DvidMakesThings/HW_PDNode-600-Pro/src/HardwareDesign/1.0.0/PDNode-600_Pro_Baseboard_100/jlcpcb/Documentation/_TopCover.pdf

# Baseboard Schematic Documentation

# Top Preview

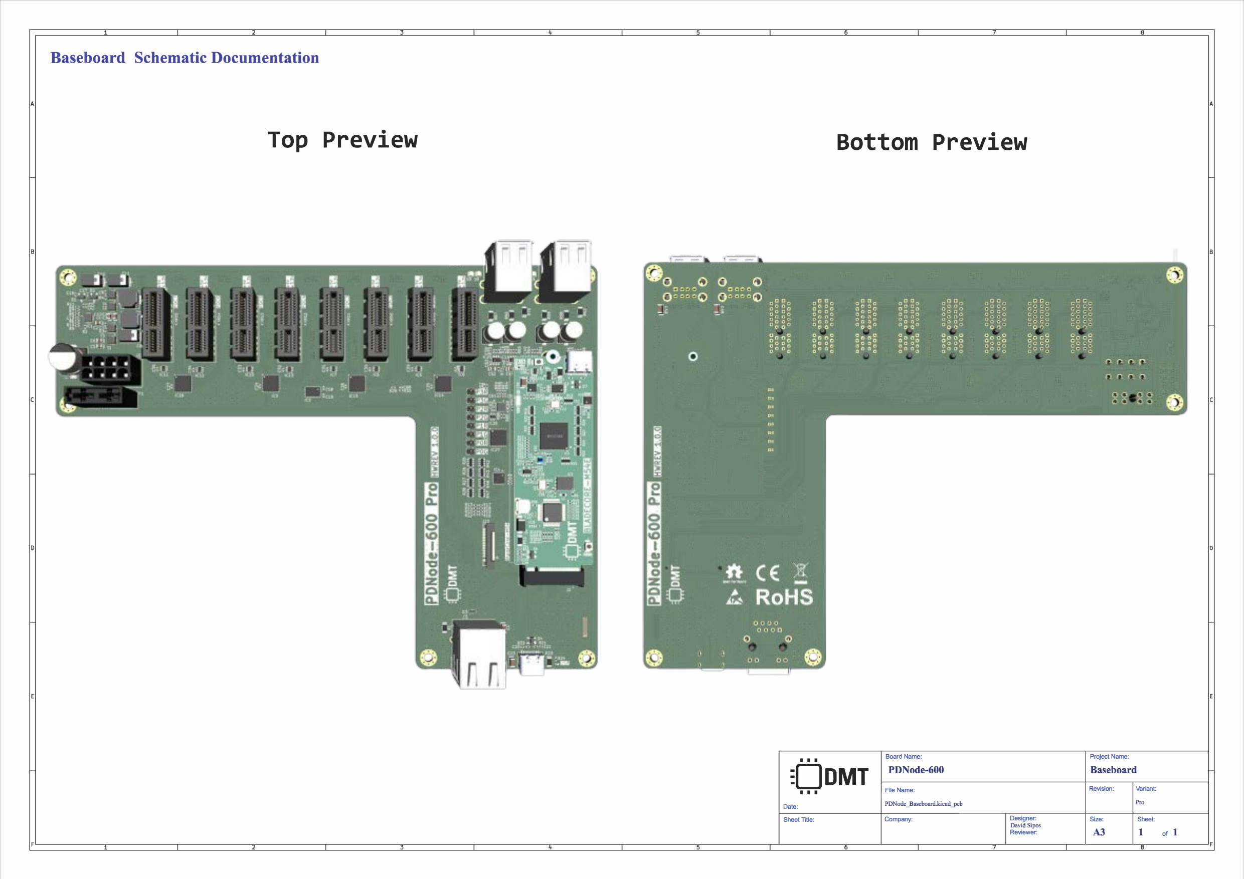
[picture p11: page 1]

2 | 3

A

C

2 | 3
6 | 7

# Bottom Preview

I I I

# :ODMT

I I I

Date:

Sheet Title:

6

Board Name:
PDNode-600

File Name:

PD Node_ Baseboard.kicad _pcb

Company:

7

Designer:
David Sipos
Reviewer:

A

B

D

Project Name:
Baseboard
Revision: | Variant:
| Pro
Size: | Sheet:
A3 | 1 | of 1

8
