DvidMakesThings/HW_PDNode-600-Pro/images/0.1.0/3D/PDNode-600 Pro-2.png

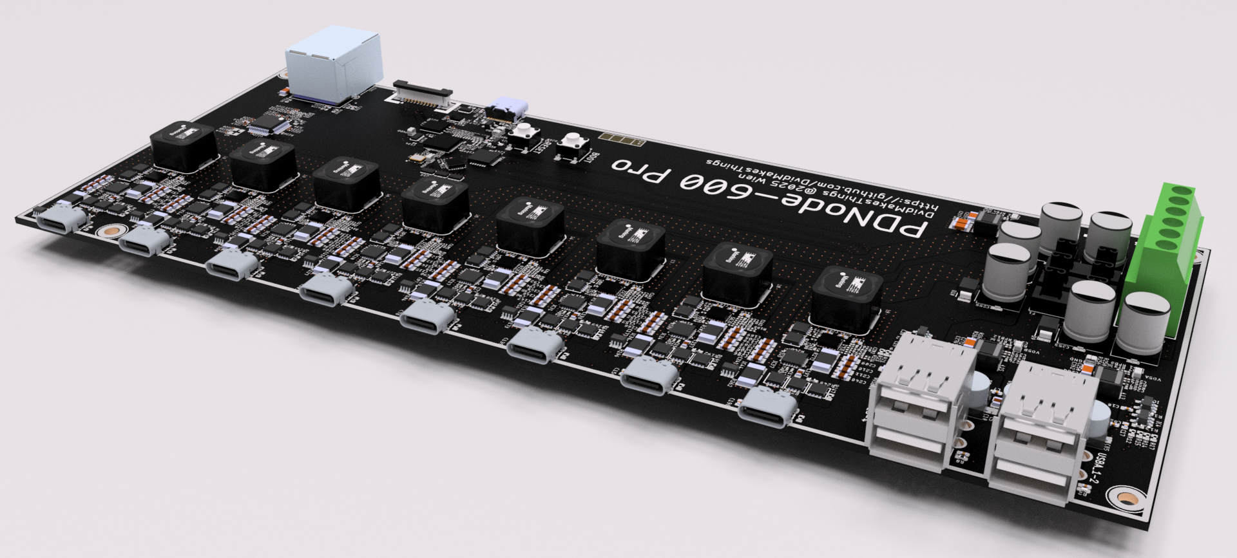
images/0.1.0/3D/PDNode-600 Pro-2.png
