DvidMakesThings/HW_PDNode-600-Pro/images/0.1.0/PDNode-600 Pro-Btm.png

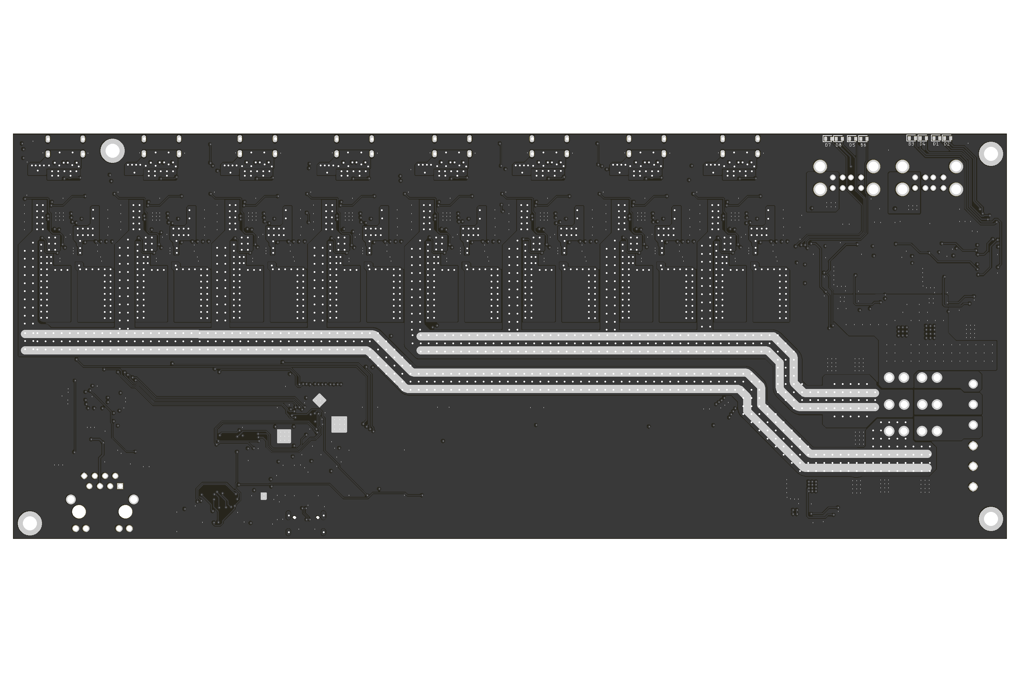
images/0.1.0/PDNode-600 Pro-Btm.png
