DvidMakesThings/HW_PDNode-600-Pro/images/1.0.0/BladeCore-M54E_Top.png

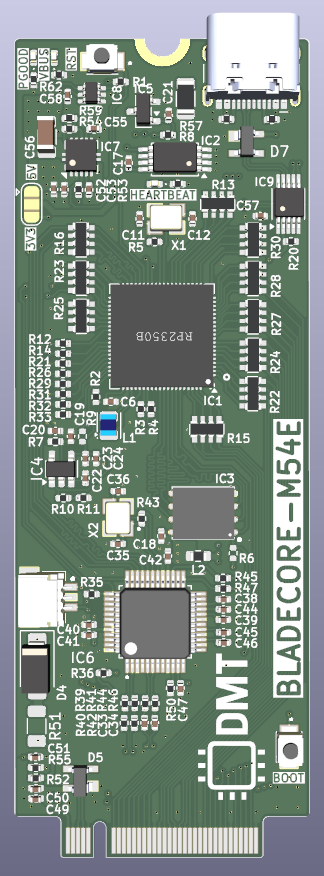
images/1.0.0/BladeCore-M54E_Top.png
