DvidMakesThings/HW_PDNode-600-Pro/images/PDNode-600 Pro Enclosure v19.png

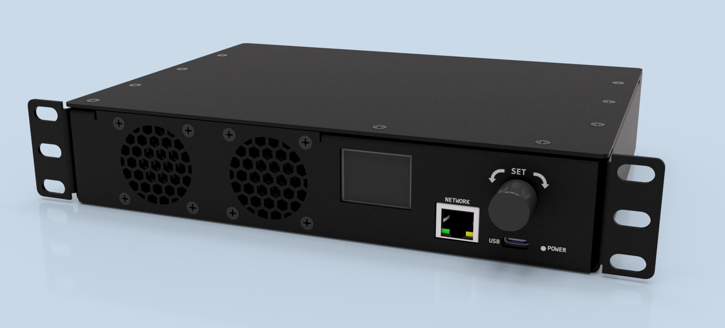
images/PDNode-600 Pro Enclosure v19.png
