DvidMakesThings/HW_PDNode-600-Pro/images/PDNode-600 Pro Enclosure v162.png

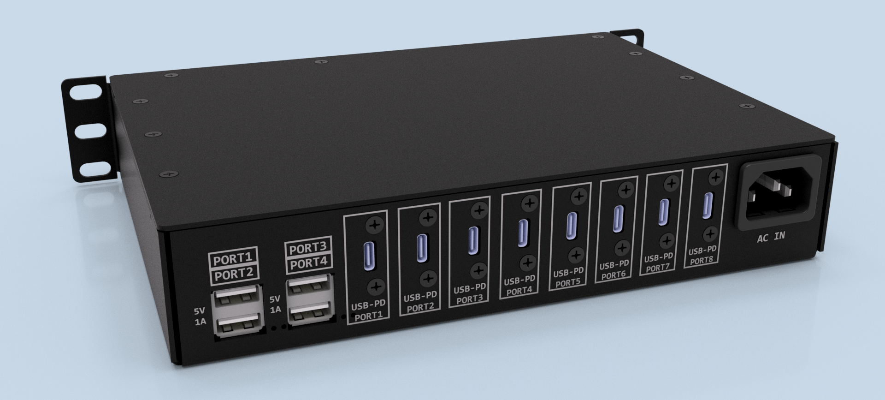
images/PDNode-600 Pro Enclosure v162.png
