DvidMakesThings/HW_PDNode-600-Pro/src/HardwareDesign/1.0.0/BladeCore-M54_100/Images/BladeCore-M54E_Top-removebg.png

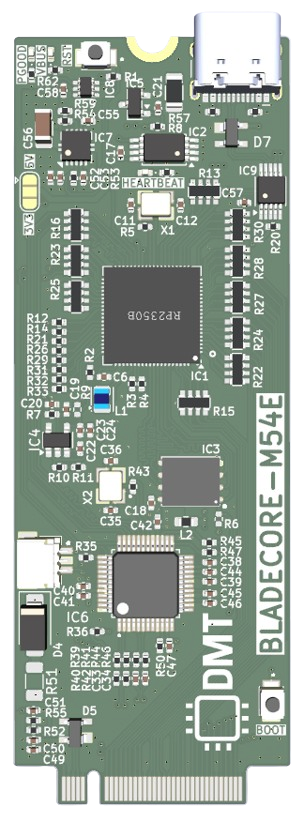
src/HardwareDesign/1.0.0/BladeCore-M54_100/Images/BladeCore-M54E_Top-removebg.png
