DvidMakesThings/HW_PDNode-600-Pro/src/HardwareDesign/1.0.0/PDCard-4242_100/Images/PDNode-PDCard-4242_TOP-removebg-preview.png

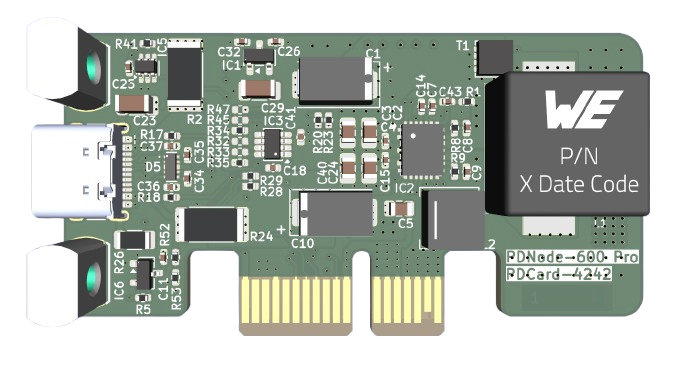
src/HardwareDesign/1.0.0/PDCard-4242_100/Images/PDNode-PDCard-4242_TOP-removebg-preview.png
