DvidMakesThings/HW_PDNode-600-Pro/src/HardwareDesign/1.0.0/PDNode-600_Pro_Baseboard_100/Images/PDNode_Baseboard-Bottom.png

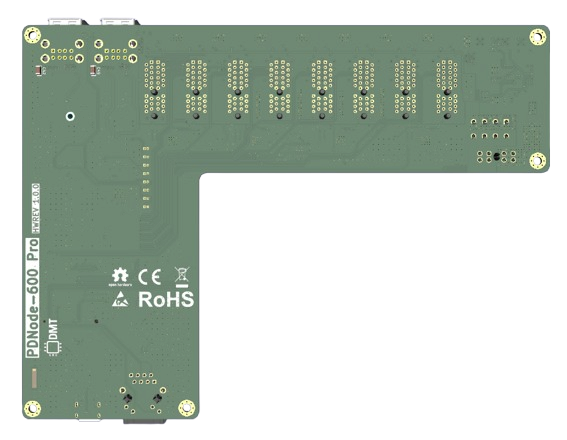
src/HardwareDesign/1.0.0/PDNode-600_Pro_Baseboard_100/Images/PDNode_Baseboard-Bottom.png
