DvidMakesThings/HW_PDNode-600-Pro/src/PDF/SCH_PDCard-4242_100.pdf

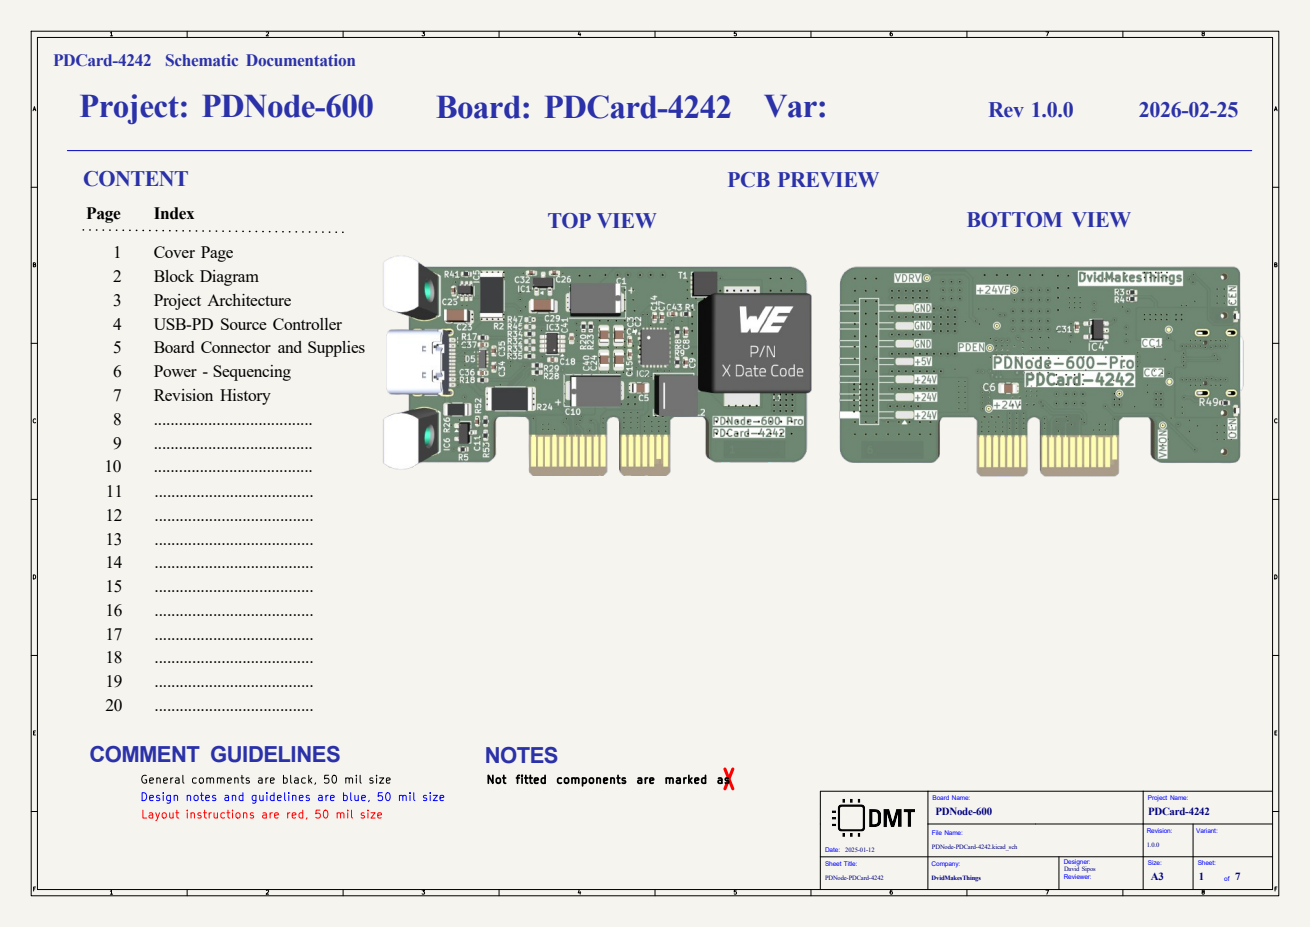
[picture p39: page 1]

...................................... Design notes and guidelines are blue, 50 mil size

General comments are black, 50 mil size

Layout instructions are red, 50 mil size

File Name: Sheet Title: PDNode-PDCard-4242

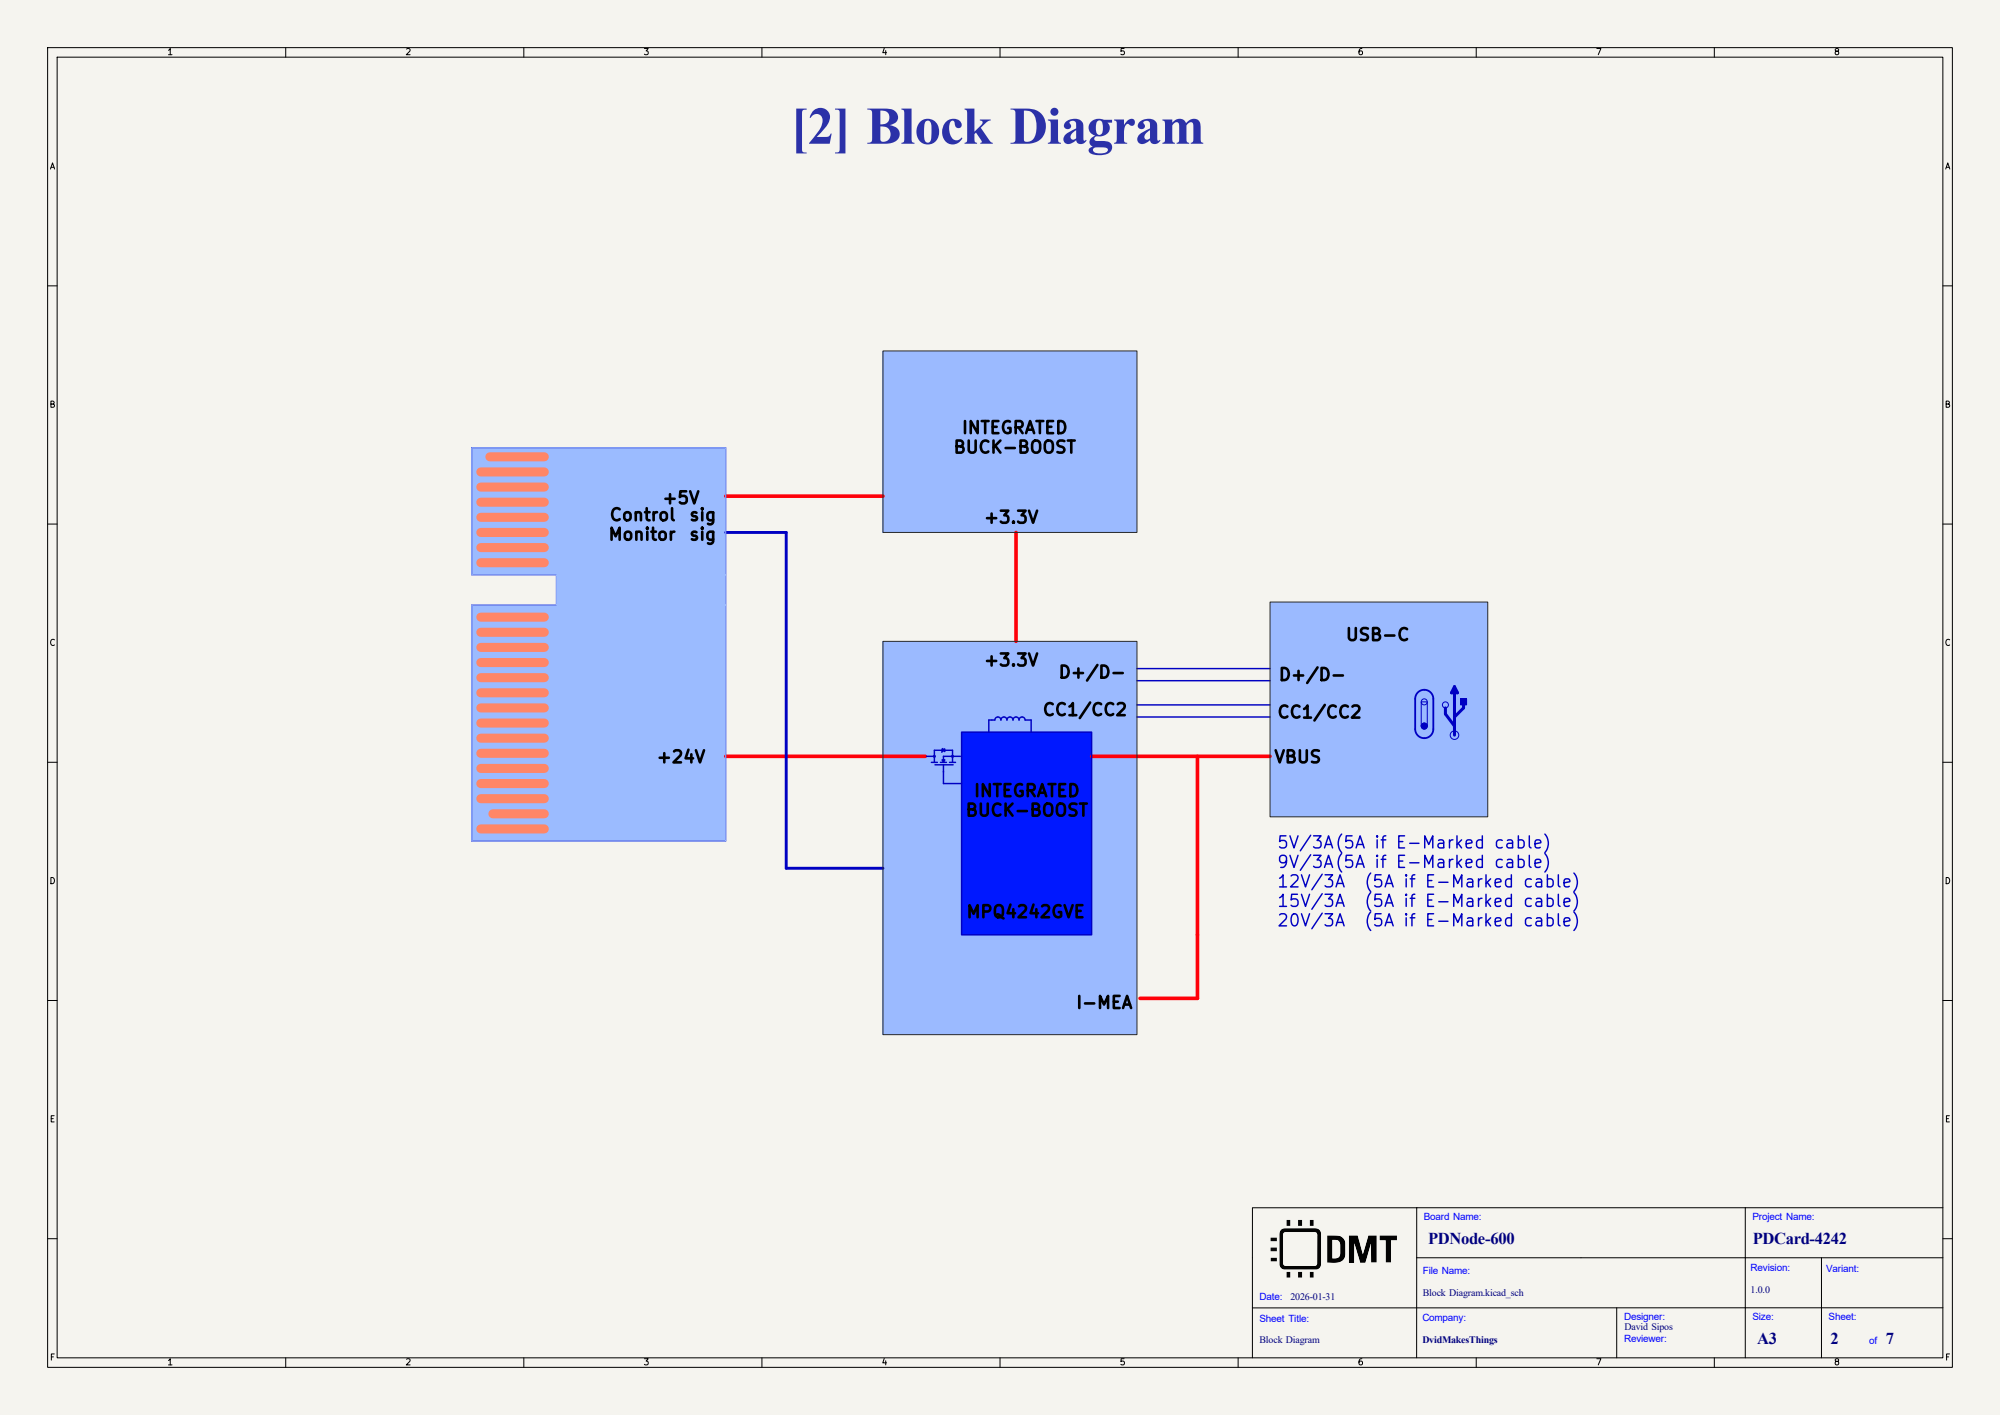
[picture p40: page 2]

File Name: Sheet Title: Block Diagram

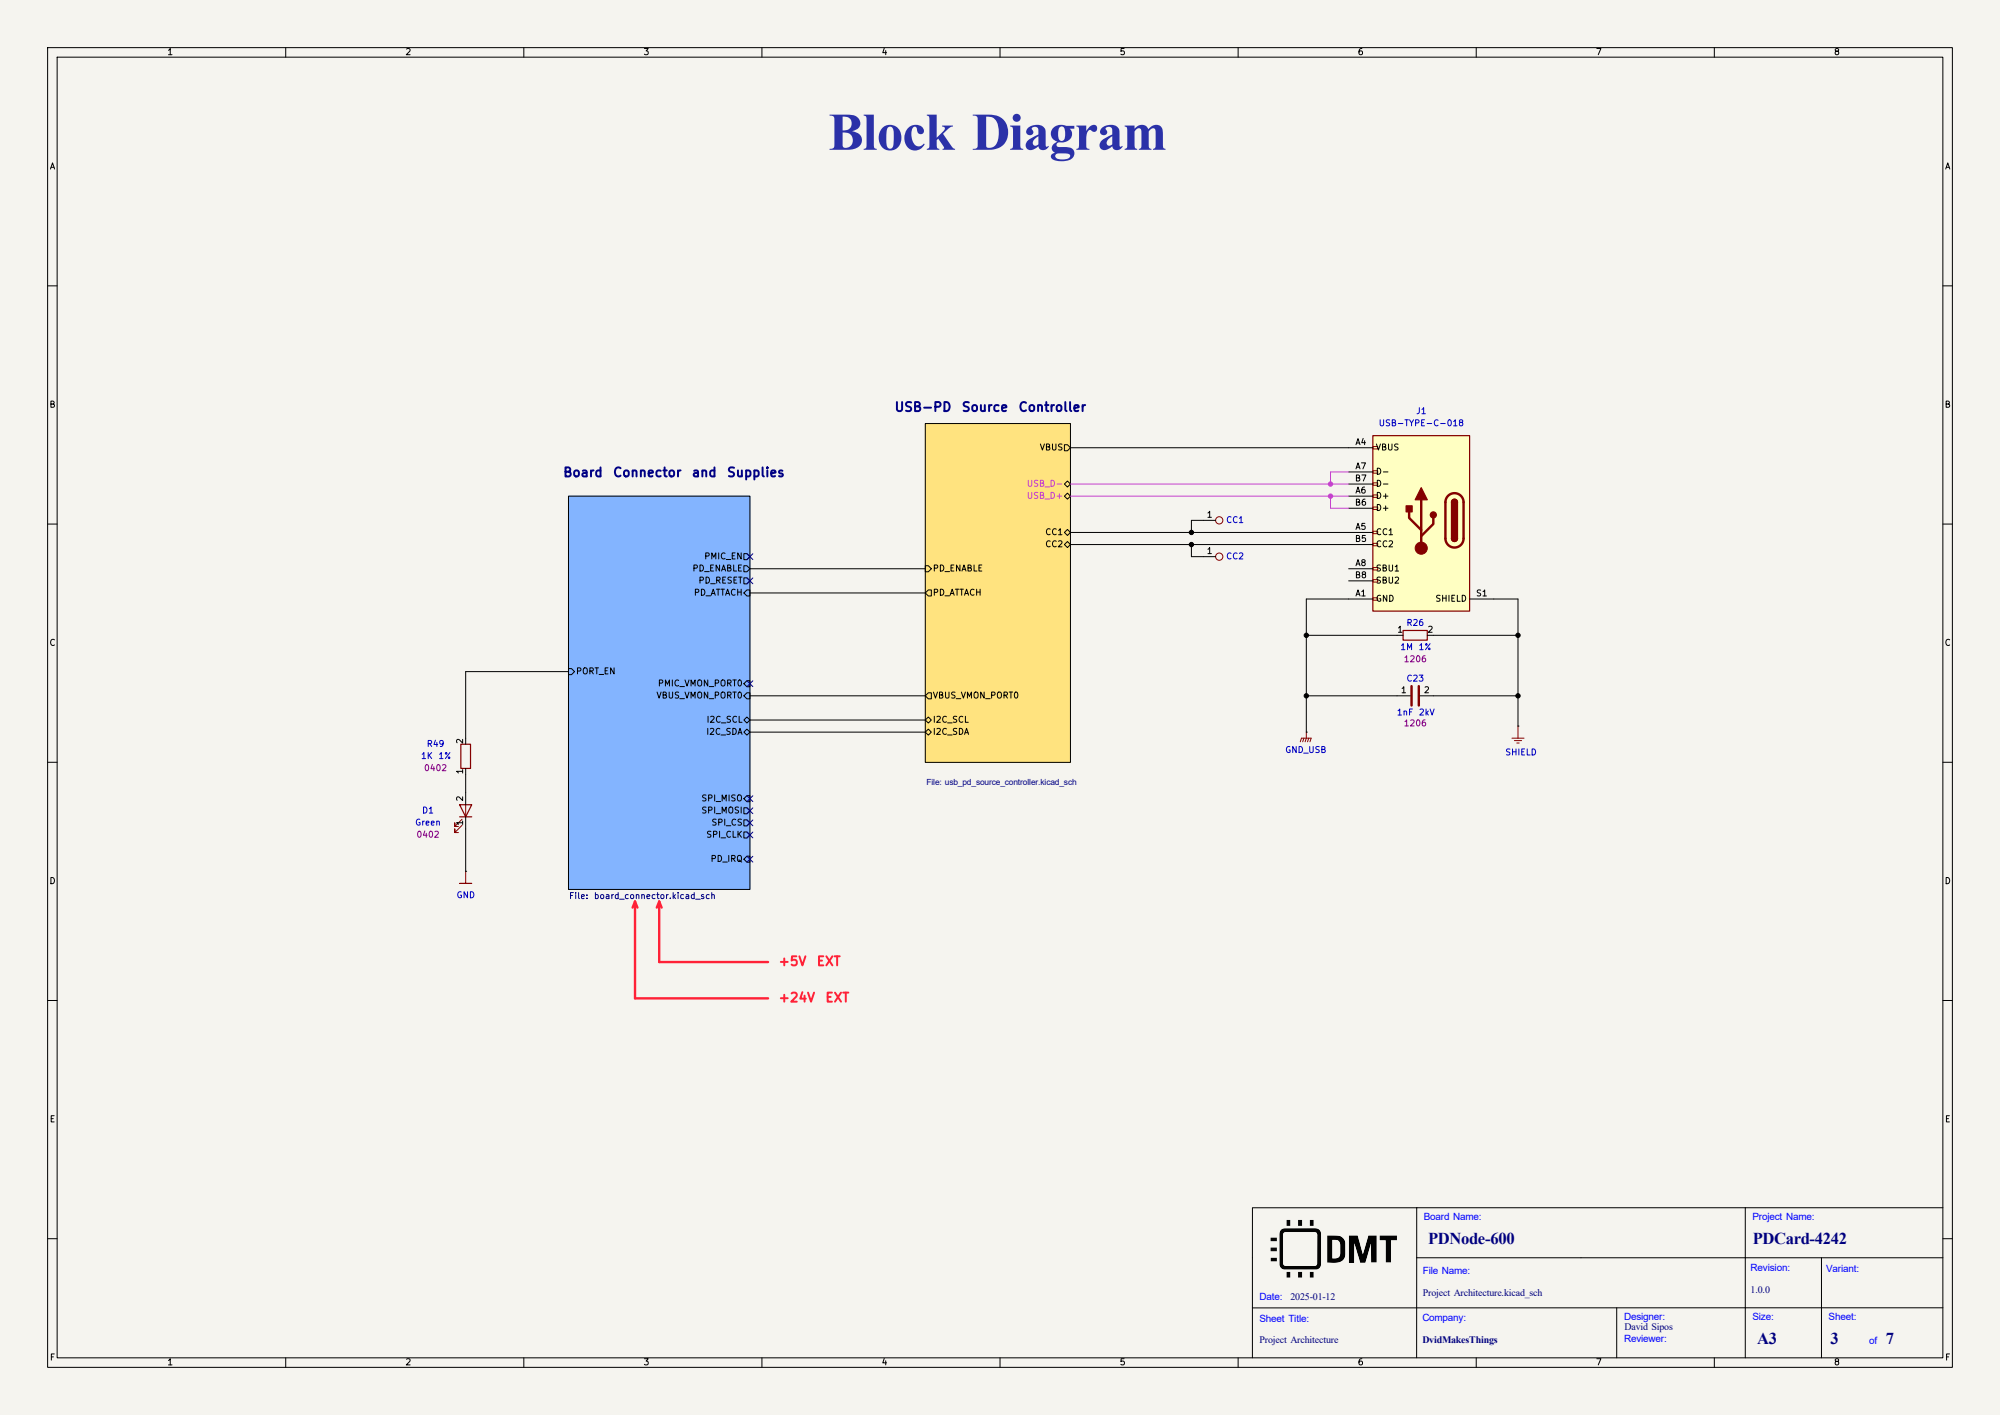
[picture p41: page 3]

VBUS_VMON_PORT0 USB-PD Source Controller

PD_ENABLE Board Connector and Supplies

File Name: Sheet Title: Project Architecture

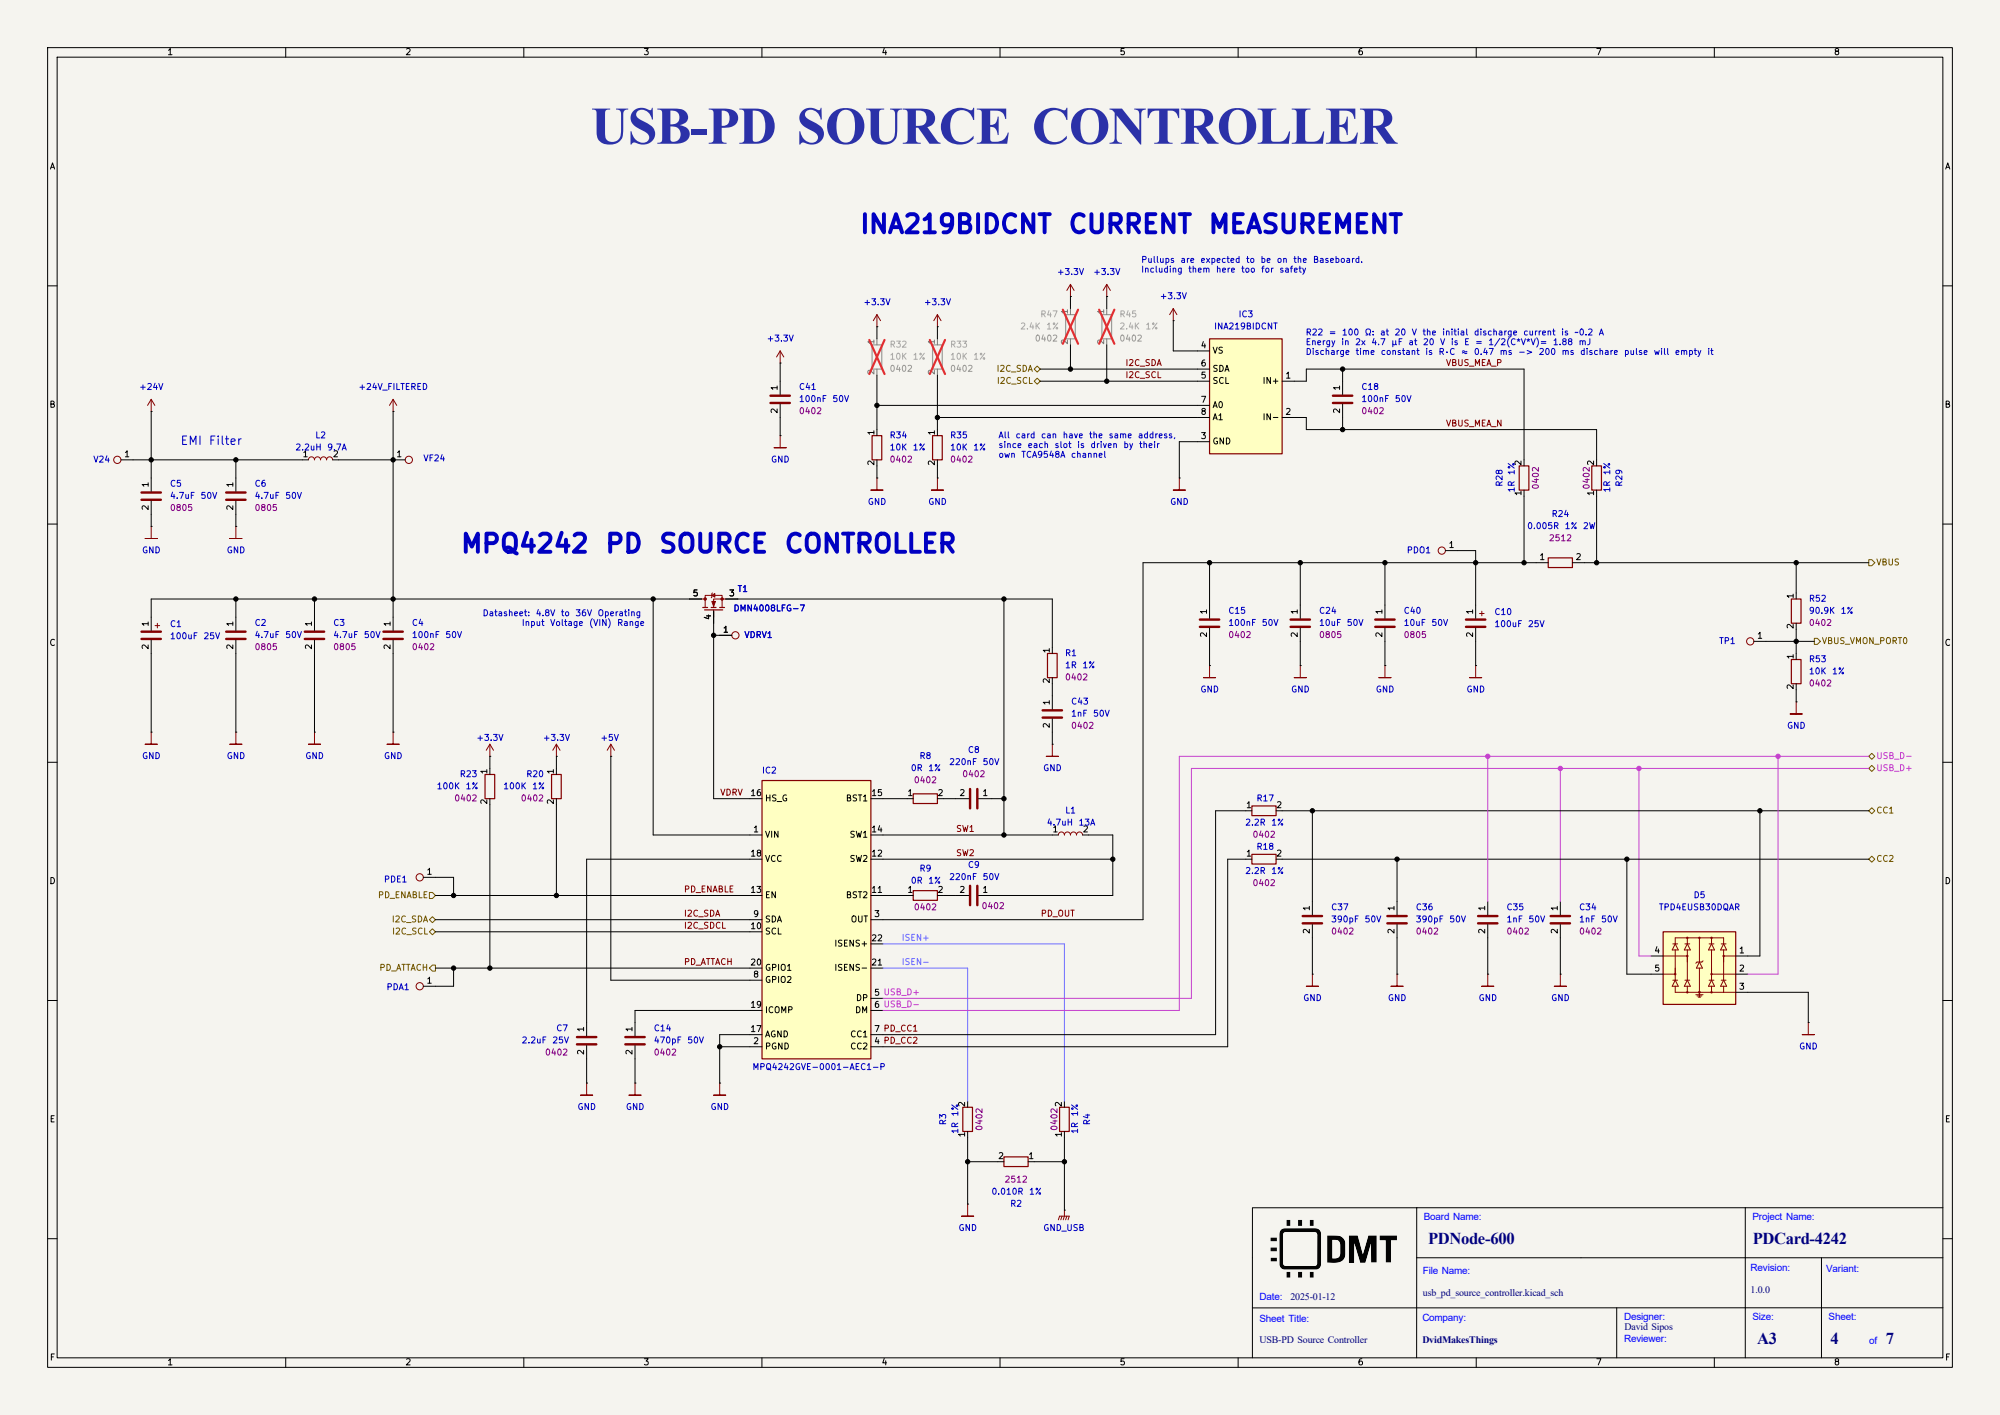
[picture p42: page 4]

R22 = 100 Ω: at 20 V the initial discharge current is ~0.2 A Energy in 2x 4.7 µF at 20 V is E = 1/2(C*V*V)= 1.88 mJ Discharge time constant is R·C ≈ 0.47 ms -> 200 ms dischare pulse will empty it INA219BIDCNT CURRENT MEASUREMENT

Pullups are expected to be on the Baseboard.
Including them here too for safety

All card can have the same address, since each slot is driven by their own TCA9548A channel EMI Filter

Input Voltage (VIN) Range
IC2 MPQ4242GVE-0001-AEC1-P

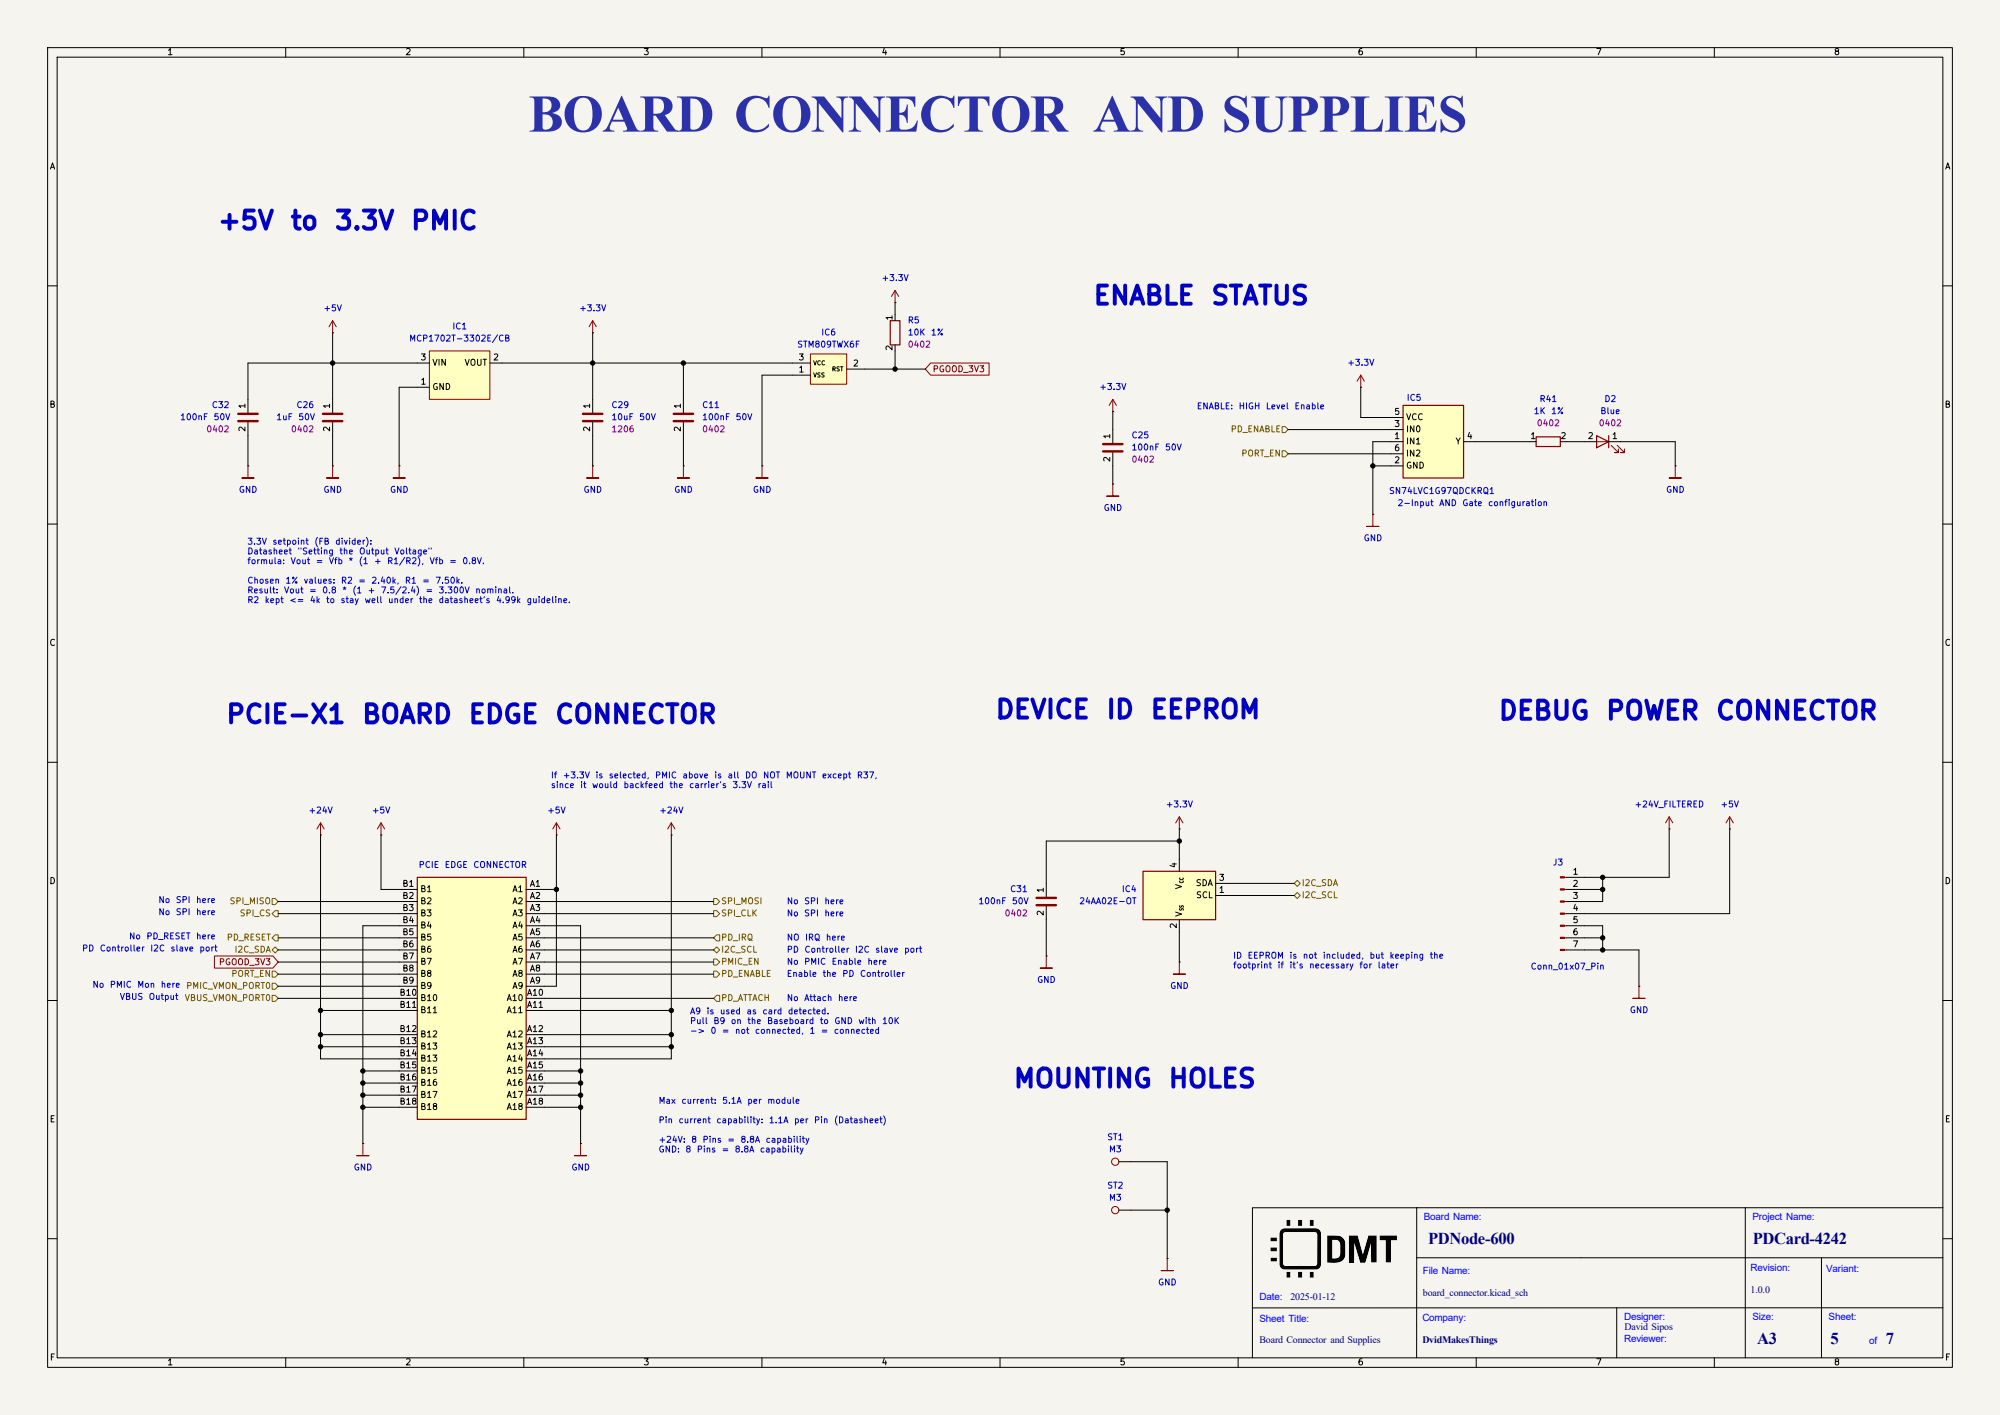
[picture p43: page 5]

ENABLE: HIGH Level Enable PD Controller I2C slave port

2-Input AND Gate configuration

NO IRQ here 3.3V setpoint (FB divider):
Datasheet "Setting the Output Voltage"
formula: Vout = Vfb * (1 + R1/R2), Vfb = 0.8V.

Chosen 1% values: R2 = 2.40k, R1 = 7.50k.
Result: Vout = 0.8 * (1 + 7.5/2.4) = 3.300V nominal.
R2 kept <= 4k to stay well under the datasheet's 4.99k guideline.

footprint if it's necessary for later DEVICE ID EEPROM

No SPI here No PD_RESET here PD Controller I2C slave port

No PMIC Mon here

A9 is used as card detected. Pull B9 on the Baseboard to GND with 10K -> 0 = not connected, 1 = connected Max current: 5.1A per module Pin current capability: 1.1A per Pin (Datasheet)

File Name: Sheet Title: Board Connector and Supplies

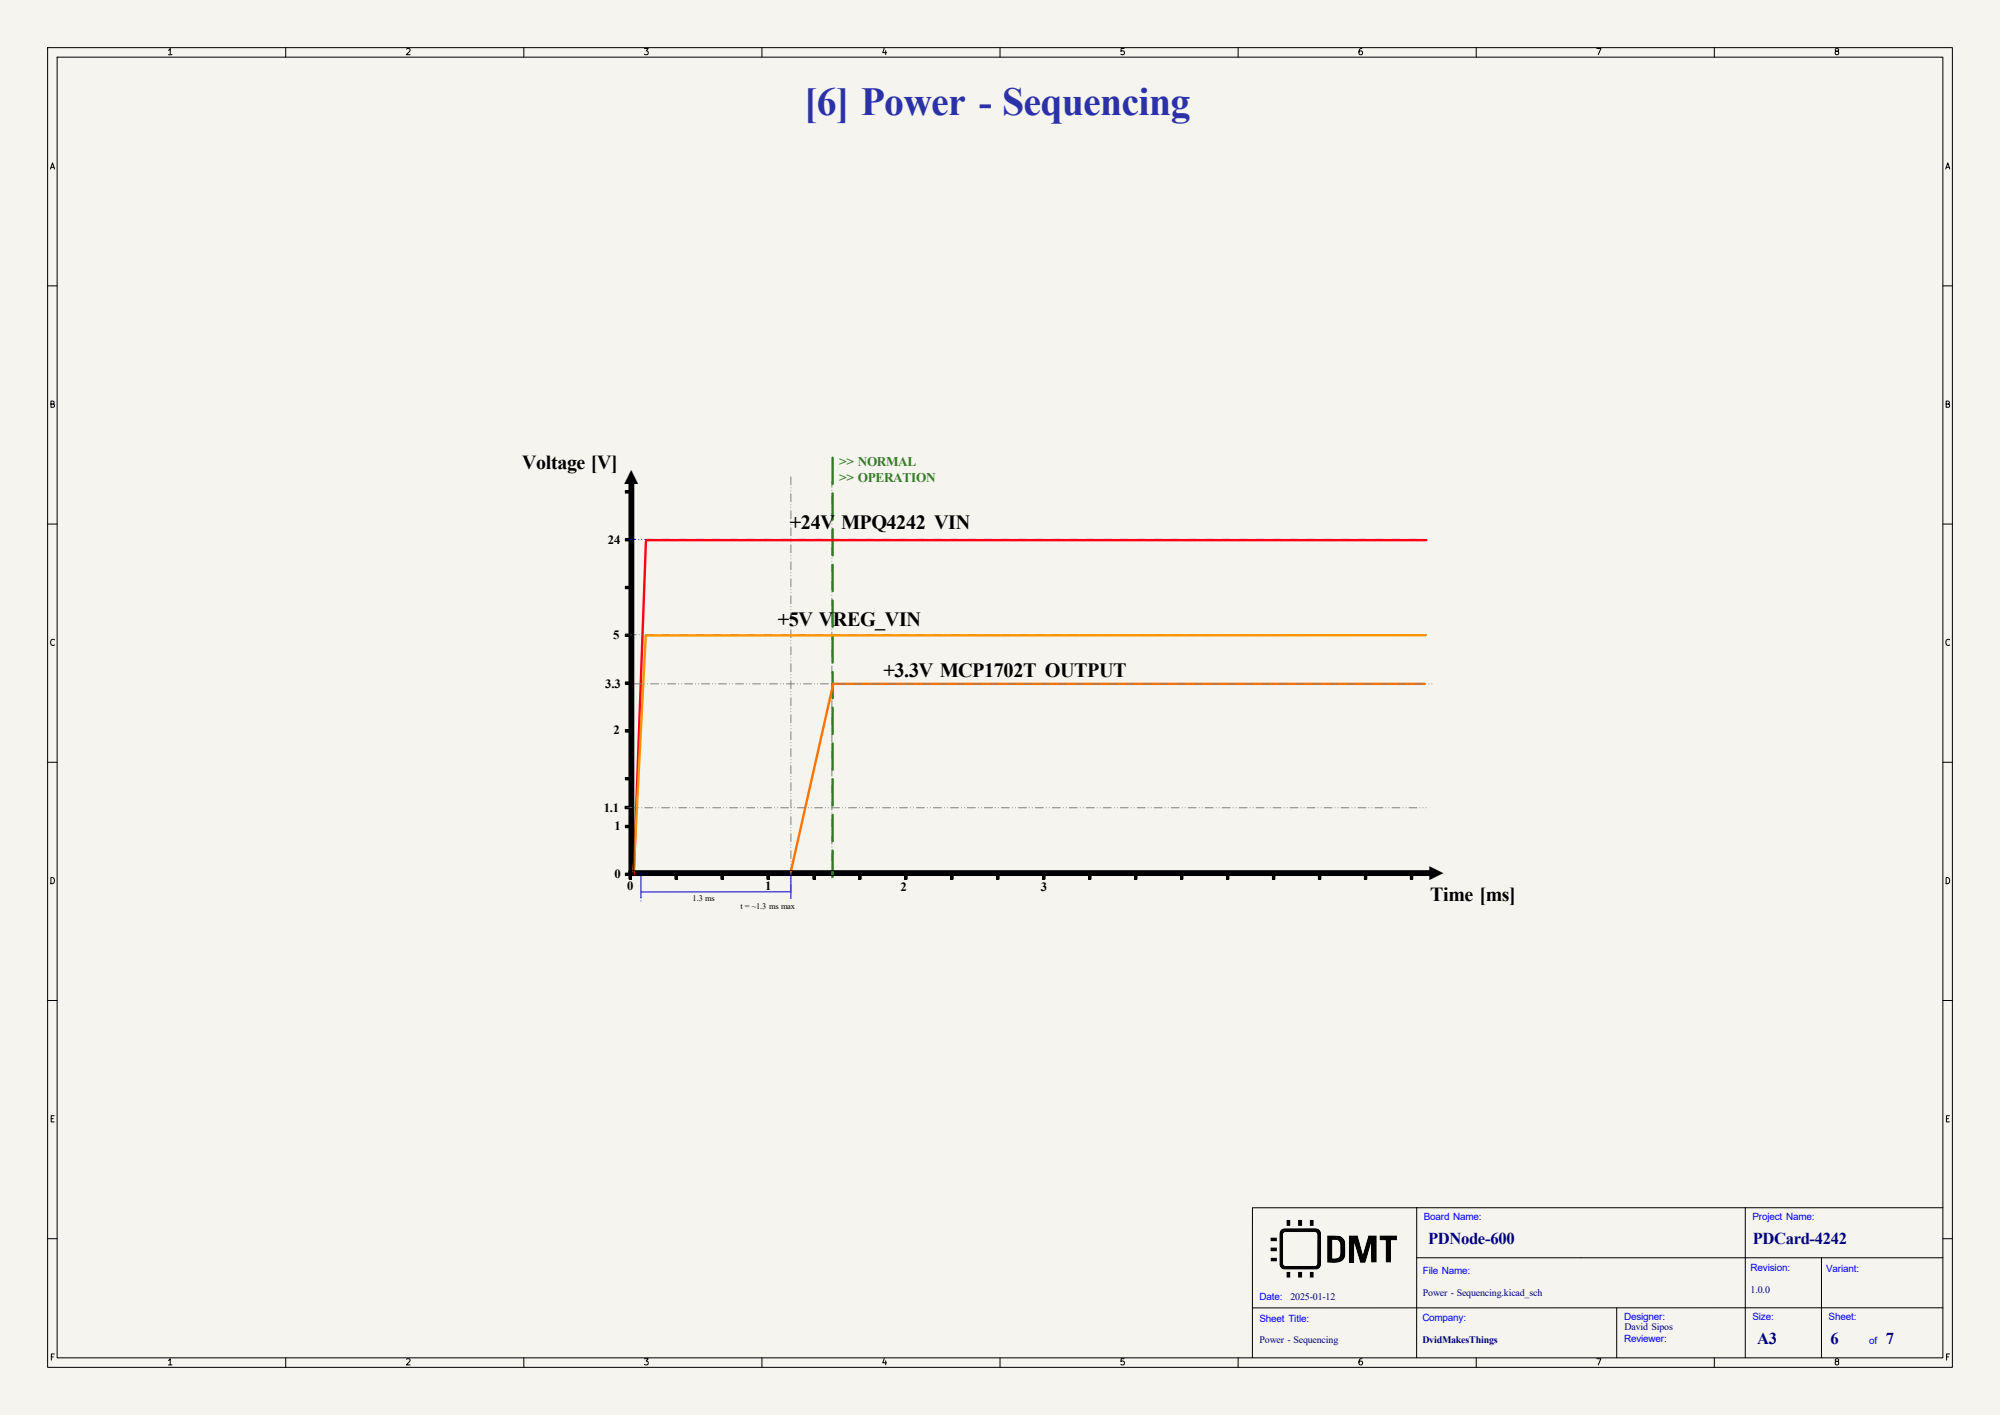
[picture p44: page 6]

File Name: Sheet Title: Power - Sequencing

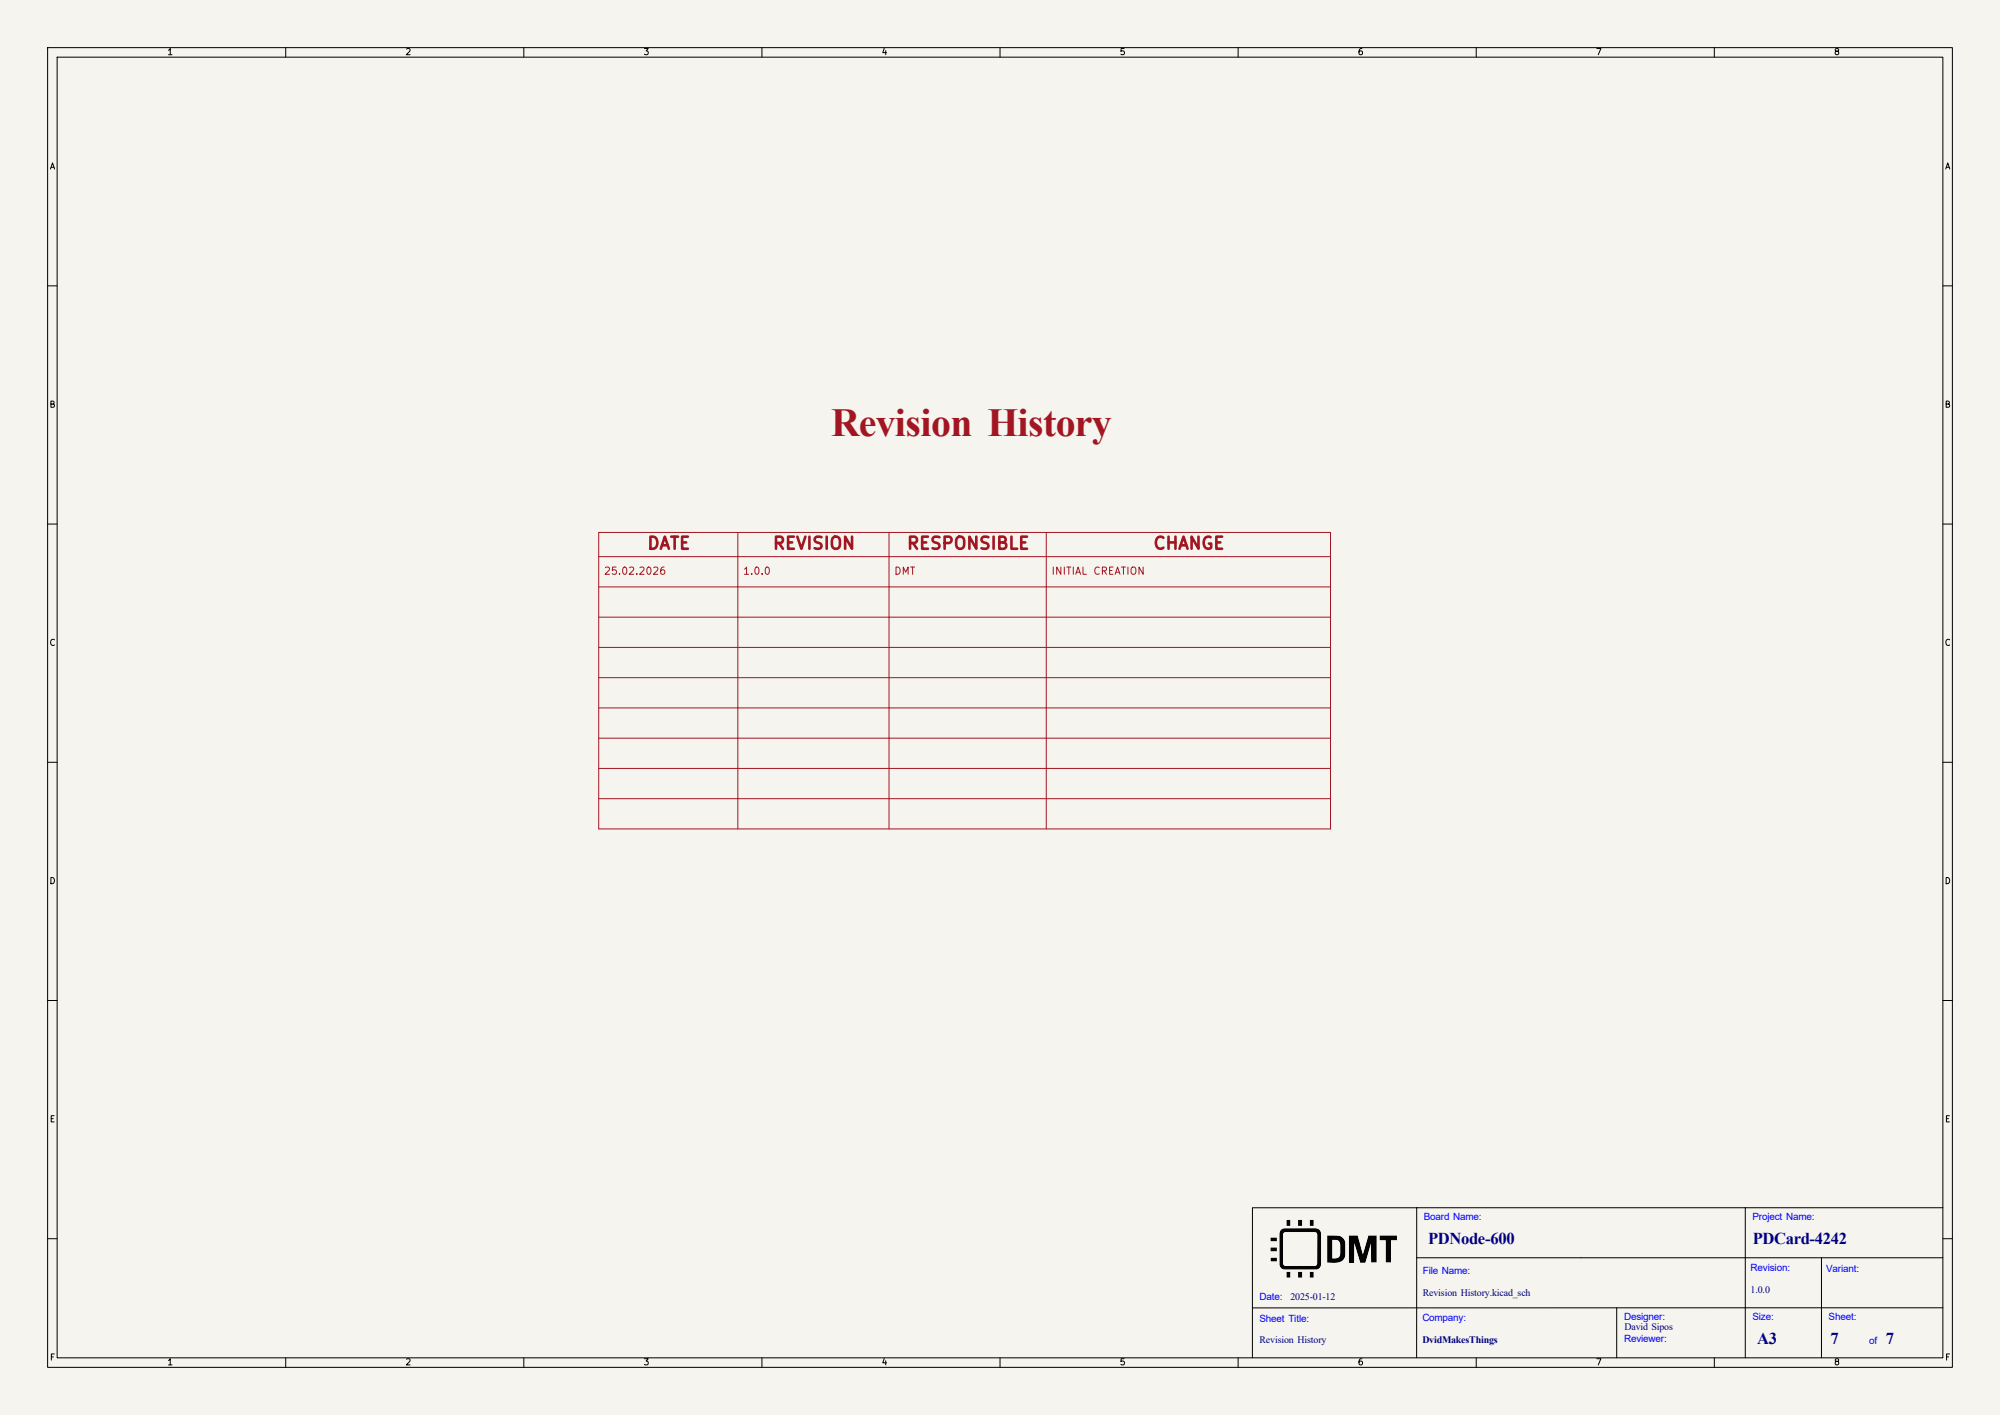
[picture p45: page 7]

File Name: Sheet Title: Revision History
