DvidMakesThings/HW_PDNode-600-Pro/src/PDF/SCH_PDNode_Baseboard_100.pdf

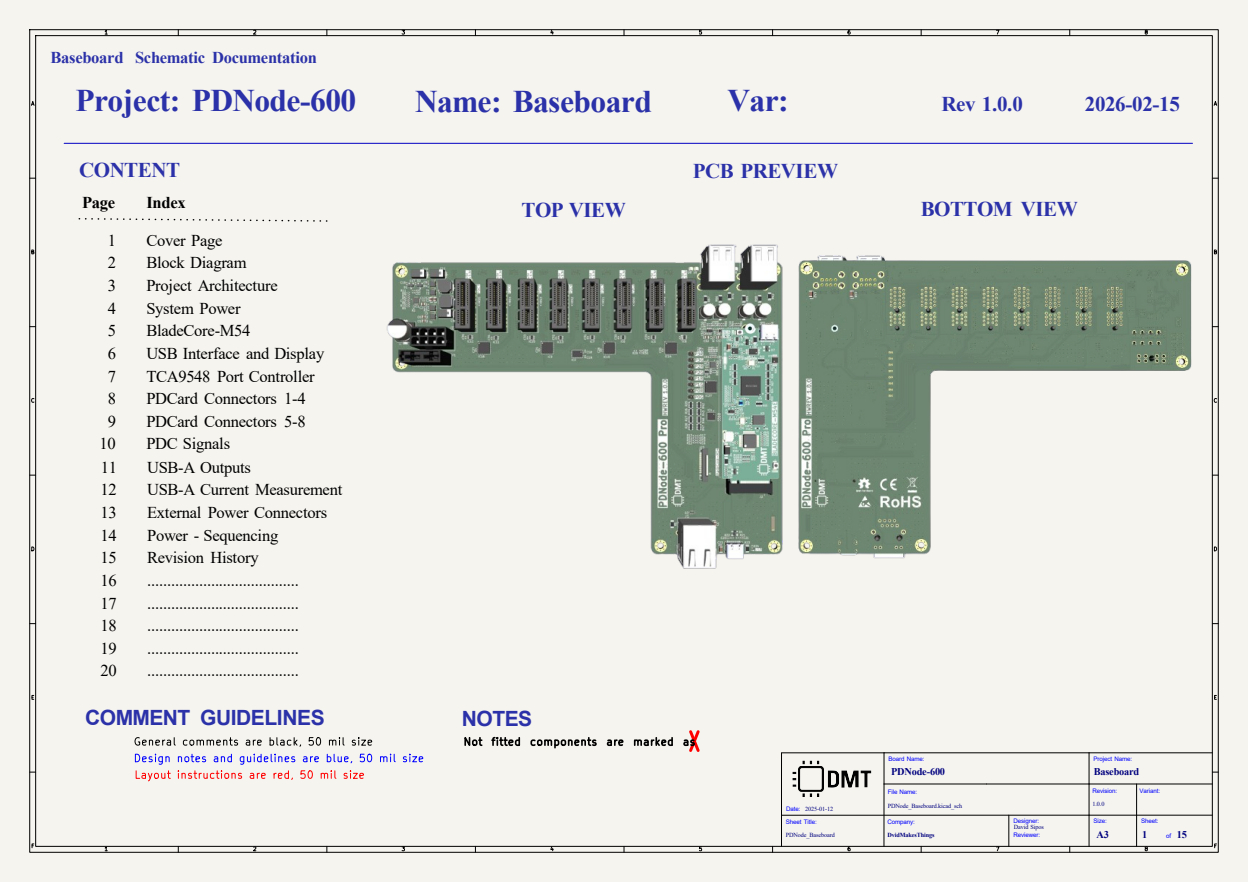
[picture p46: page 1]

General comments are black, 50 mil size
Design notes and guidelines are blue, 50 mil size
Layout instructions are red, 50 mil size

Not fitted components are marked as

File Name: Sheet Title: PDNode_Baseboard

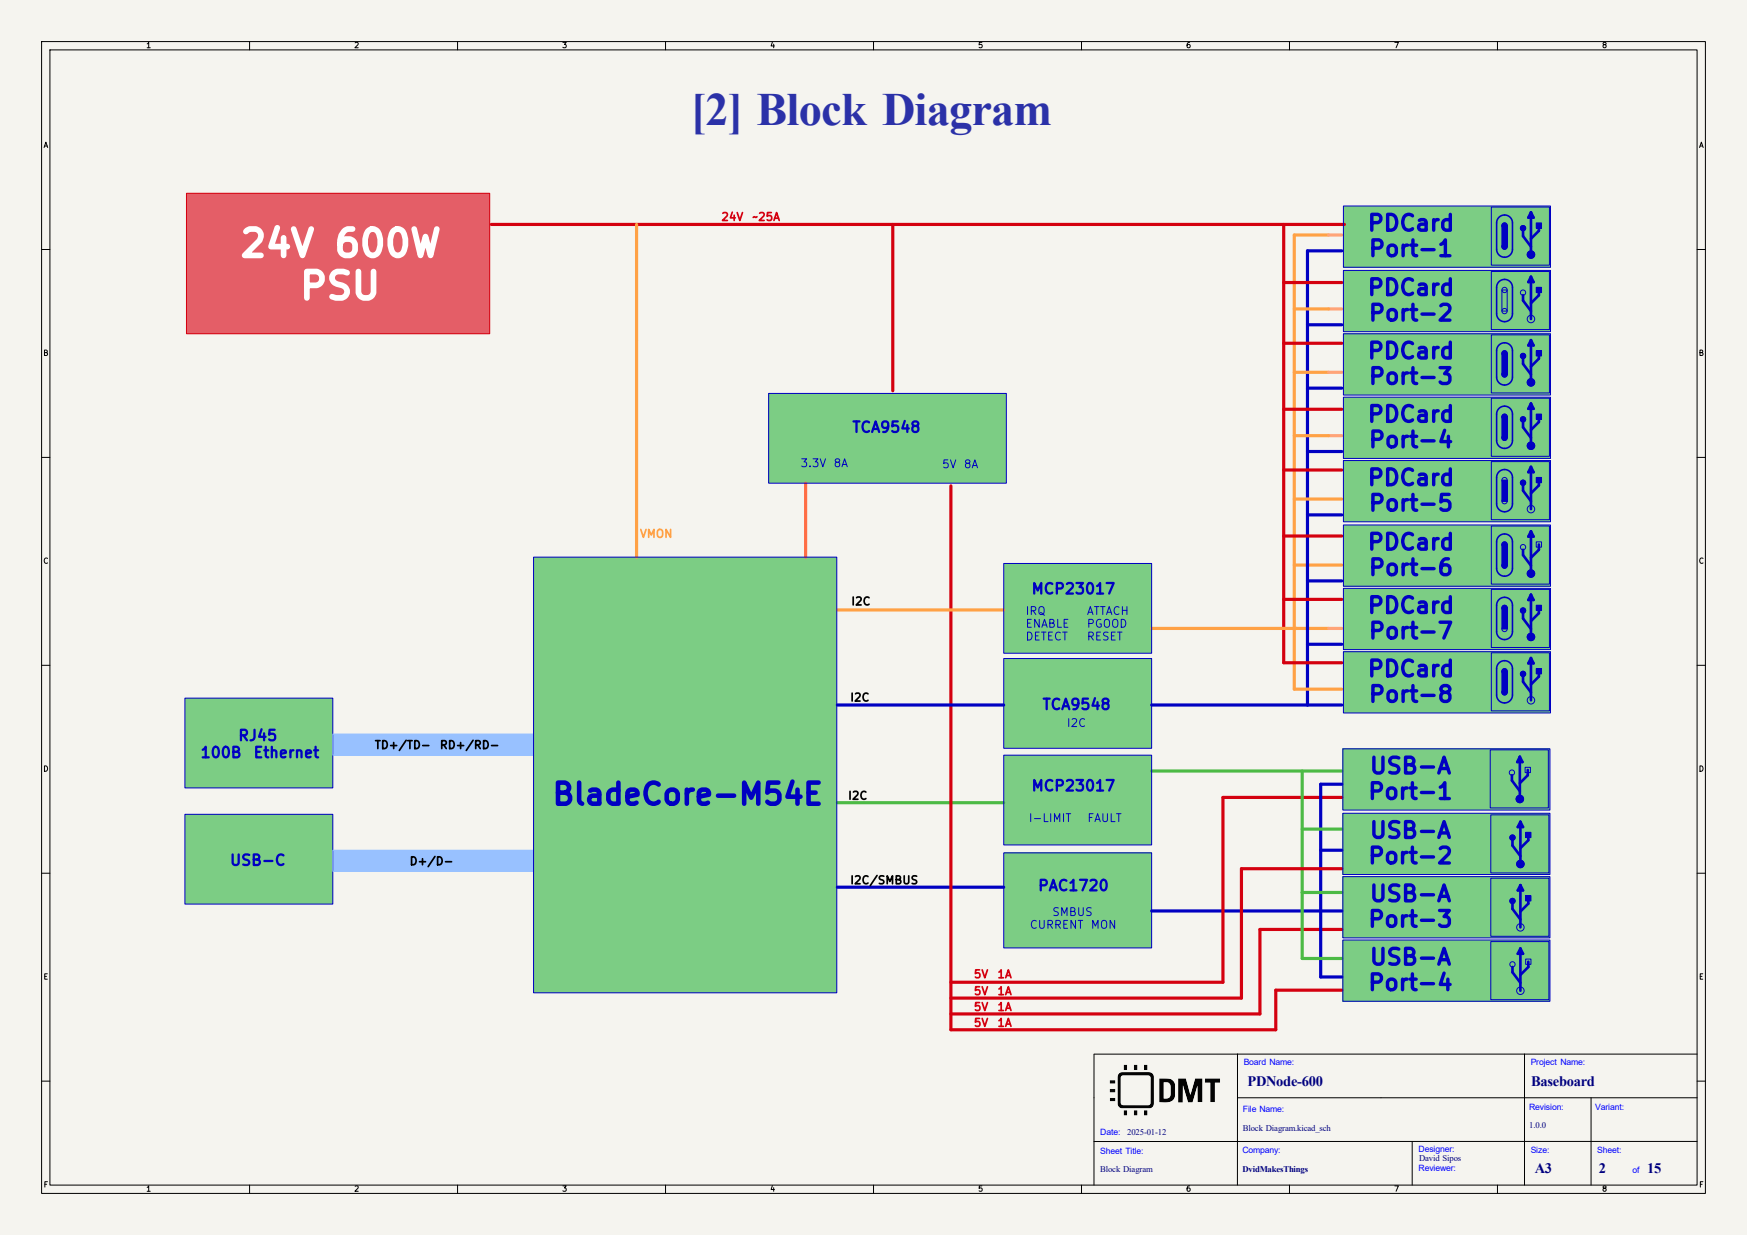
[picture p47: page 2]

PDCard Port-1

PDCard Port-2

PDCard Port-3

PDCard Port-4

PDCard Port-5

PDCard Port-6

PDCard Port-7

PDCard Port-8

I2C/SMBUS

USB-A Port-3

USB-A Port-4

File Name: Sheet Title: Block Diagram

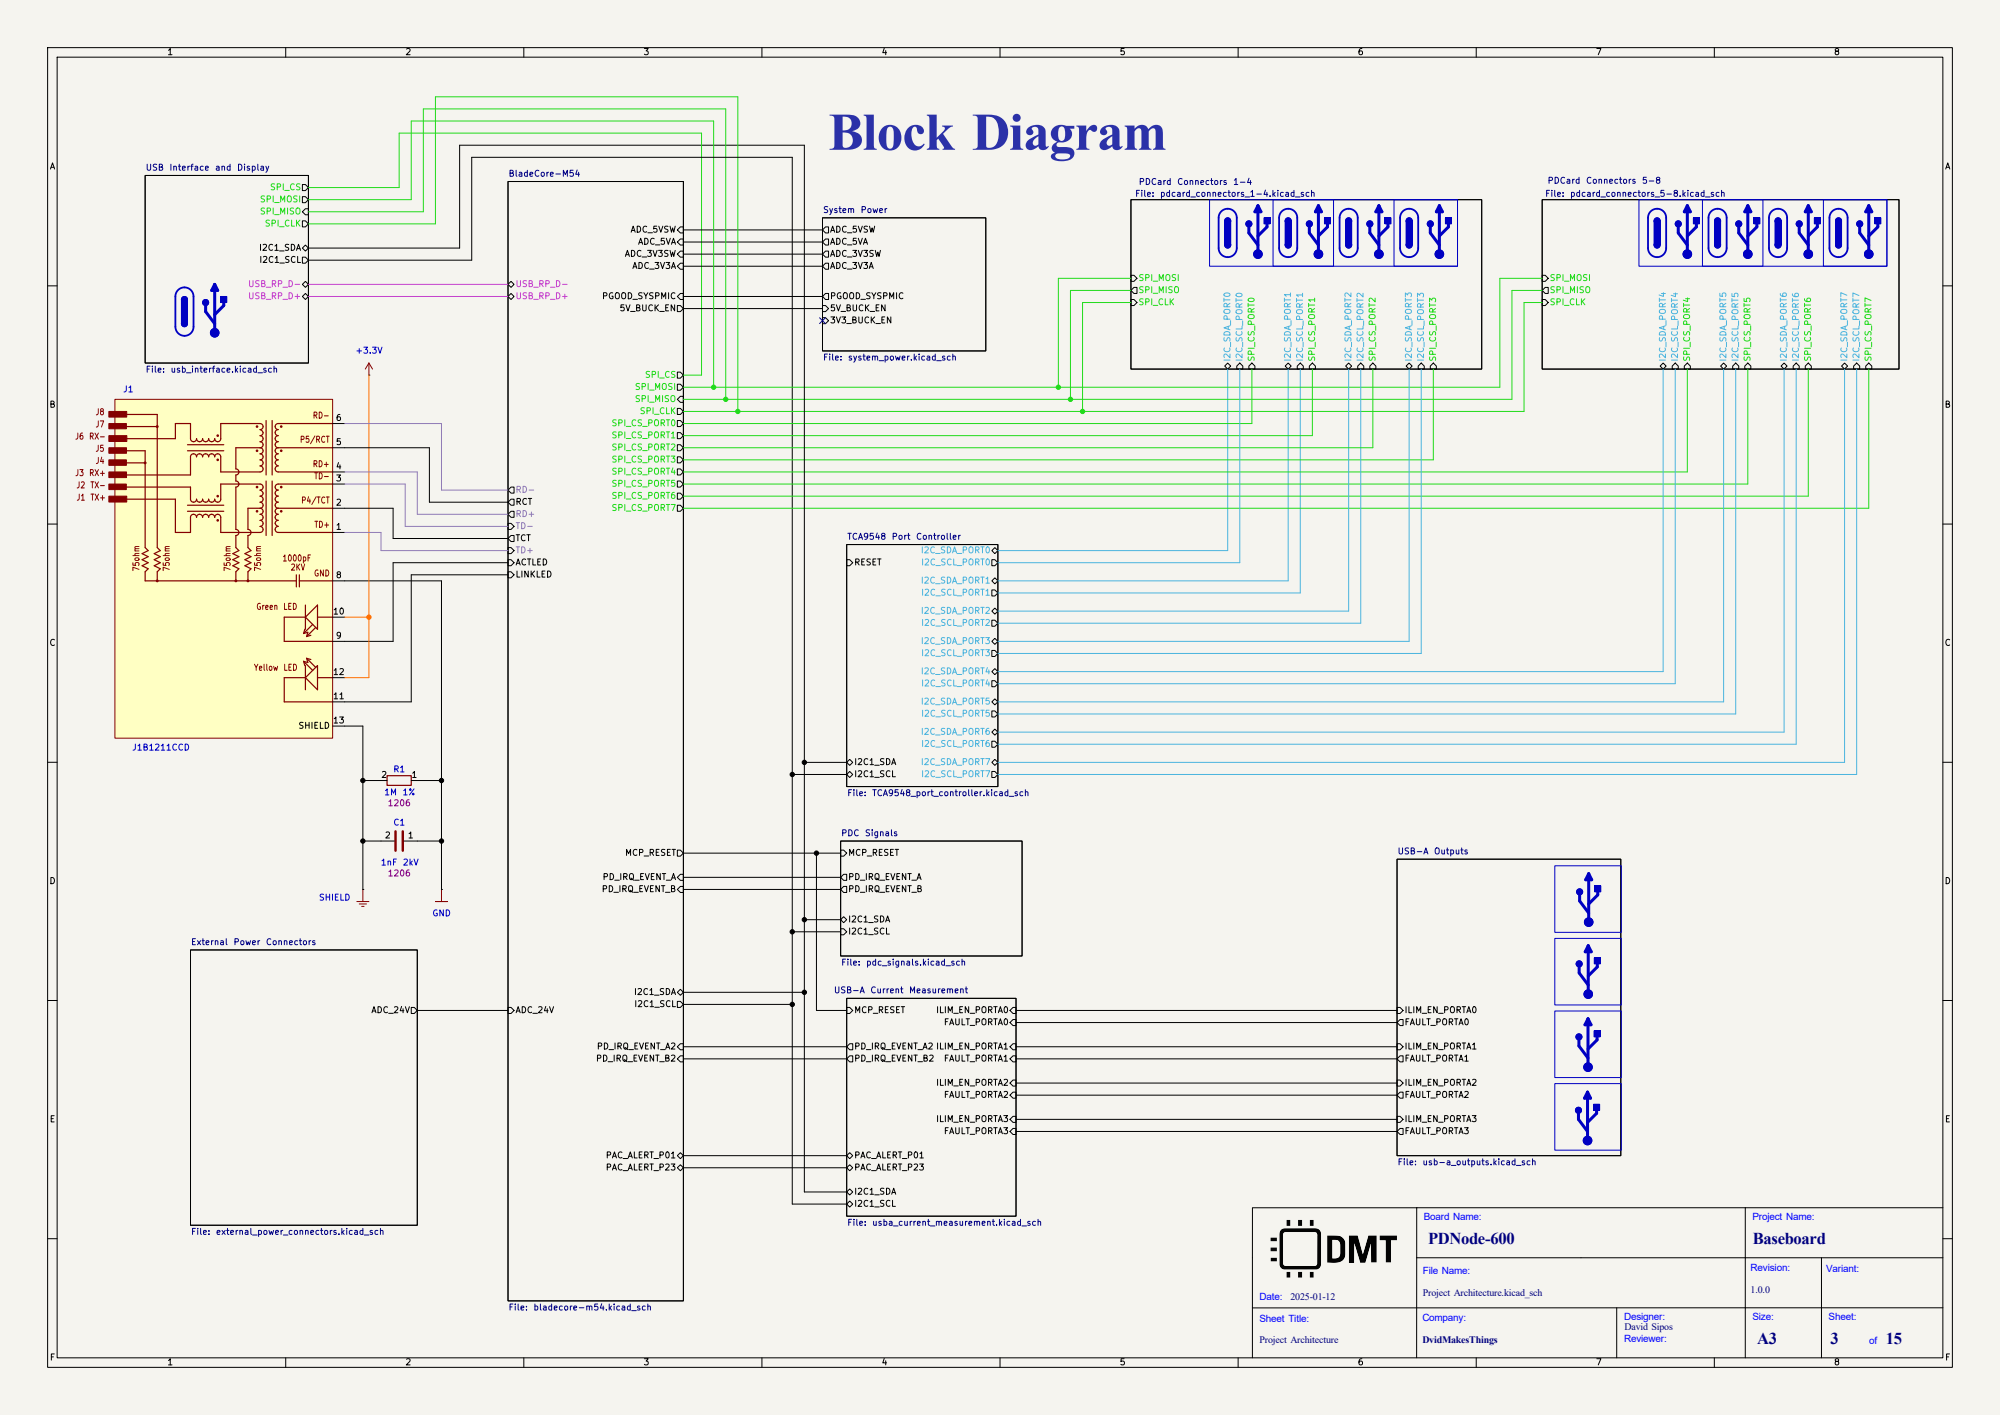
[picture p48: page 3]

SPI_MOSI USB Interface and Display

PD_IRQ_EVENT_A
I2C1_SDA MCP_RESET PD_IRQ_EVENT_A2 PD_IRQ_EVENT_B2 USB-A Current Measurement File: usba_current_measurement.kicad_sch PD_IRQ_EVENT_B

ADC_24V External Power Connectors File: external_power_connectors.kicad_sch

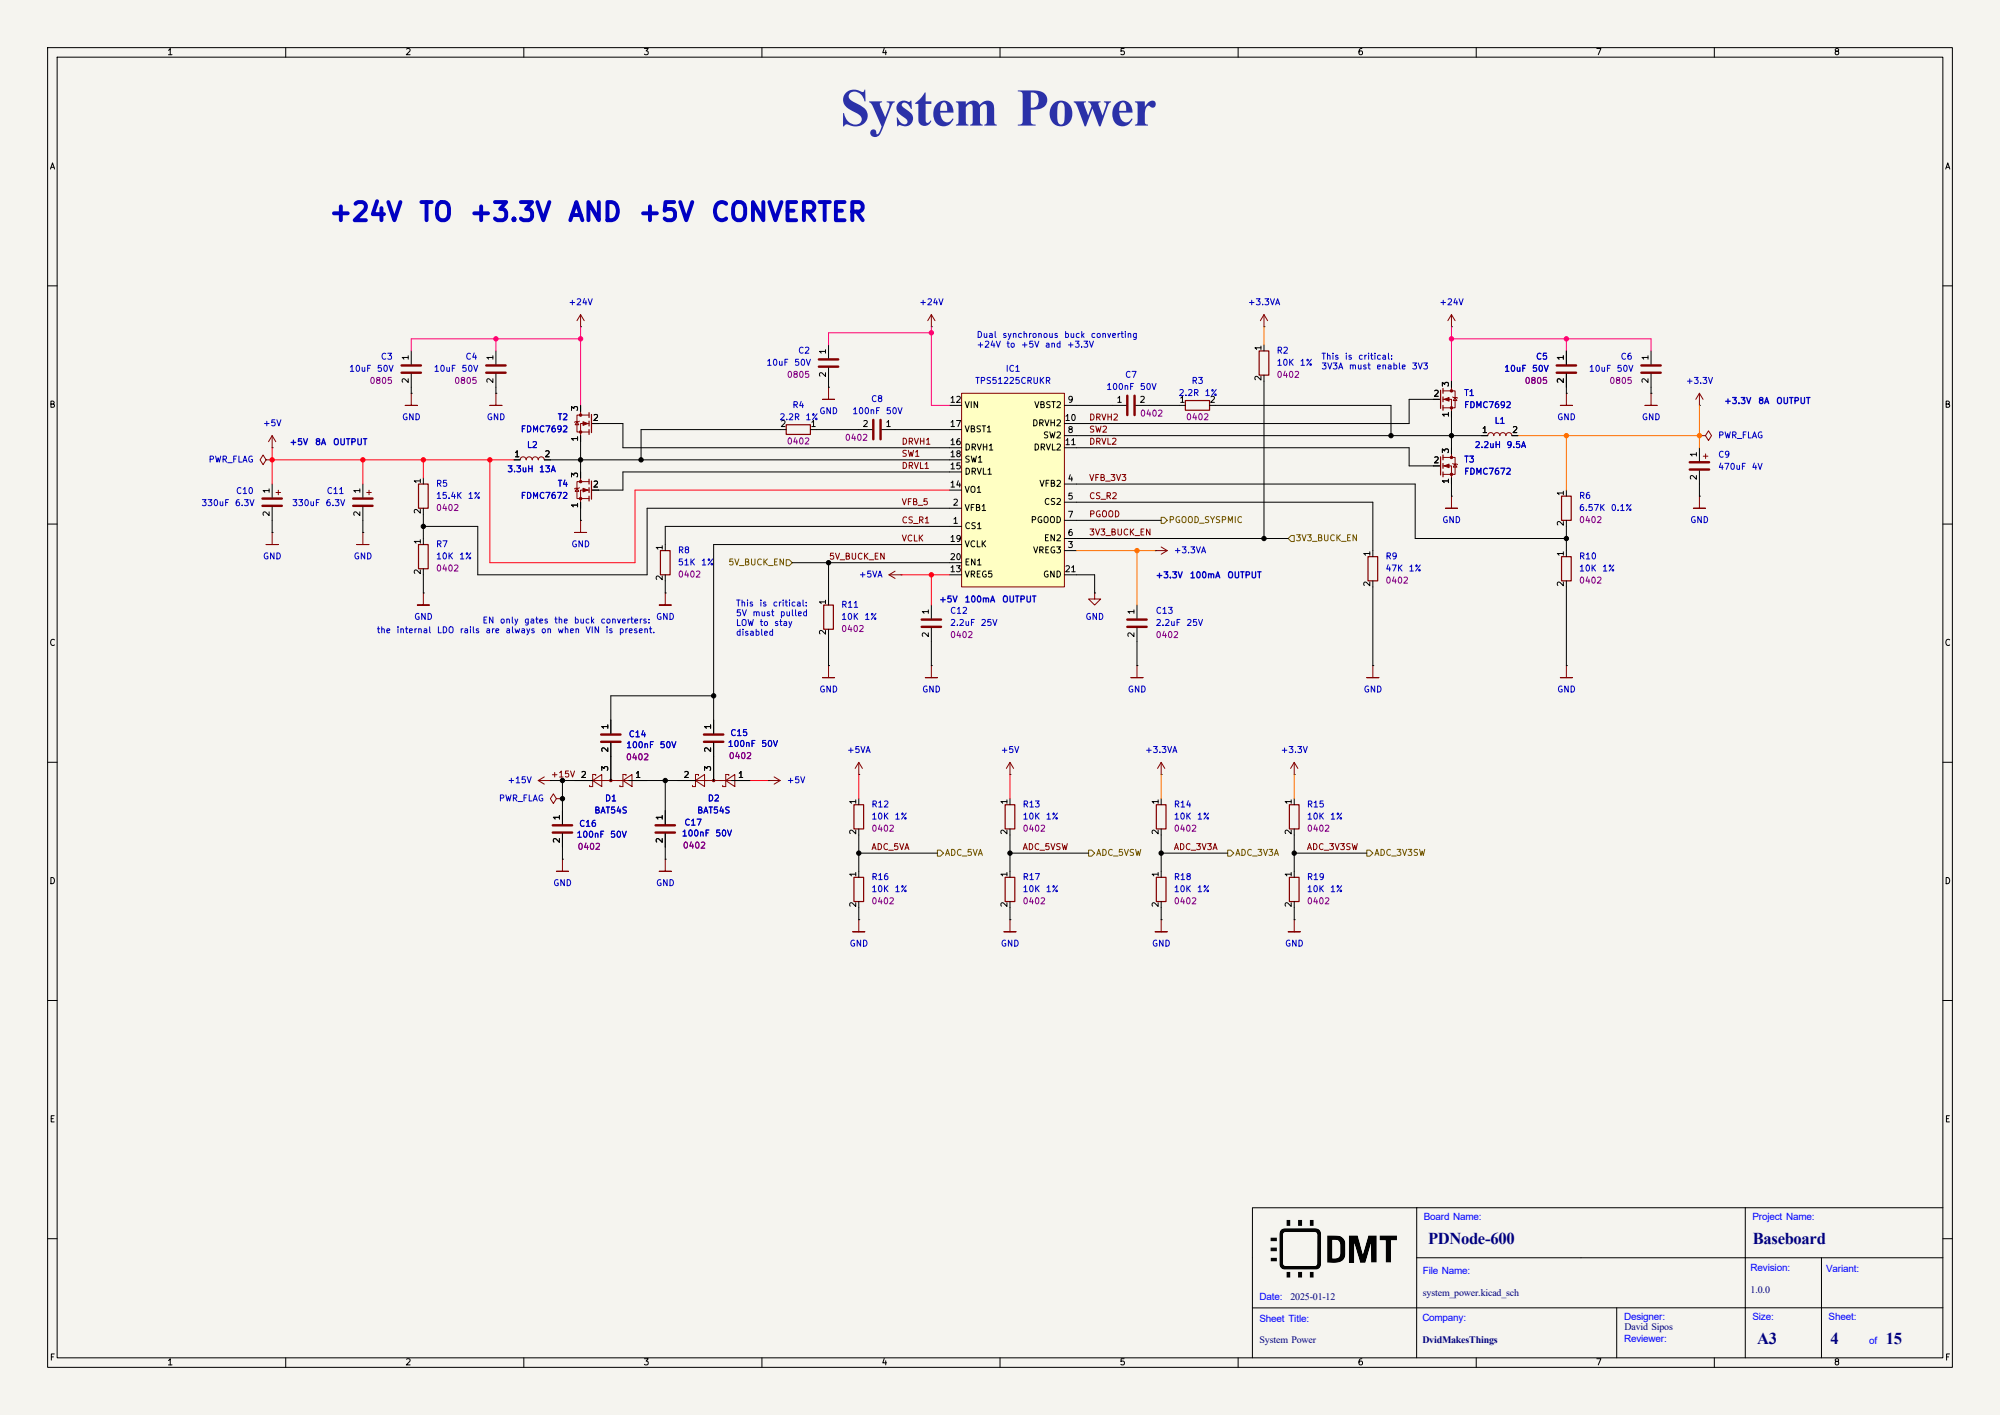
[picture p49: page 4]

3V3A must enable 3V3 +24V TO +3.3V AND +5V CONVERTER

Dual synchronous buck converting
+24V to +5V and +3.3V

VFB1 2

PGOOD PGOOD_SYSPMIC

EN only gates the buck converters: the internal LDO rails are always on when VIN is present.

File Name: Sheet Title: System Power GND

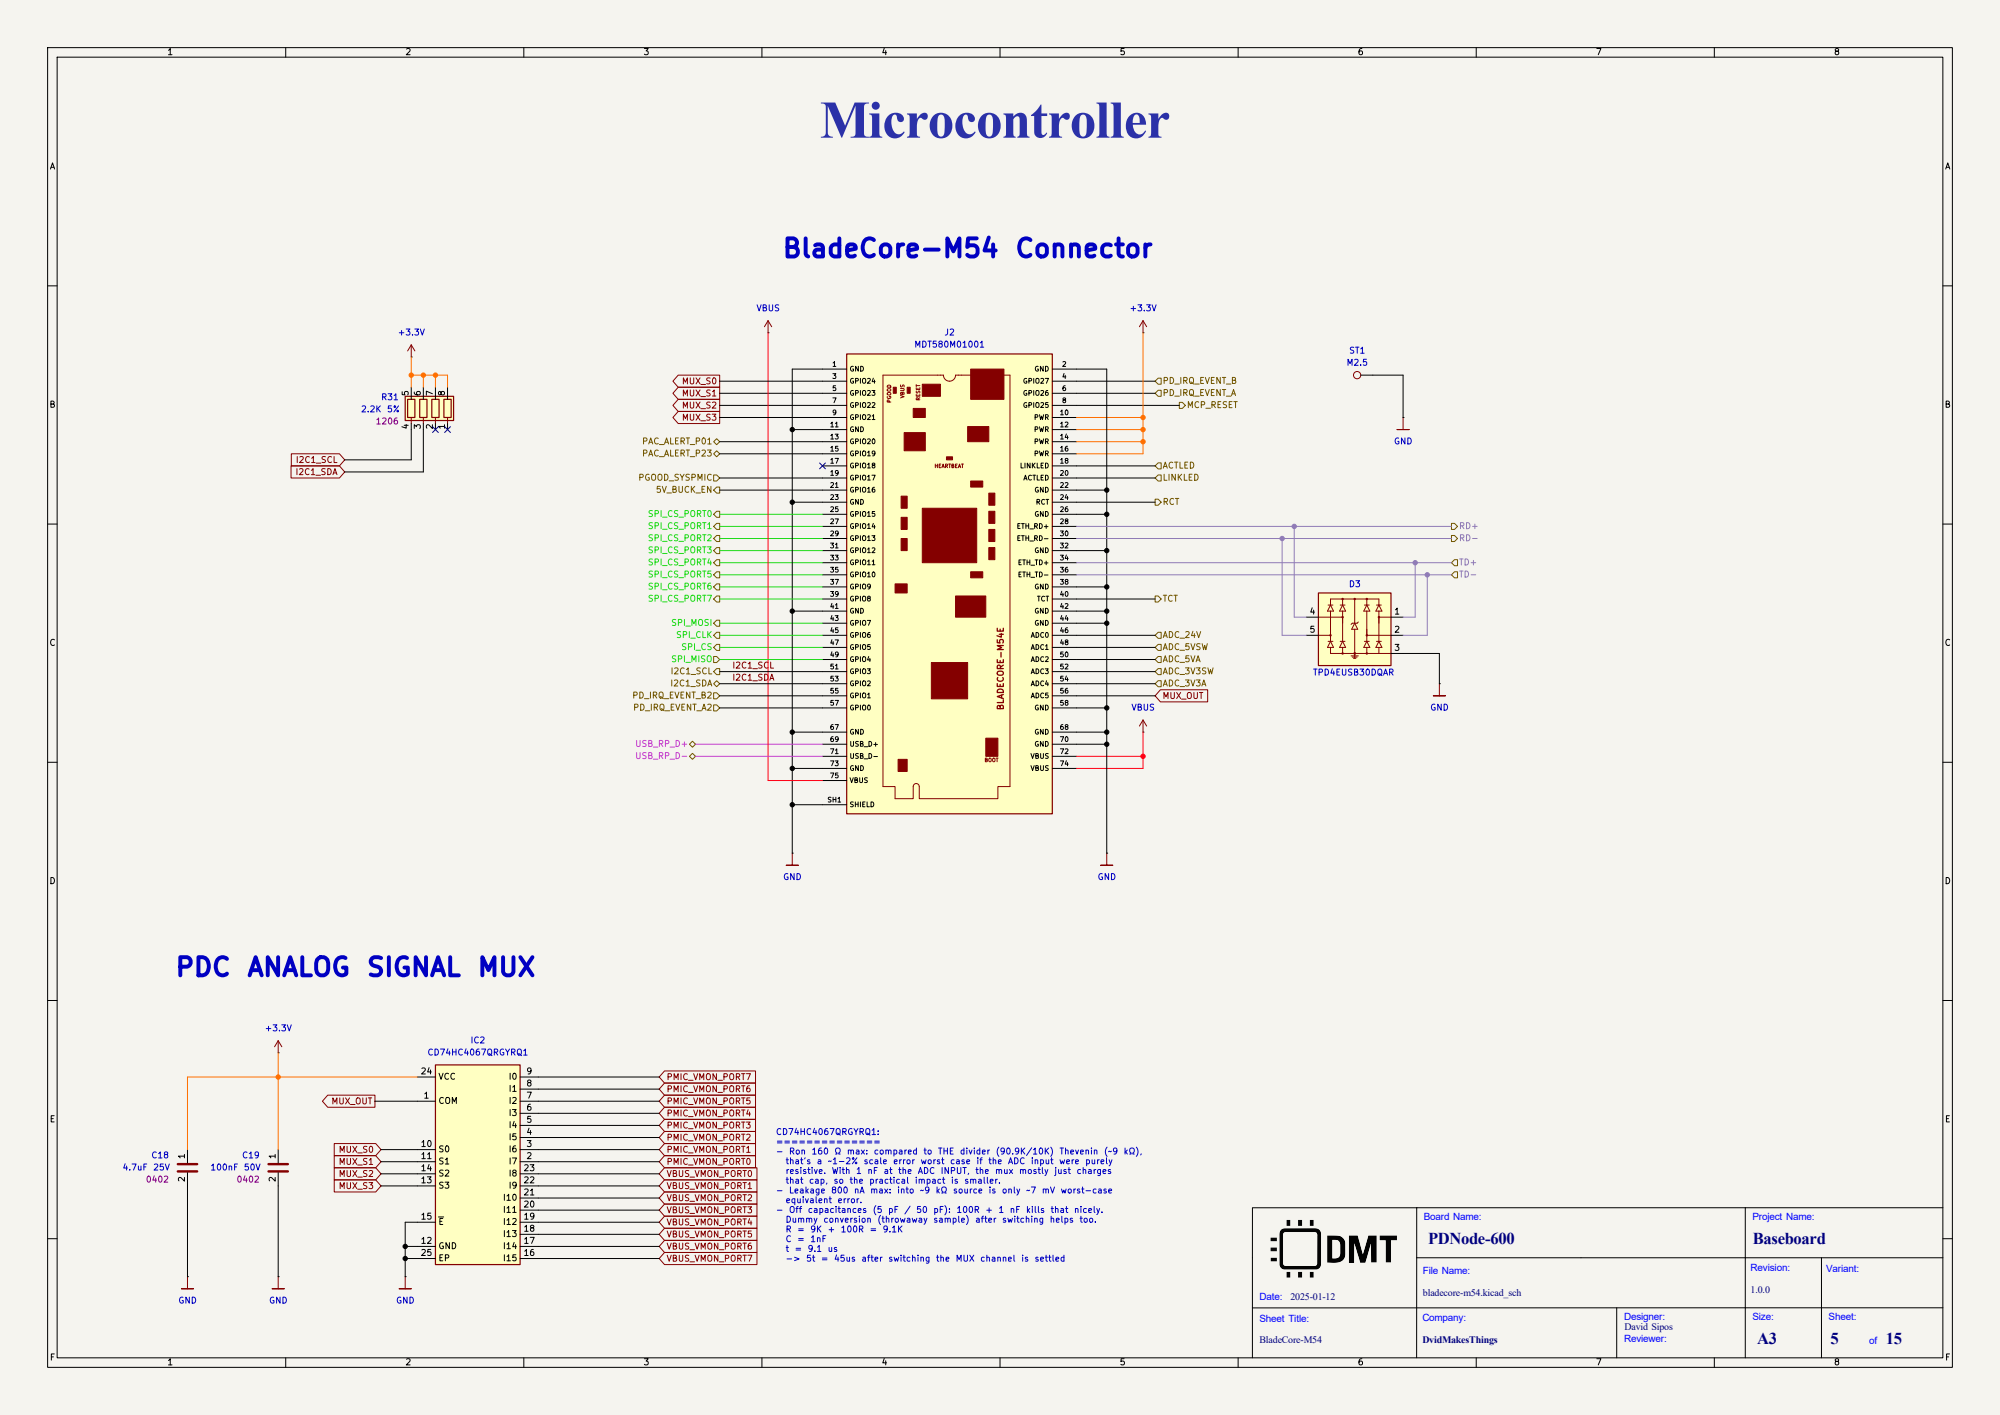
[picture p50: page 5]

t = 9.1 us -> 5t = 45us after switching the MUX channel is settled PDC ANALOG SIGNAL MUX

- Ron 160 Ω max: compared to THE divider (90.9K/10K) Thevenin (~9 kΩ),
that's a ~1-2% scale error worst case if the ADC input were purely
resistive. With 1 nF at the ADC INPUT, the mux mostly just charges
that cap, so the practical impact is smaller. - Leakage 800 nA max: into ~9 kΩ source is only ~7 mV worst-case

File Name: Sheet Title: BladeCore-M54 1 2 C18

equivalent error. - Off capacitances (5 pF / 50 pF): 100R + 1 nF kills that nicely.

Dummy conversion (throwaway sample) after switching helps too. R = 9K + 100R = 9.1K

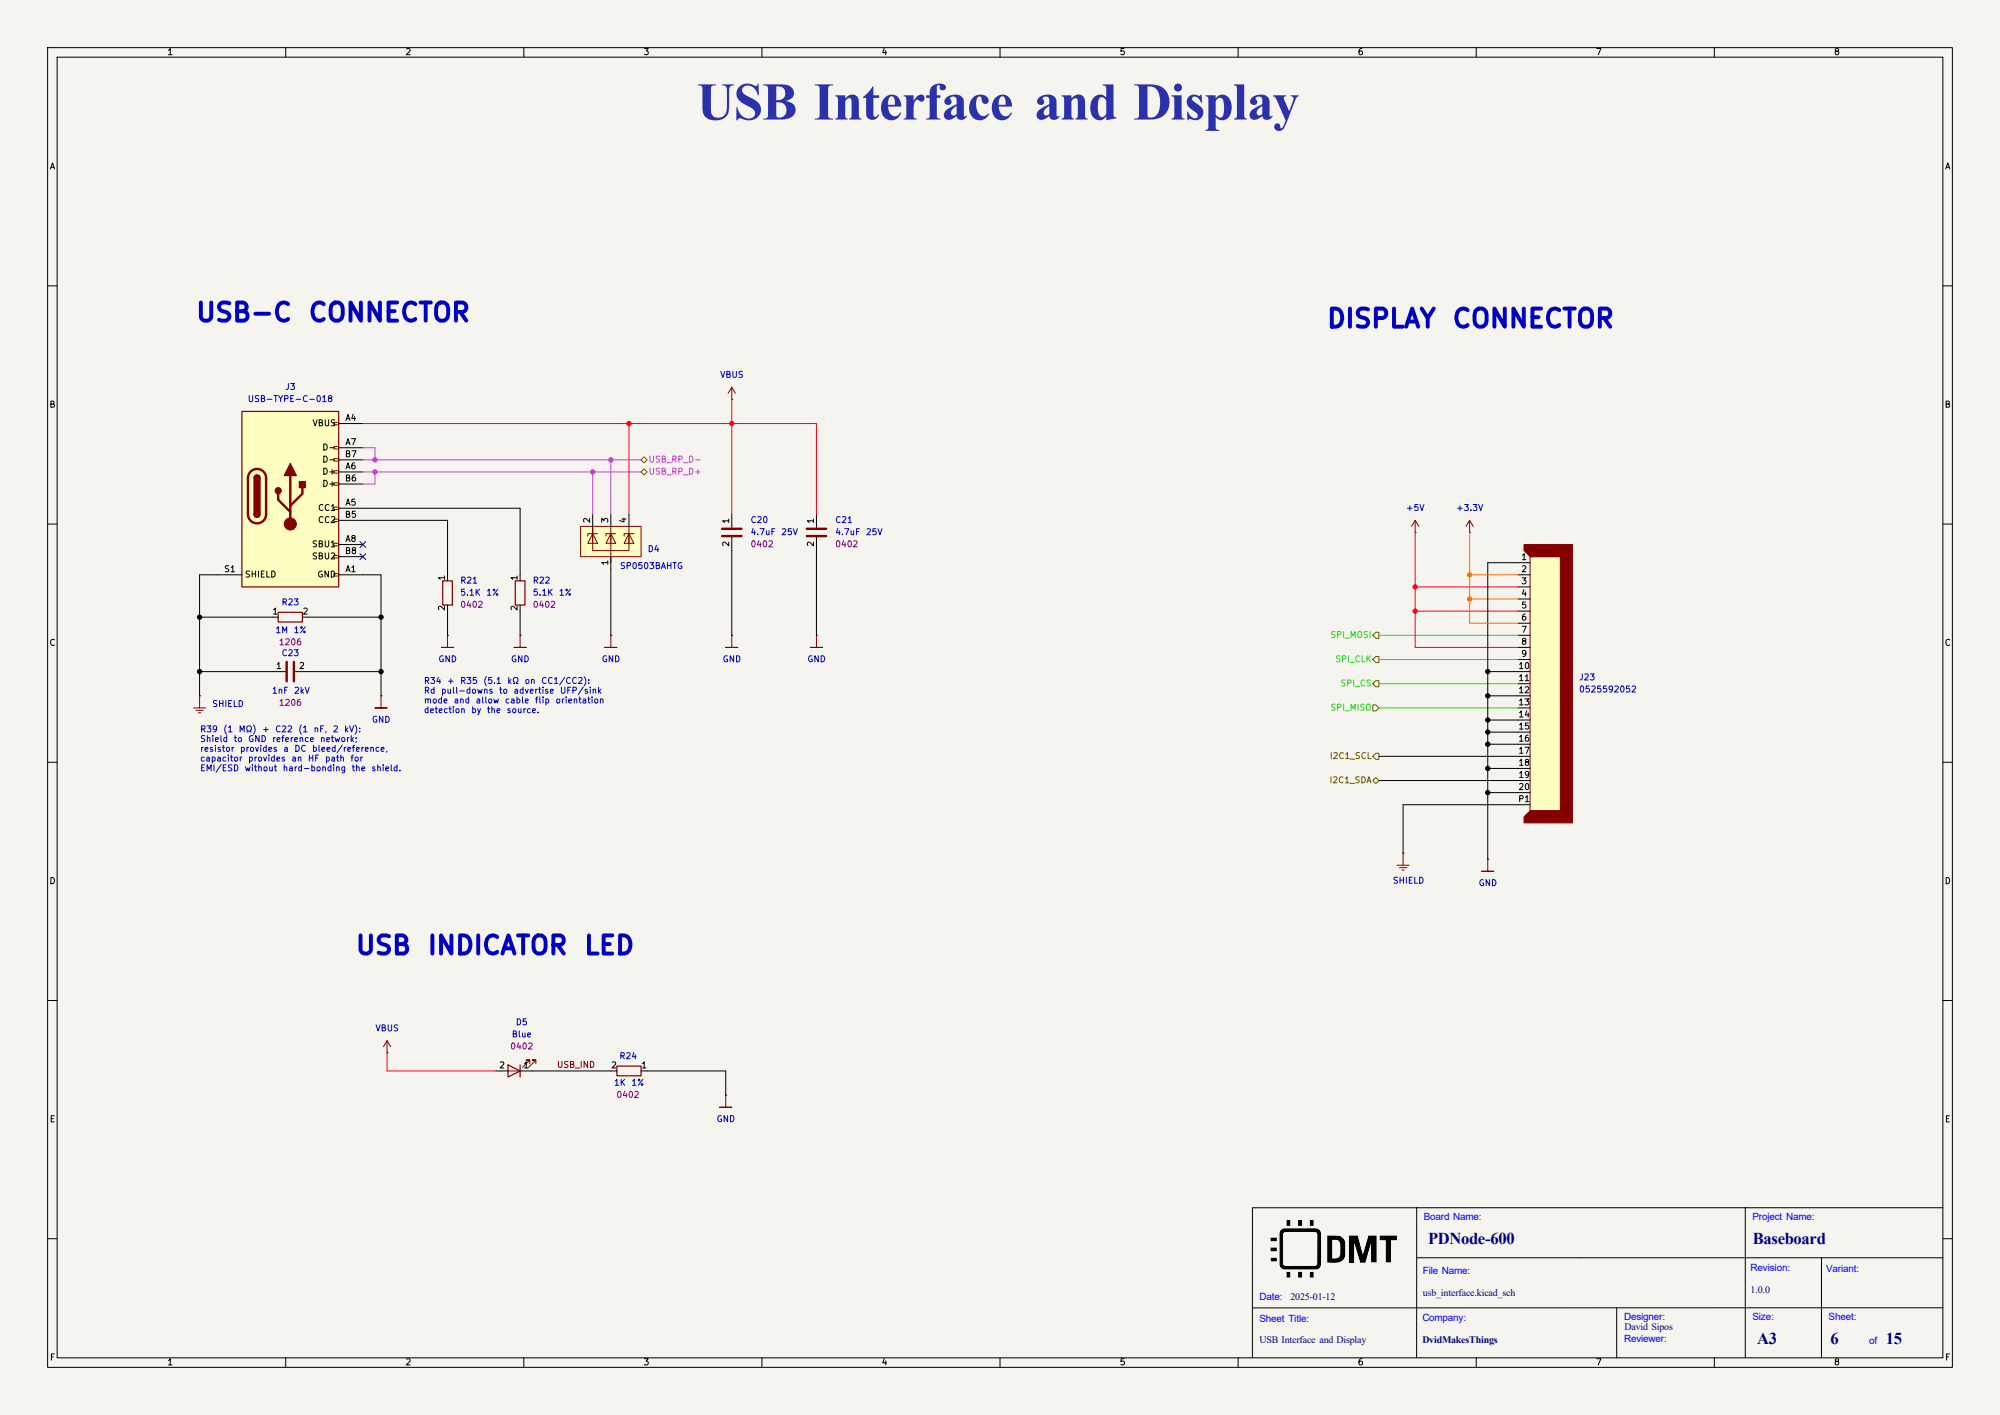
[picture p51: page 6]

Rd pull-downs to advertise UFP/sink
mode and allow cable flip orientation

detection by the source. USB INDICATOR LED

Shield to GND reference network;
resistor provides a DC bleed/reference,
capacitor provides an HF path for
EMI/ESD without hard-bonding the shield.

File Name: Sheet Title: USB Interface and Display

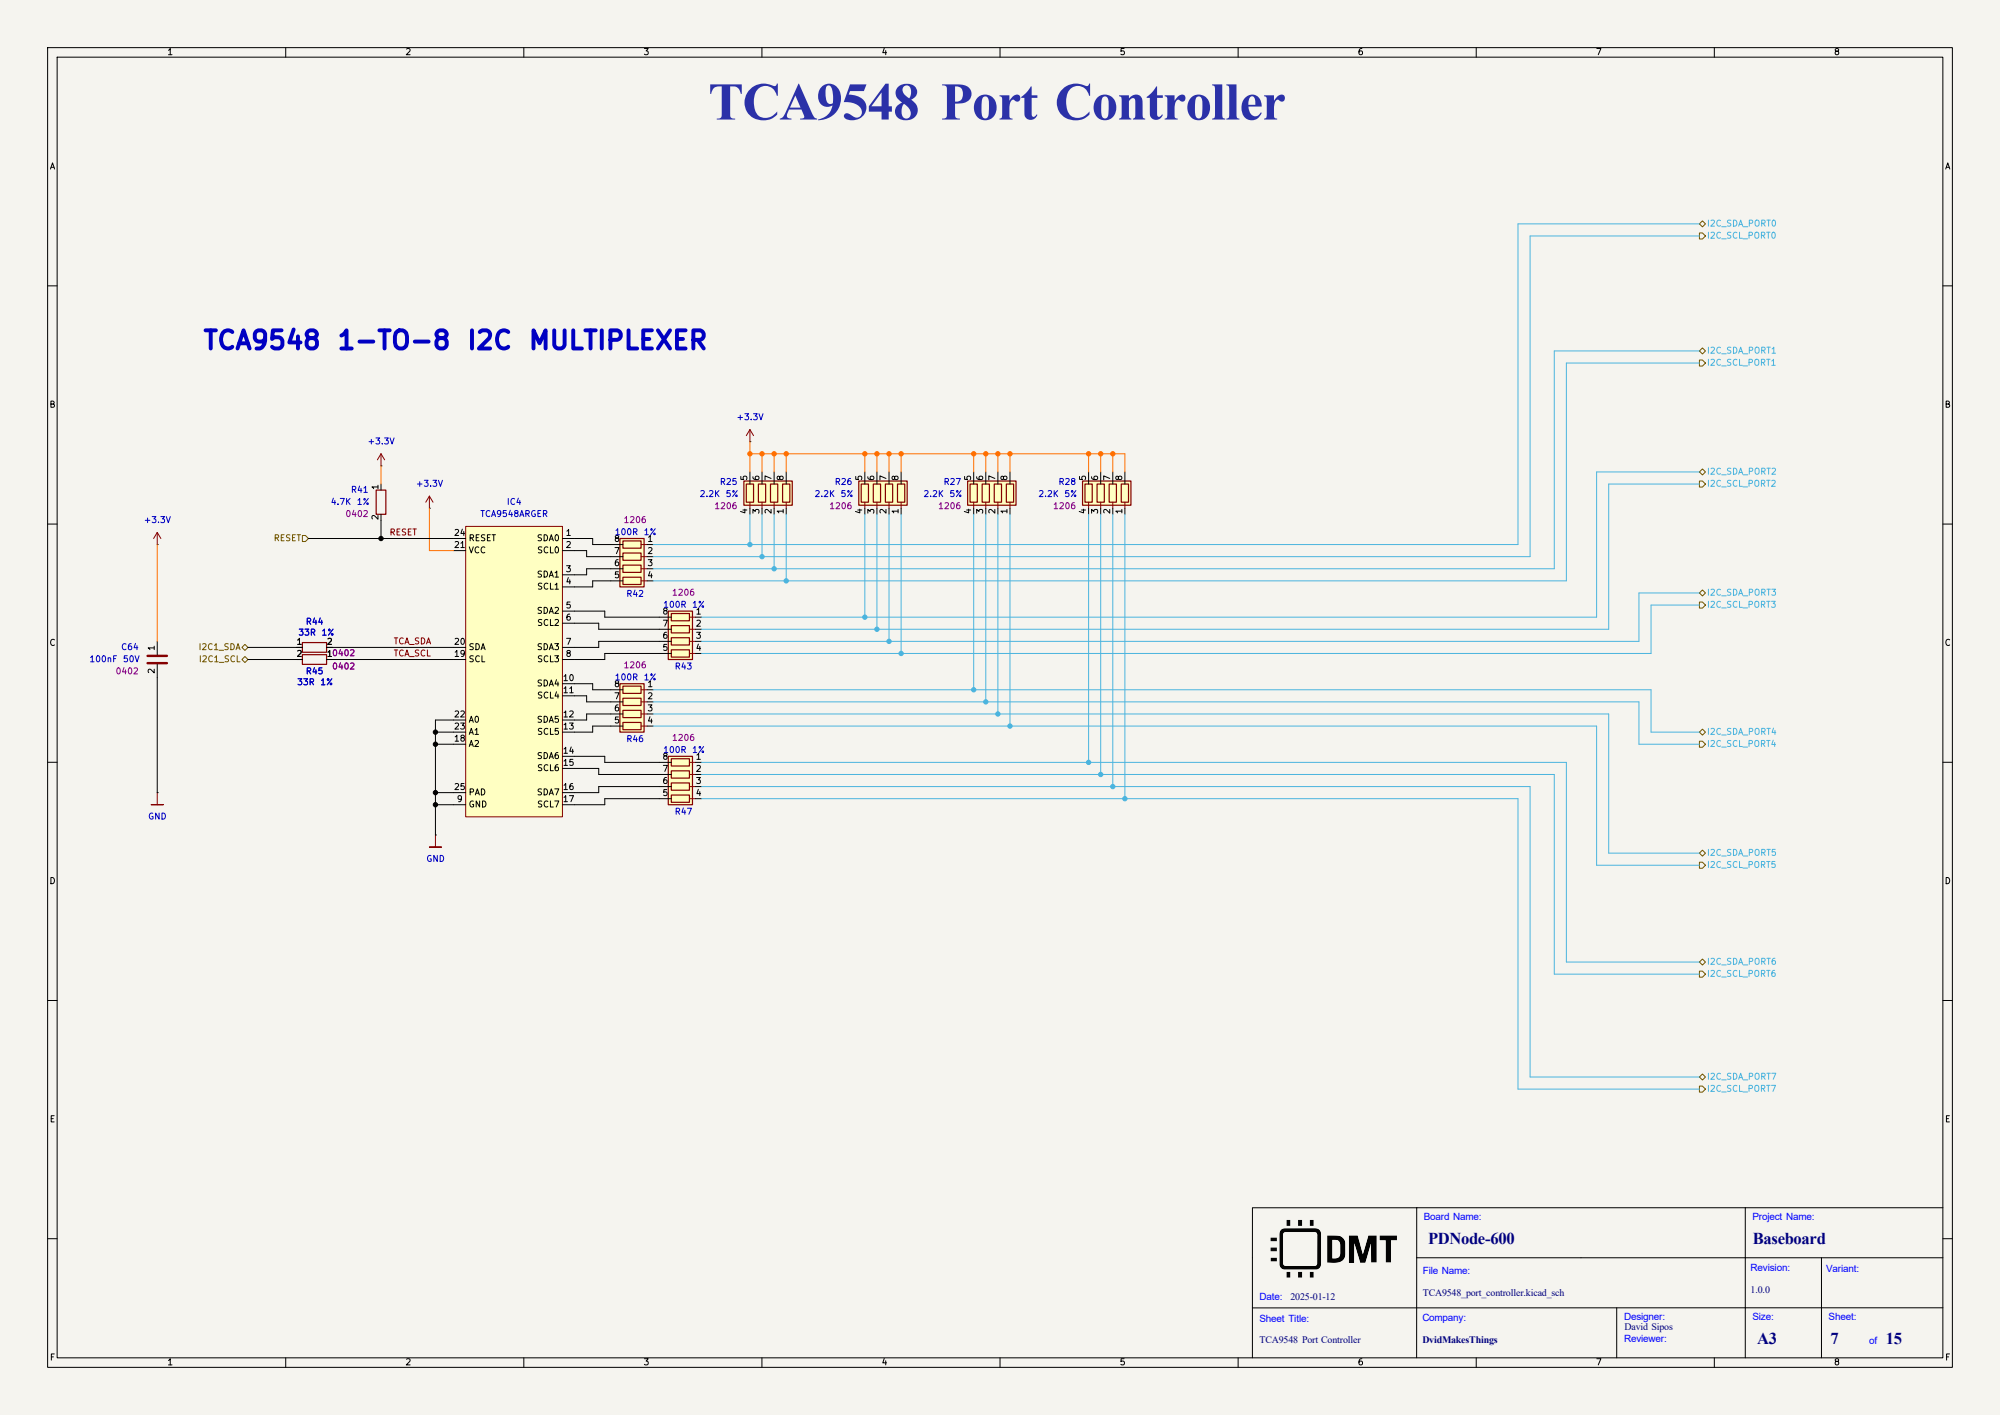
[picture p52: page 7]

File Name: Sheet Title: TCA9548 Port Controller

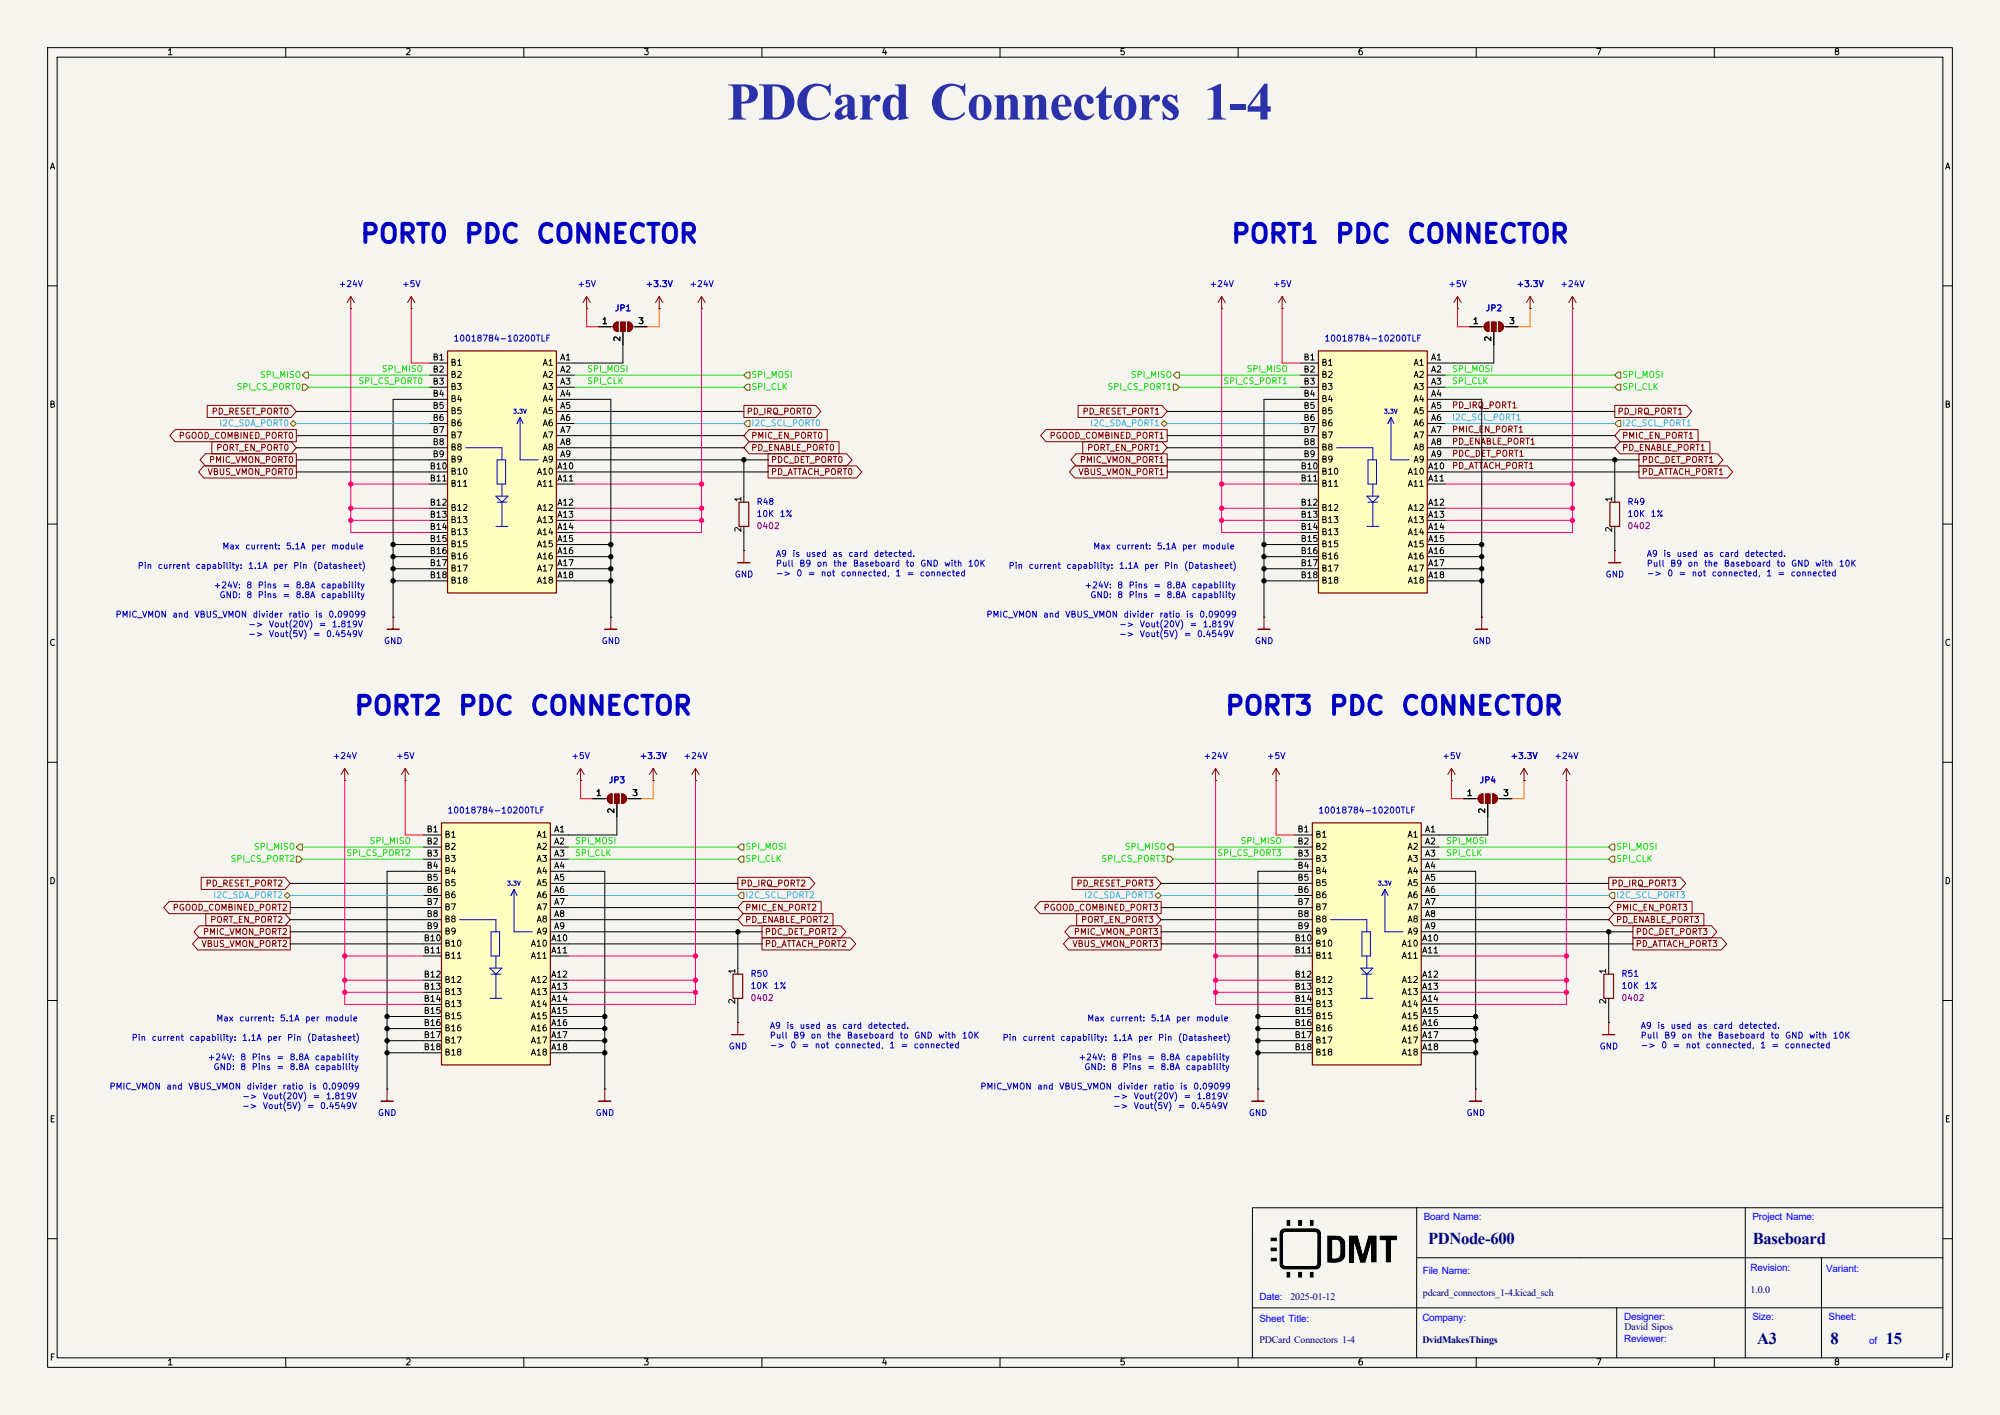
[picture p53: page 8]

PMIC_VMON and VBUS_VMON divider ratio is 0.09099 -> Vout(20V) = 1.819V -> Vout(5V) = 0.4549V Max current: 5.1A per module Pin current capability: 1.1A per Pin (Datasheet)

A9 is used as card detected. Pull B9 on the Baseboard to GND with 10K -> 0 = not connected, 1 = connected

PMIC_VMON and VBUS_VMON divider ratio is 0.09099 -> Vout(20V) = 1.819V -> Vout(5V) = 0.4549V

A9 is used as card detected. Pull B9 on the Baseboard to GND with 10K -> 0 = not connected, 1 = connected PORT2 PDC CONNECTOR

A9 is used as card detected. Pull B9 on the Baseboard to GND with 10K -> 0 = not connected, 1 = connected Max current: 5.1A per module Pin current capability: 1.1A per Pin (Datasheet)

File Name: Sheet Title: PDCard Connectors 1-4

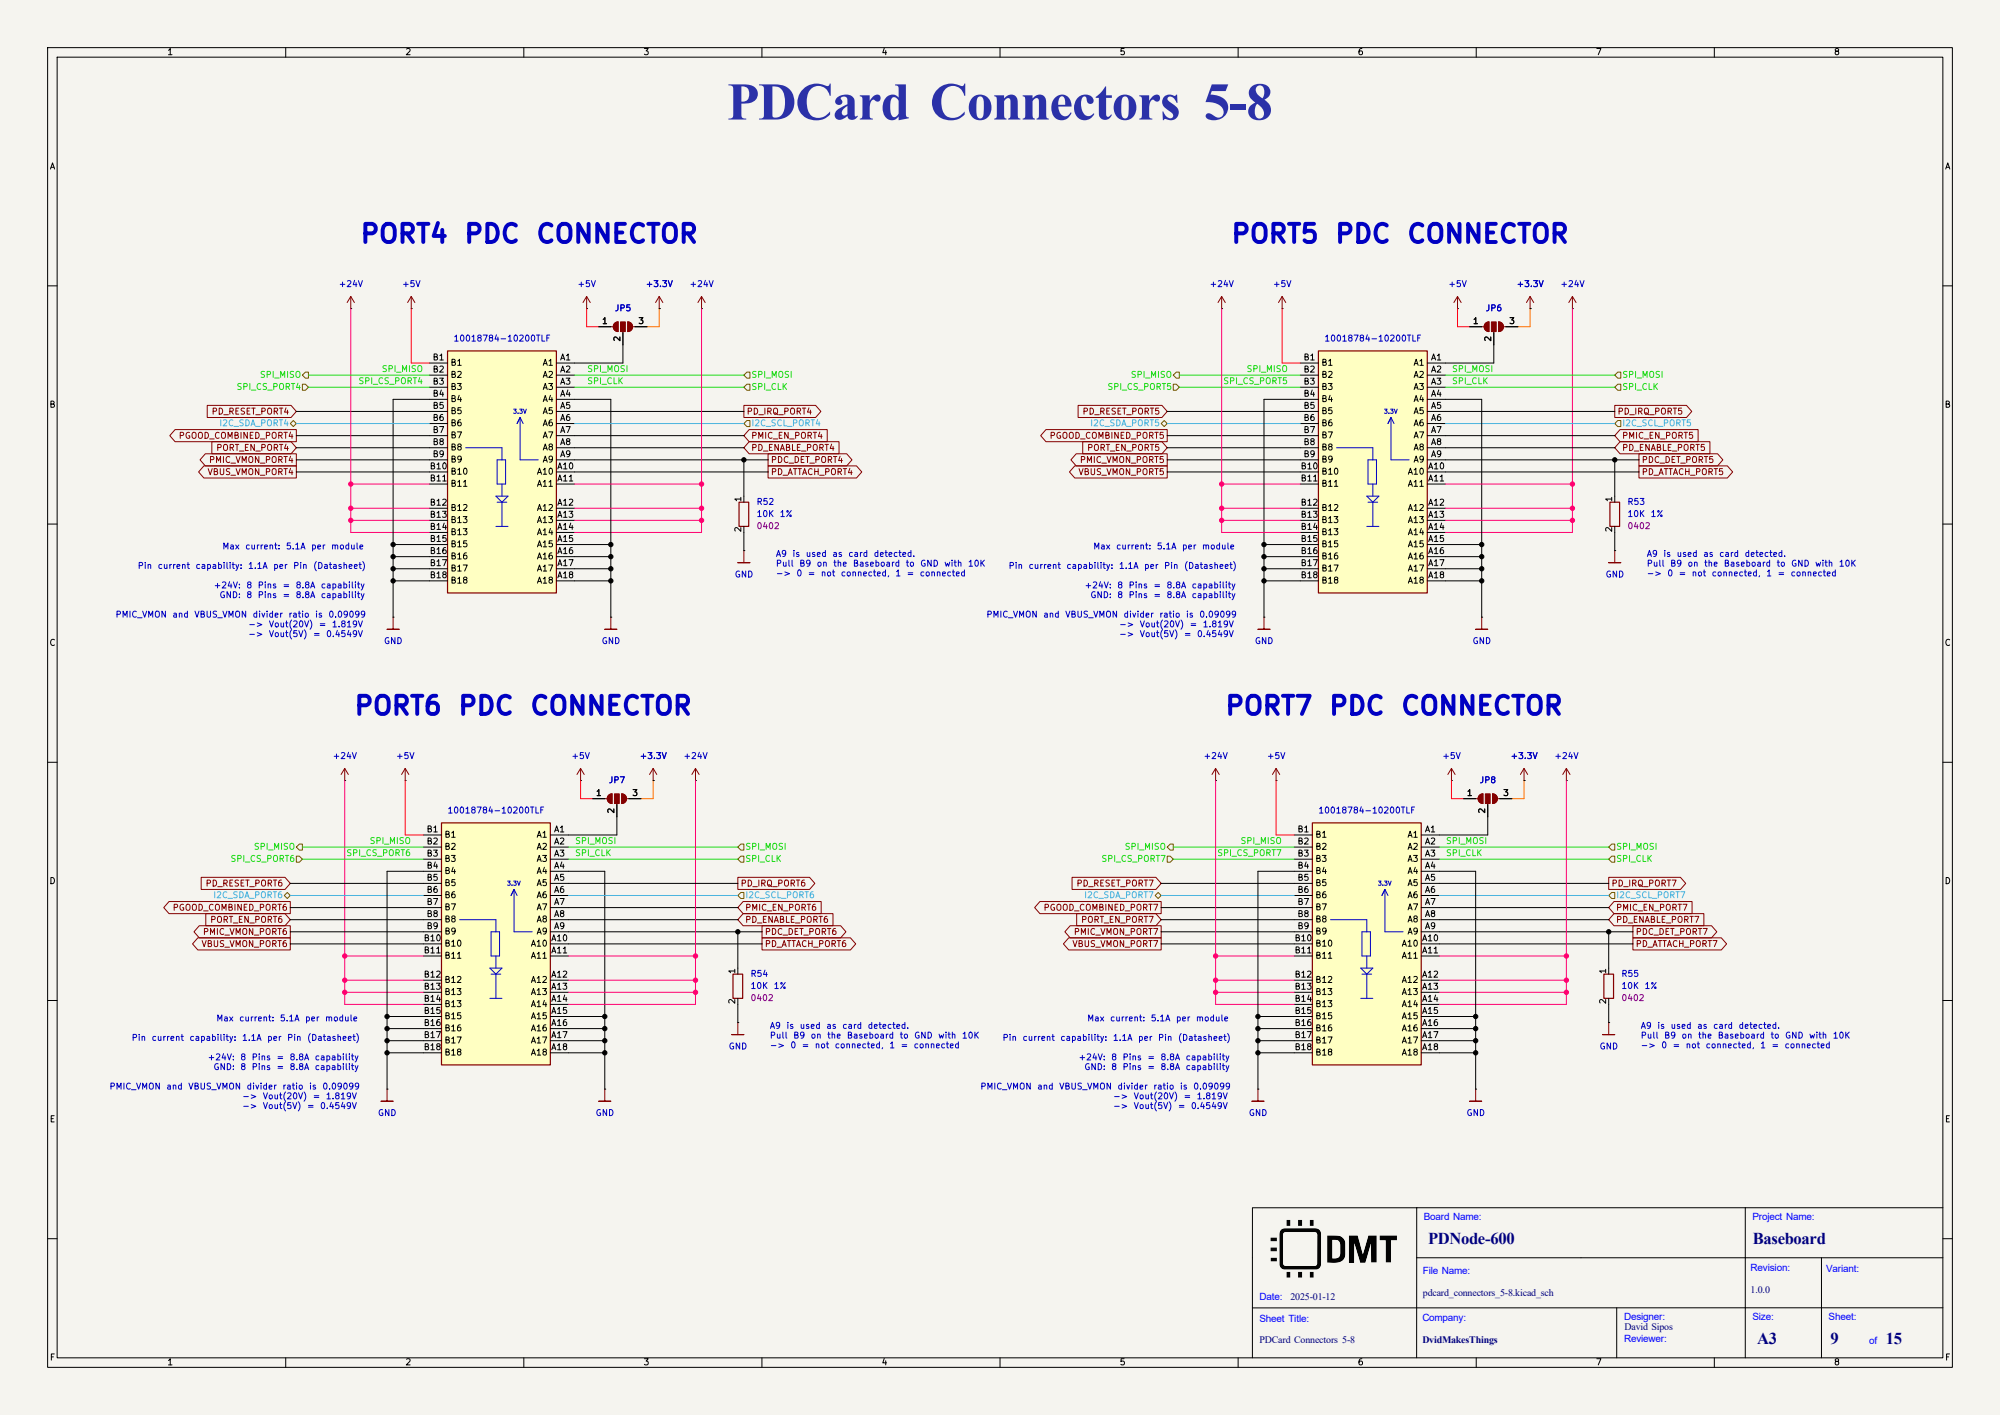
[picture p54: page 9]

PMIC_VMON and VBUS_VMON divider ratio is 0.09099 -> Vout(20V) = 1.819V -> Vout(5V) = 0.4549VPORT5 PDC CONNECTOR

3.3V Max current: 5.1A per module Pin current capability: 1.1A per Pin (Datasheet)

Max current: 5.1A per module Pin current capability: 1.1A per Pin (Datasheet)

A9 is used as card detected. Pull B9 on the Baseboard to GND with 10K -> 0 = not connected, 1 = connected PORT6 PDC CONNECTOR

PMIC_VMON and VBUS_VMON divider ratio is 0.09099 -> Vout(20V) = 1.819V -> Vout(5V) = 0.4549V

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

File Name: Sheet Title: PDCard Connectors 5-8

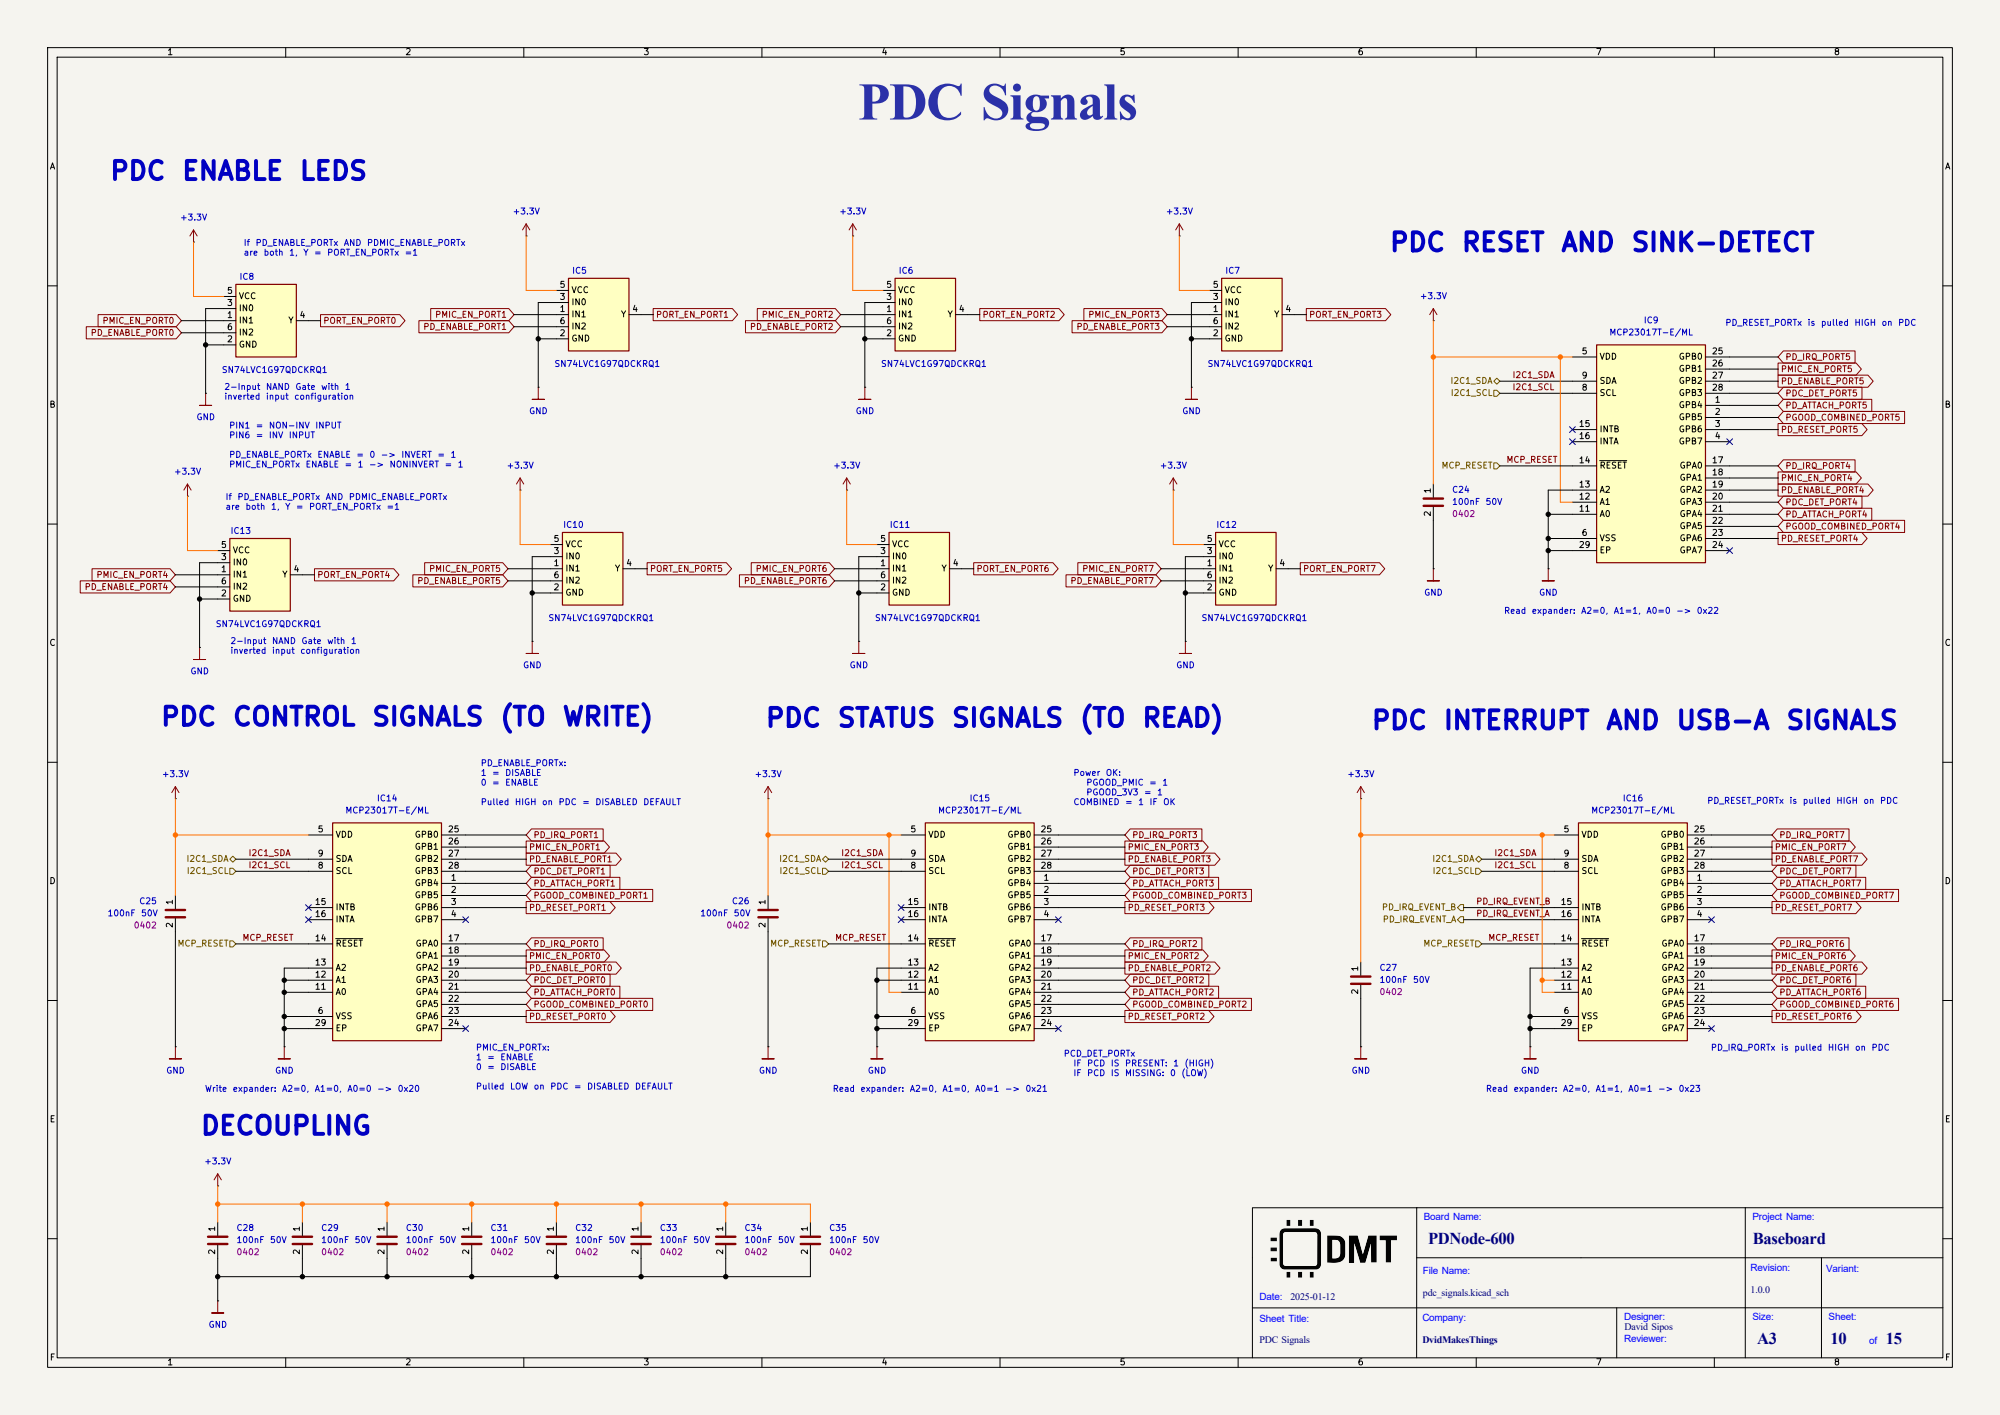
[picture p55: page 10]

Read expander: A2=0, A1=1, A0=0 -> 0x22 PDC RESET AND SINK-DETECT

If PD_ENABLE_PORTx AND PDMIC_ENABLE_PORTx are both 1, Y = PORT_EN_PORTx =1

2-Input NAND Gate with 1
inverted input configuration
SN74LVC1G97QDCKRQ1 GND

PIN1 = NON-INV INPUT PIN6 = INV INPUT PD_ENABLE_PORTx ENABLE = 0 -> INVERT = 1 PMIC_EN_PORTx ENABLE = 1 -> NONINVERT = 1

1 = DISABLE 0 = ENABLE Pulled HIGH on PDC = DISABLED DEFAULT PDC CONTROL SIGNALS (TO WRITE)

PDC STATUS SIGNALS (TO READ)

PDC INTERRUPT AND USB-A SIGNALS

Read expander: A2=0, A1=1, A0=1 -> 0x23 PCD_DET_PORTx
IF PCD IS PRESENT: 1 (HIGH)
IF PCD IS MISSING: 0 (LOW)

PD_IRQ_PORTx is pulled HIGH on PDC

File Name: Sheet Title: PDC Signals

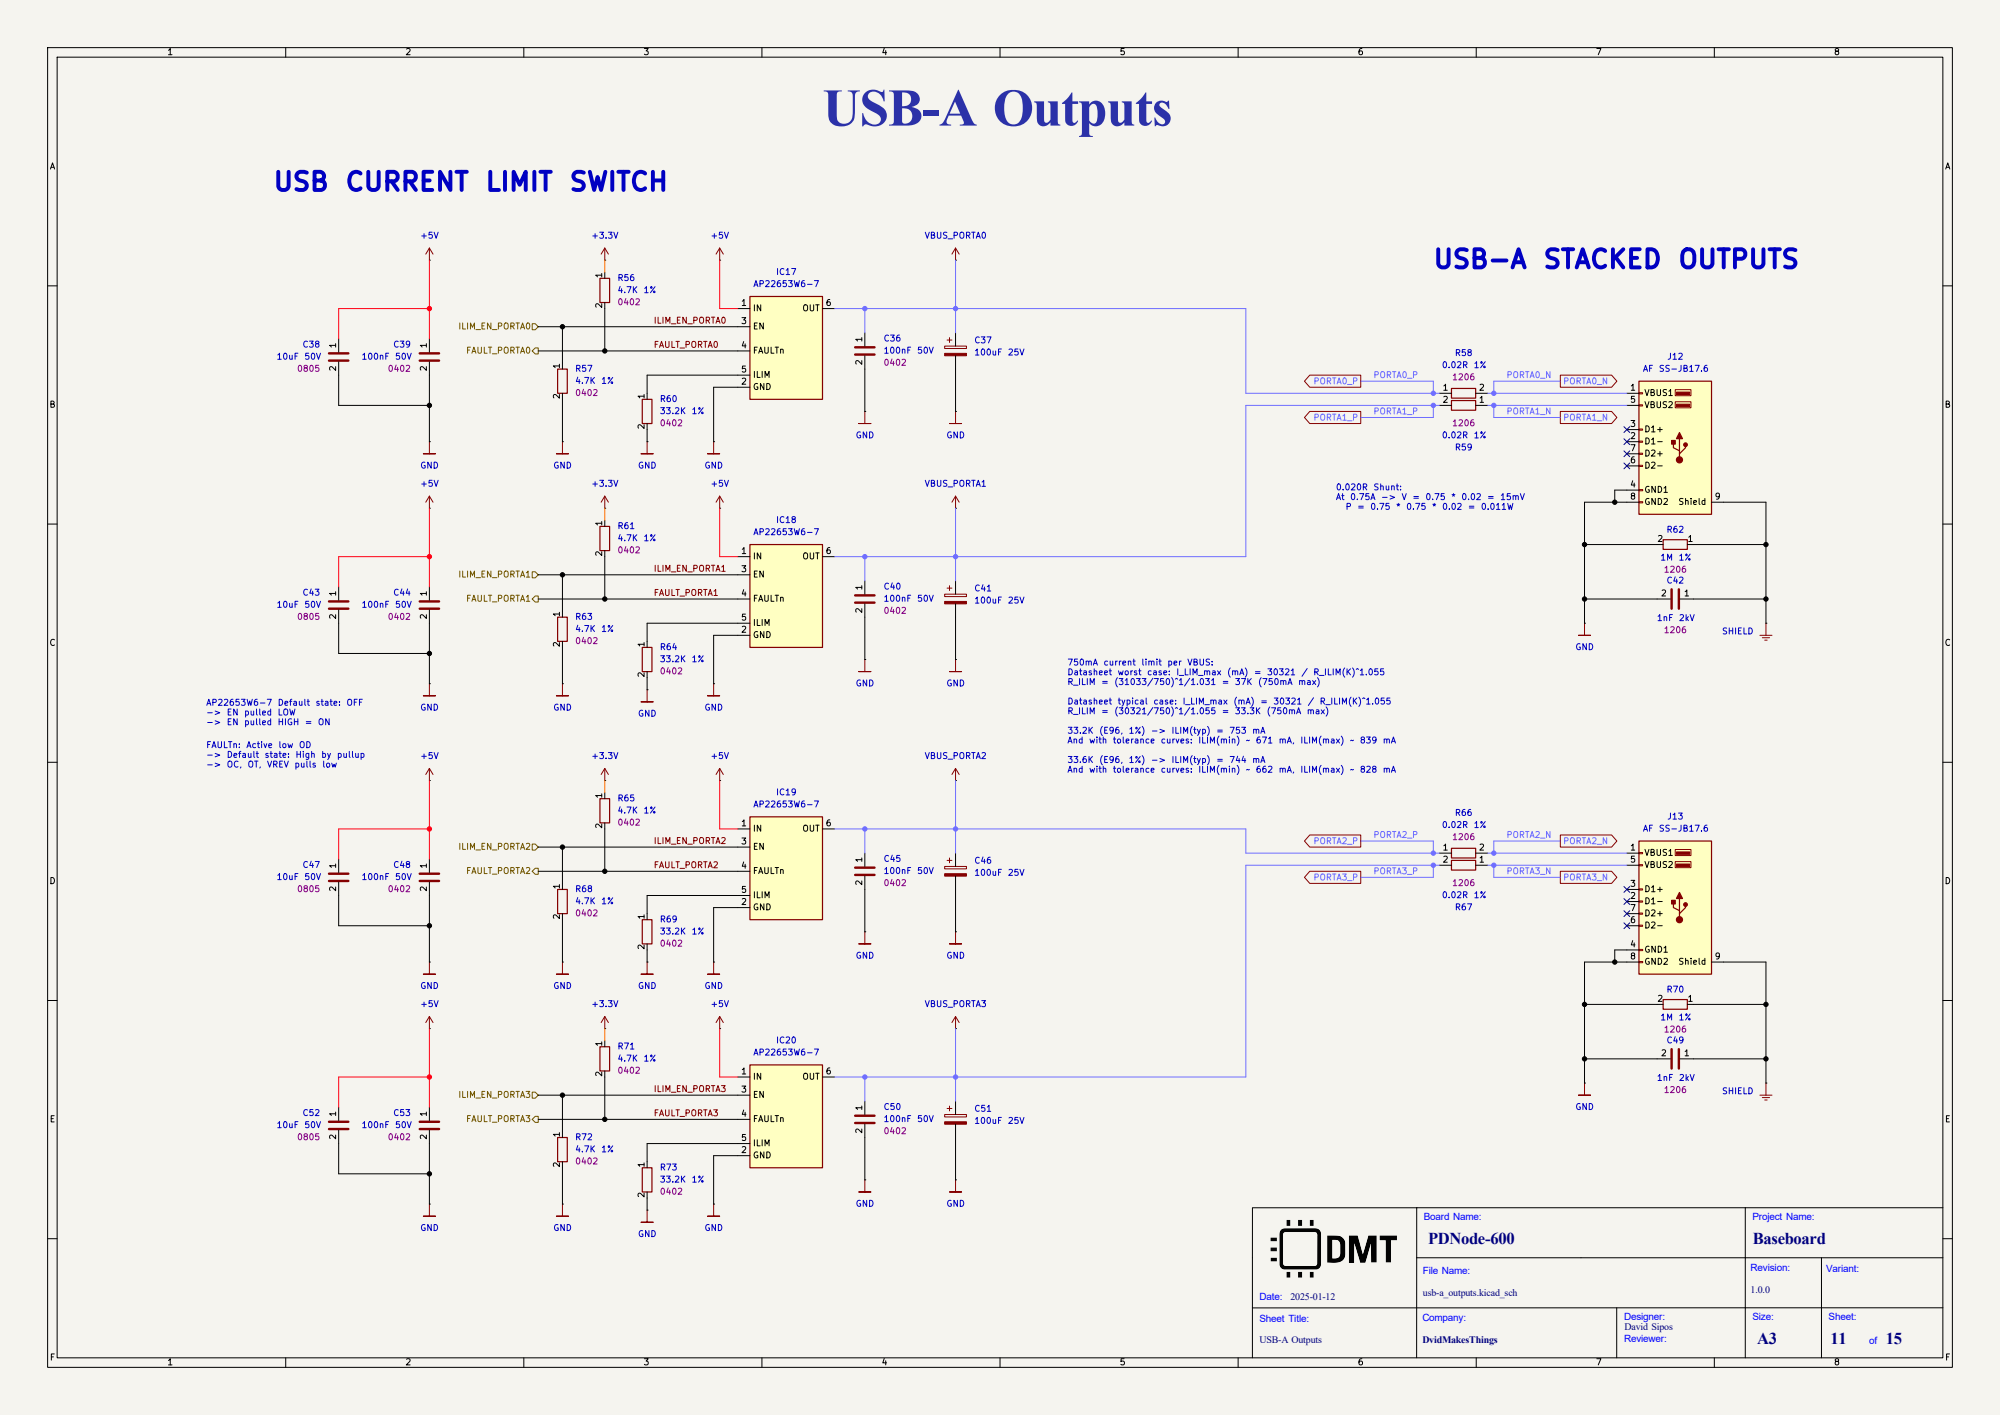
[picture p56: page 11]

FAULTn: Active low OD -> Default state: High by pullup -> OC, OT, VREV pulls low USB CURRENT LIMIT SWITCH

750mA current limit per VBUS: Datasheet worst case: I_LIM_max (mA) = 30321 / R_ILIM(K)^1.055

AP22653W6-7 Default state: OFF -> EN pulled LOW -> EN pulled HIGH = ON

Datasheet typical case: I_LIM_max (mA) = 30321 / R_ILIM(K)^1.055
R_ILIM = (30321/750)^1/1.055 = 33.3K (750mA max)

33.2K (E96, 1%) -> ILIM(typ) = 753 mA
And with tolerance curves: ILIM(min) ~ 671 mA, ILIM(max) ~ 839 mA 33.6K (E96, 1%) -> ILIM(typ) = 744 mA

And with tolerance curves: ILIM(min) ~ 662 mA, ILIM(max) ~ 828 mA

File Name: Sheet Title: USB-A Outputs

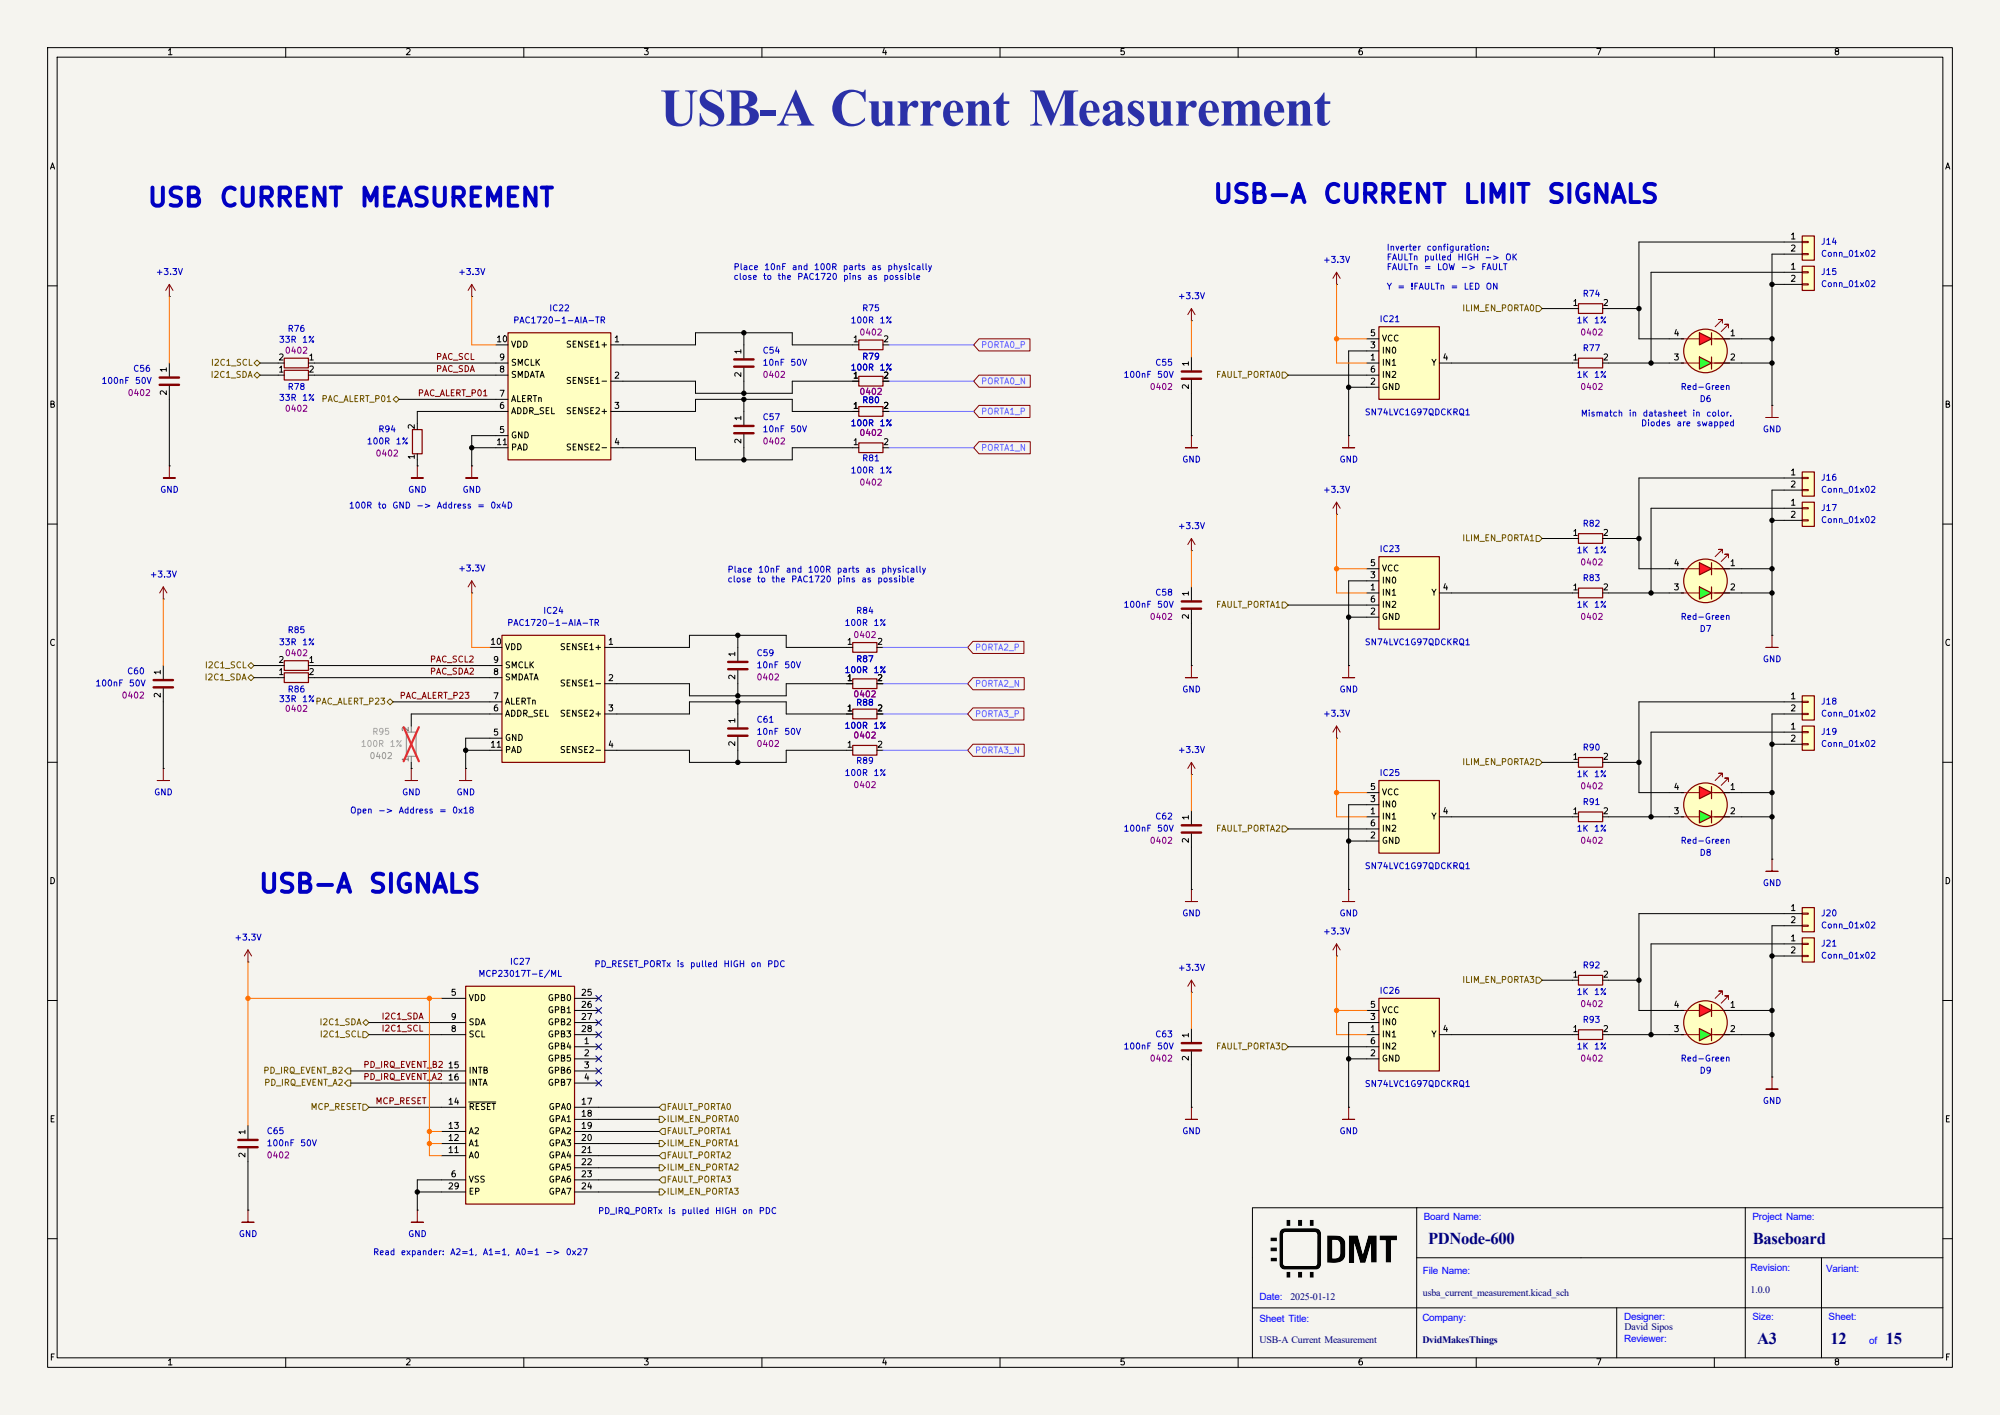
[picture p57: page 12]

USB-A CURRENT LIMIT SIGNALS

Inverter configuration:
FAULTn pulled HIGH -> OK

FAULTn = LOW -> FAULT Y = !FAULTn = LED ON USB-A SIGNALS

Place 10nF and 100R parts as physically
close to the PAC1720 pins as possible

Mismatch in datasheet in color.

PD_RESET_PORTx is pulled HIGH on PDC

PD_IRQ_PORTx is pulled HIGH on PDC

File Name: Sheet Title: USB-A Current Measurement

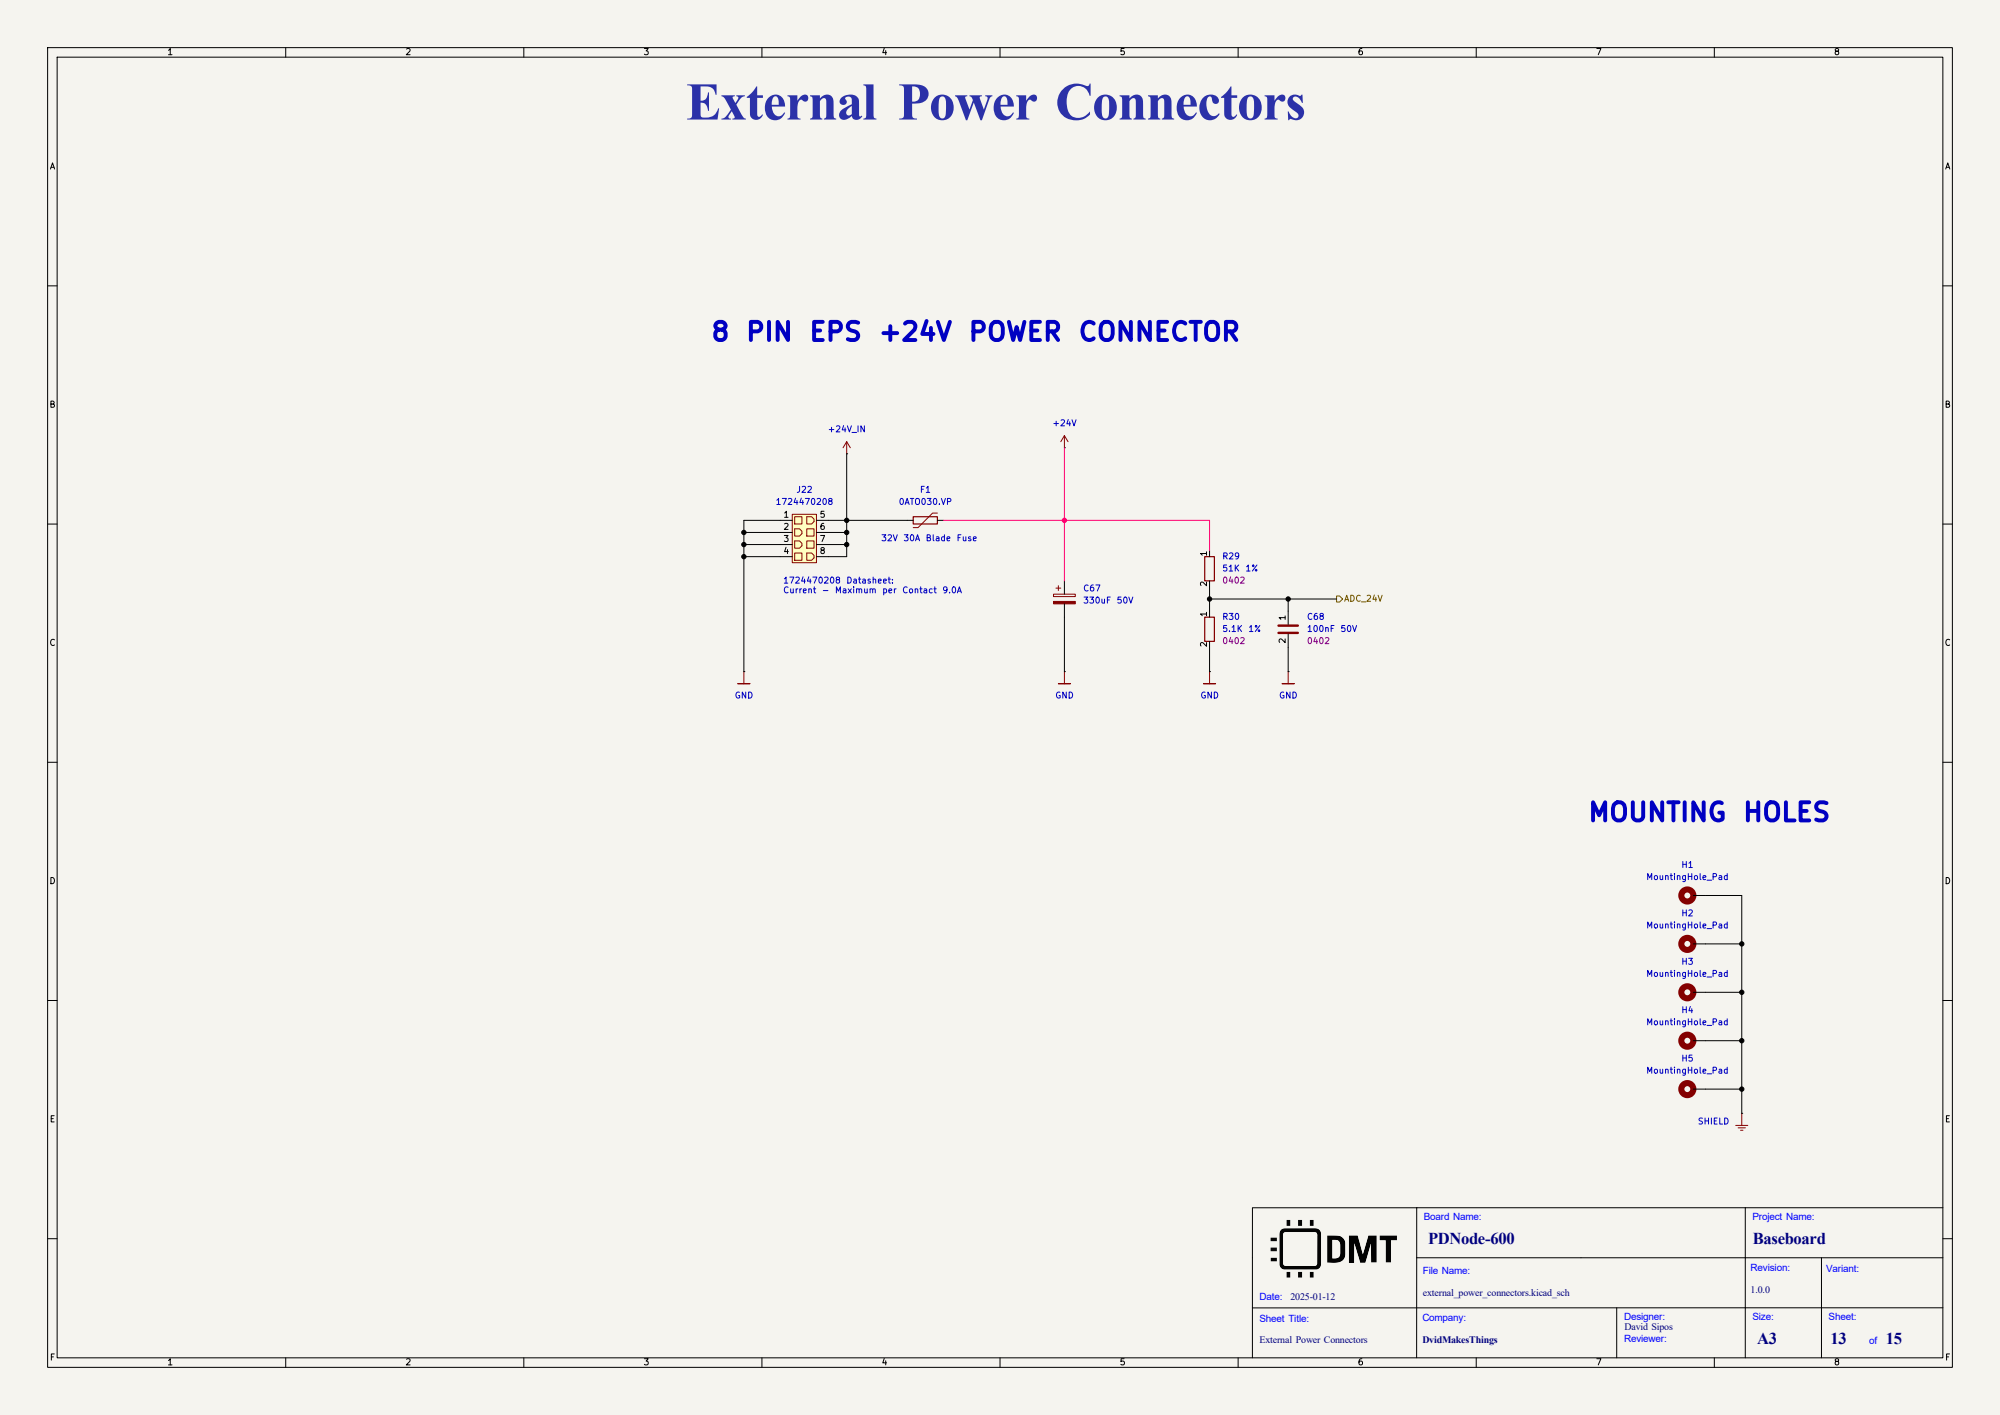
[picture p58: page 13]

8 PIN EPS +24V POWER CONNECTOR

File Name: Sheet Title: External Power Connectors

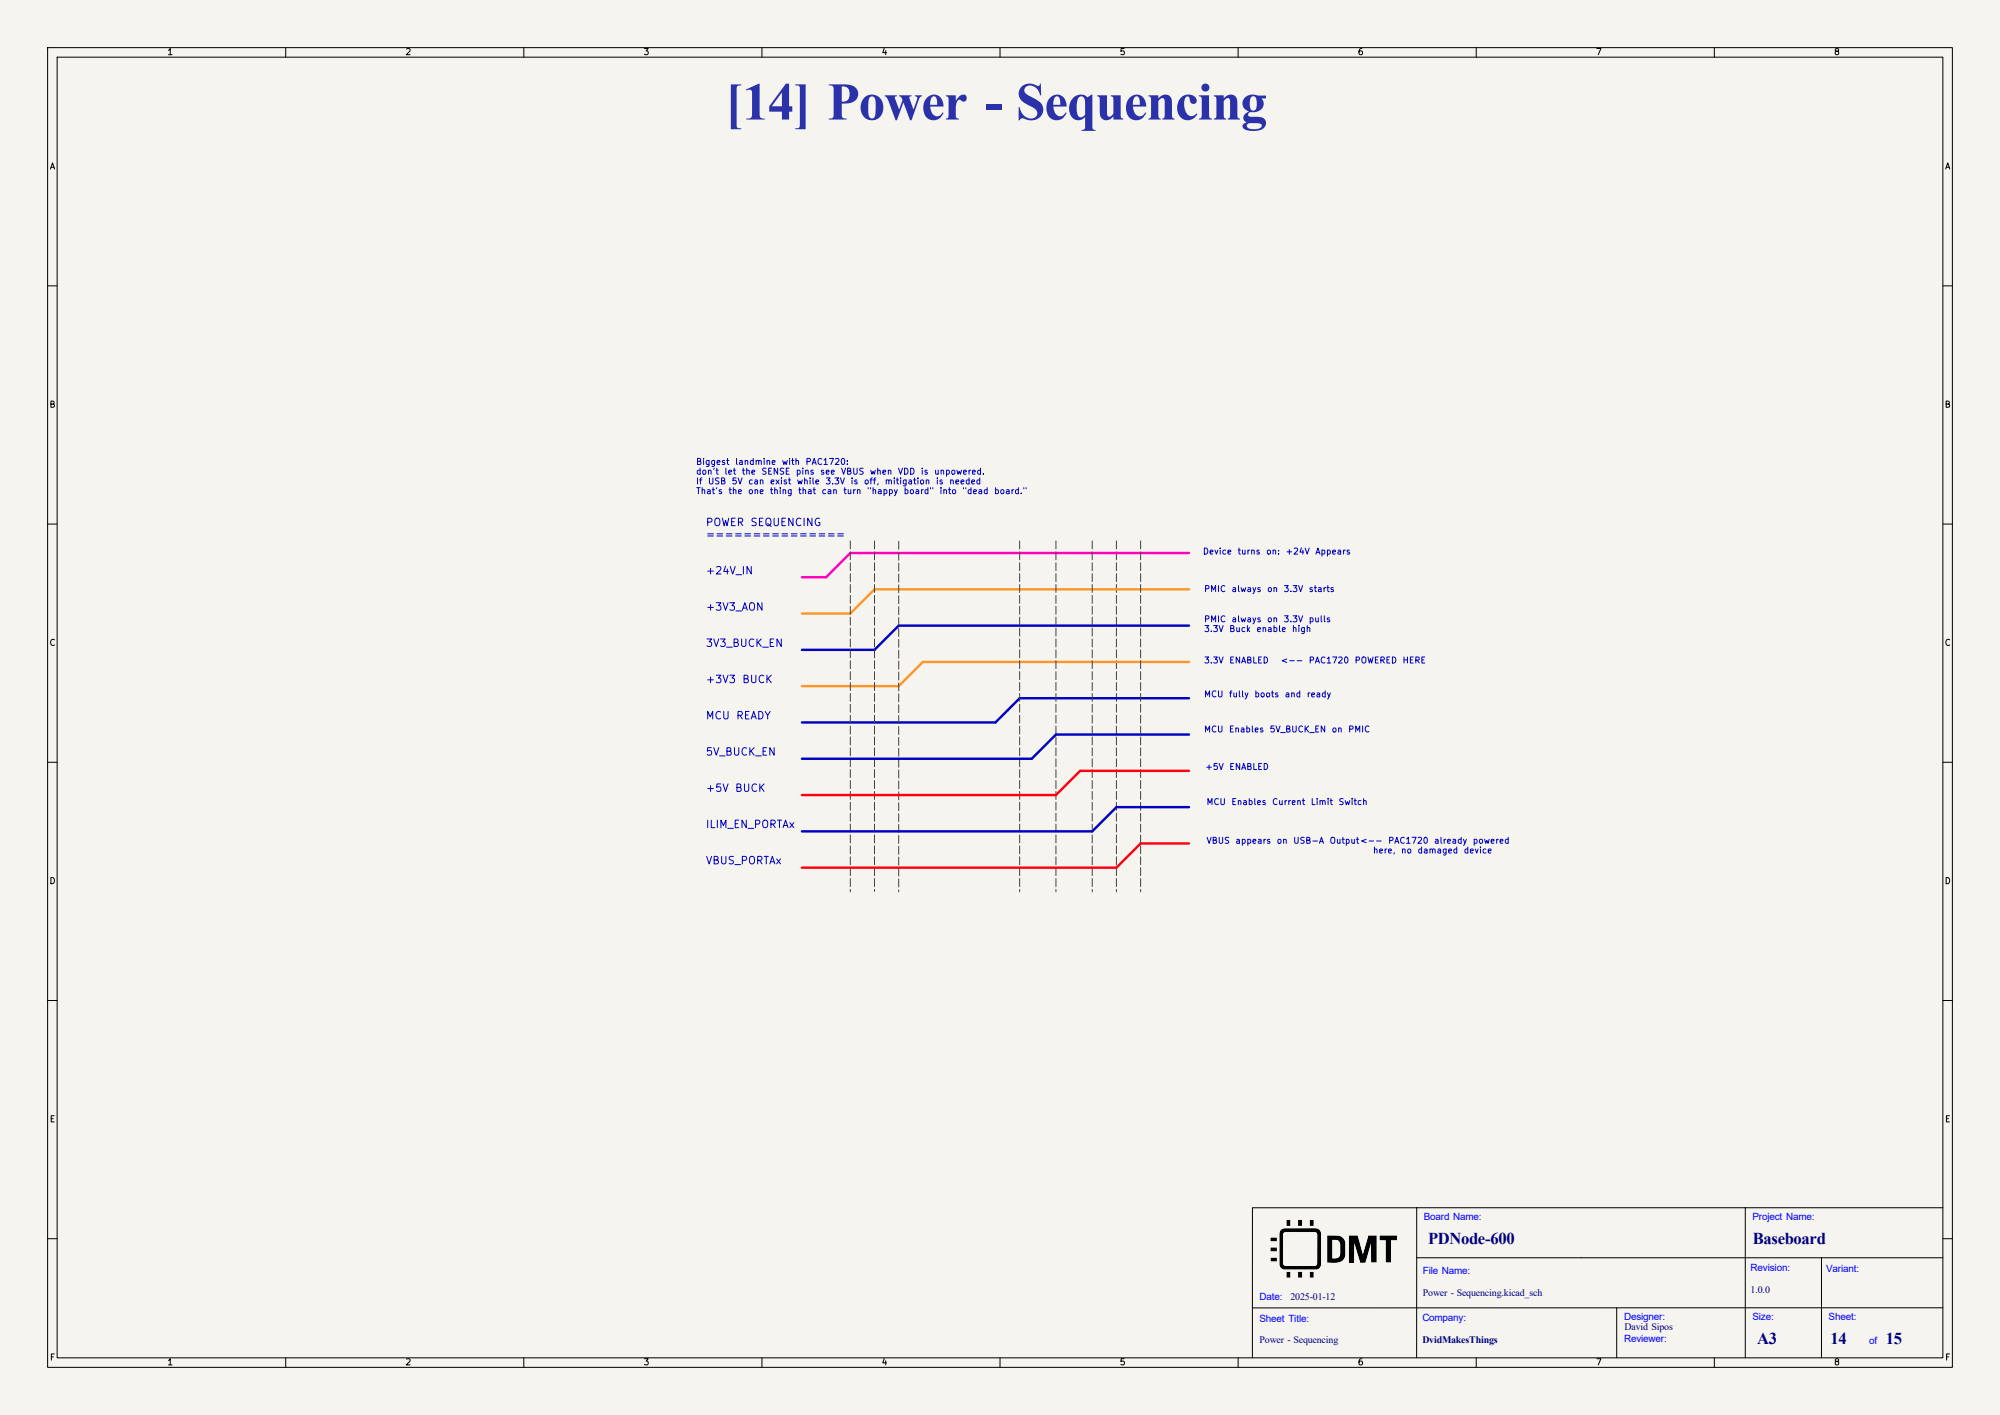
[picture p59: page 14]

PMIC always on 3.3V starts Biggest landmine with PAC1720:
don't let the SENSE pins see VBUS when VDD is unpowered.
If USB 5V can exist while 3.3V is off, mitigation is needed

Device turns on: +24V Appears

PMIC always on 3.3V pulls
3.3V Buck enable high

here, no damaged device MCU Enables 5V_BUCK_EN on PMIC

MCU Enables Current Limit Switch<-- PAC1720 already powered

VBUS appears on USB-A Output

File Name: Sheet Title: Power - Sequencing

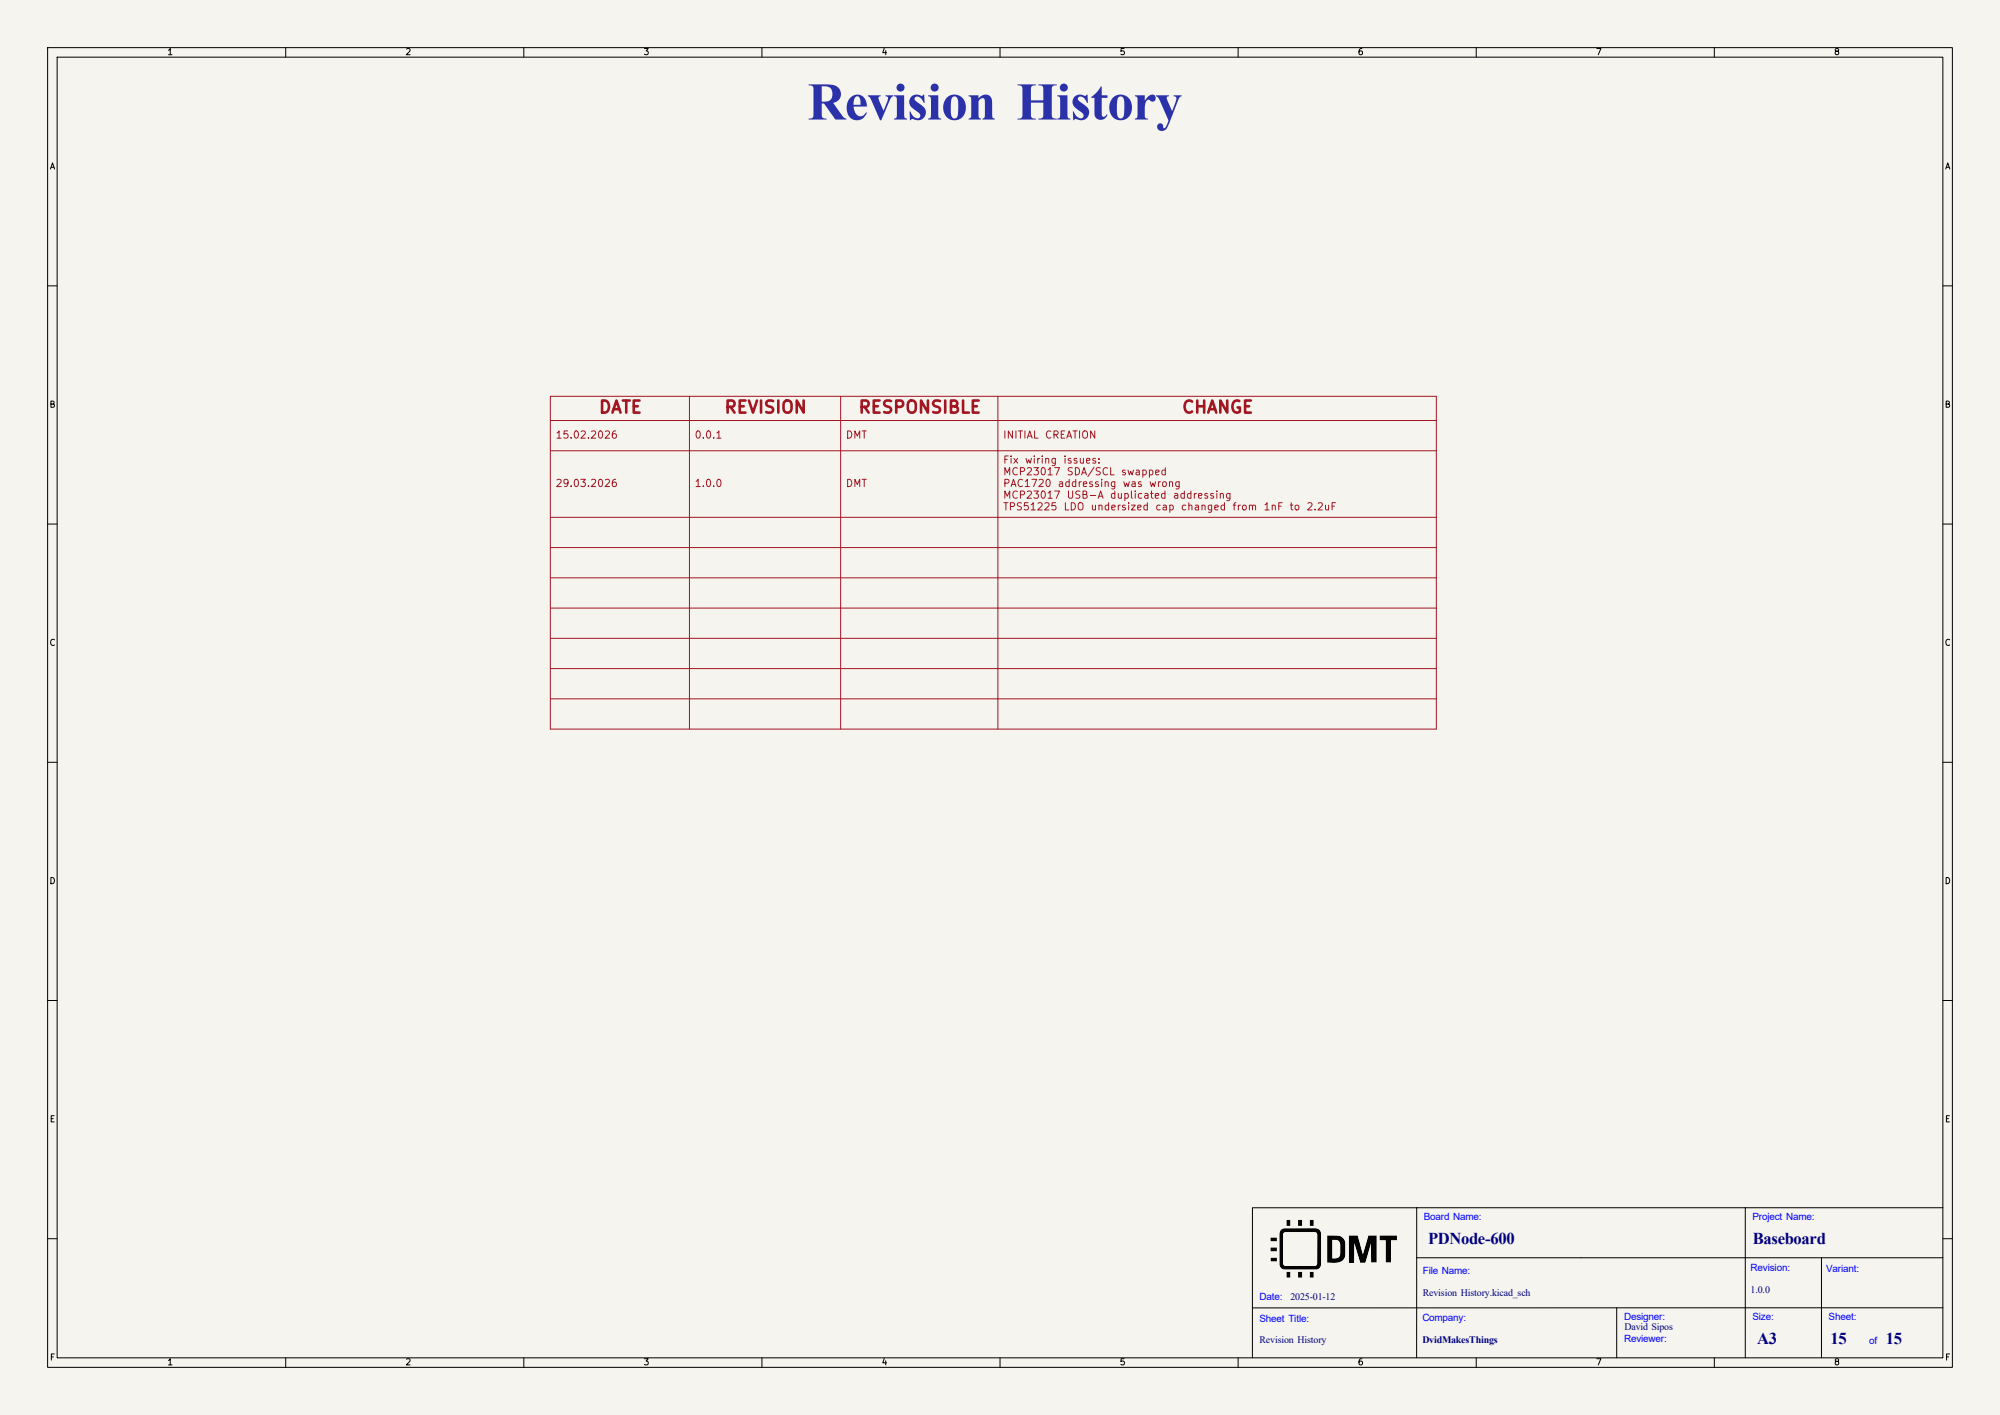
[picture p60: page 15]

TPS51225 LDO undersized cap changed from 1nF to 2.2uF Revision History

DATE | REVISION | RESPONSIBLE | CHANGE

15.02.2026 | 0.0.1 | DMT | INITIAL CREATION

29.03.2026 | 1.0.0 | DMT | Fix wiring issues: MCP23017 SDA/SCL swapped PAC1720 addressing was wrong MCP23017 USB-A duplicated addressing

File Name: Sheet Title: Revision History
