DvidMakesThings/HW_PDNode-600-Pro/src/HardwareDesign/1.0.0/PDCard-4242_100/jlcpcb/Documentation/0-PCB.pdf

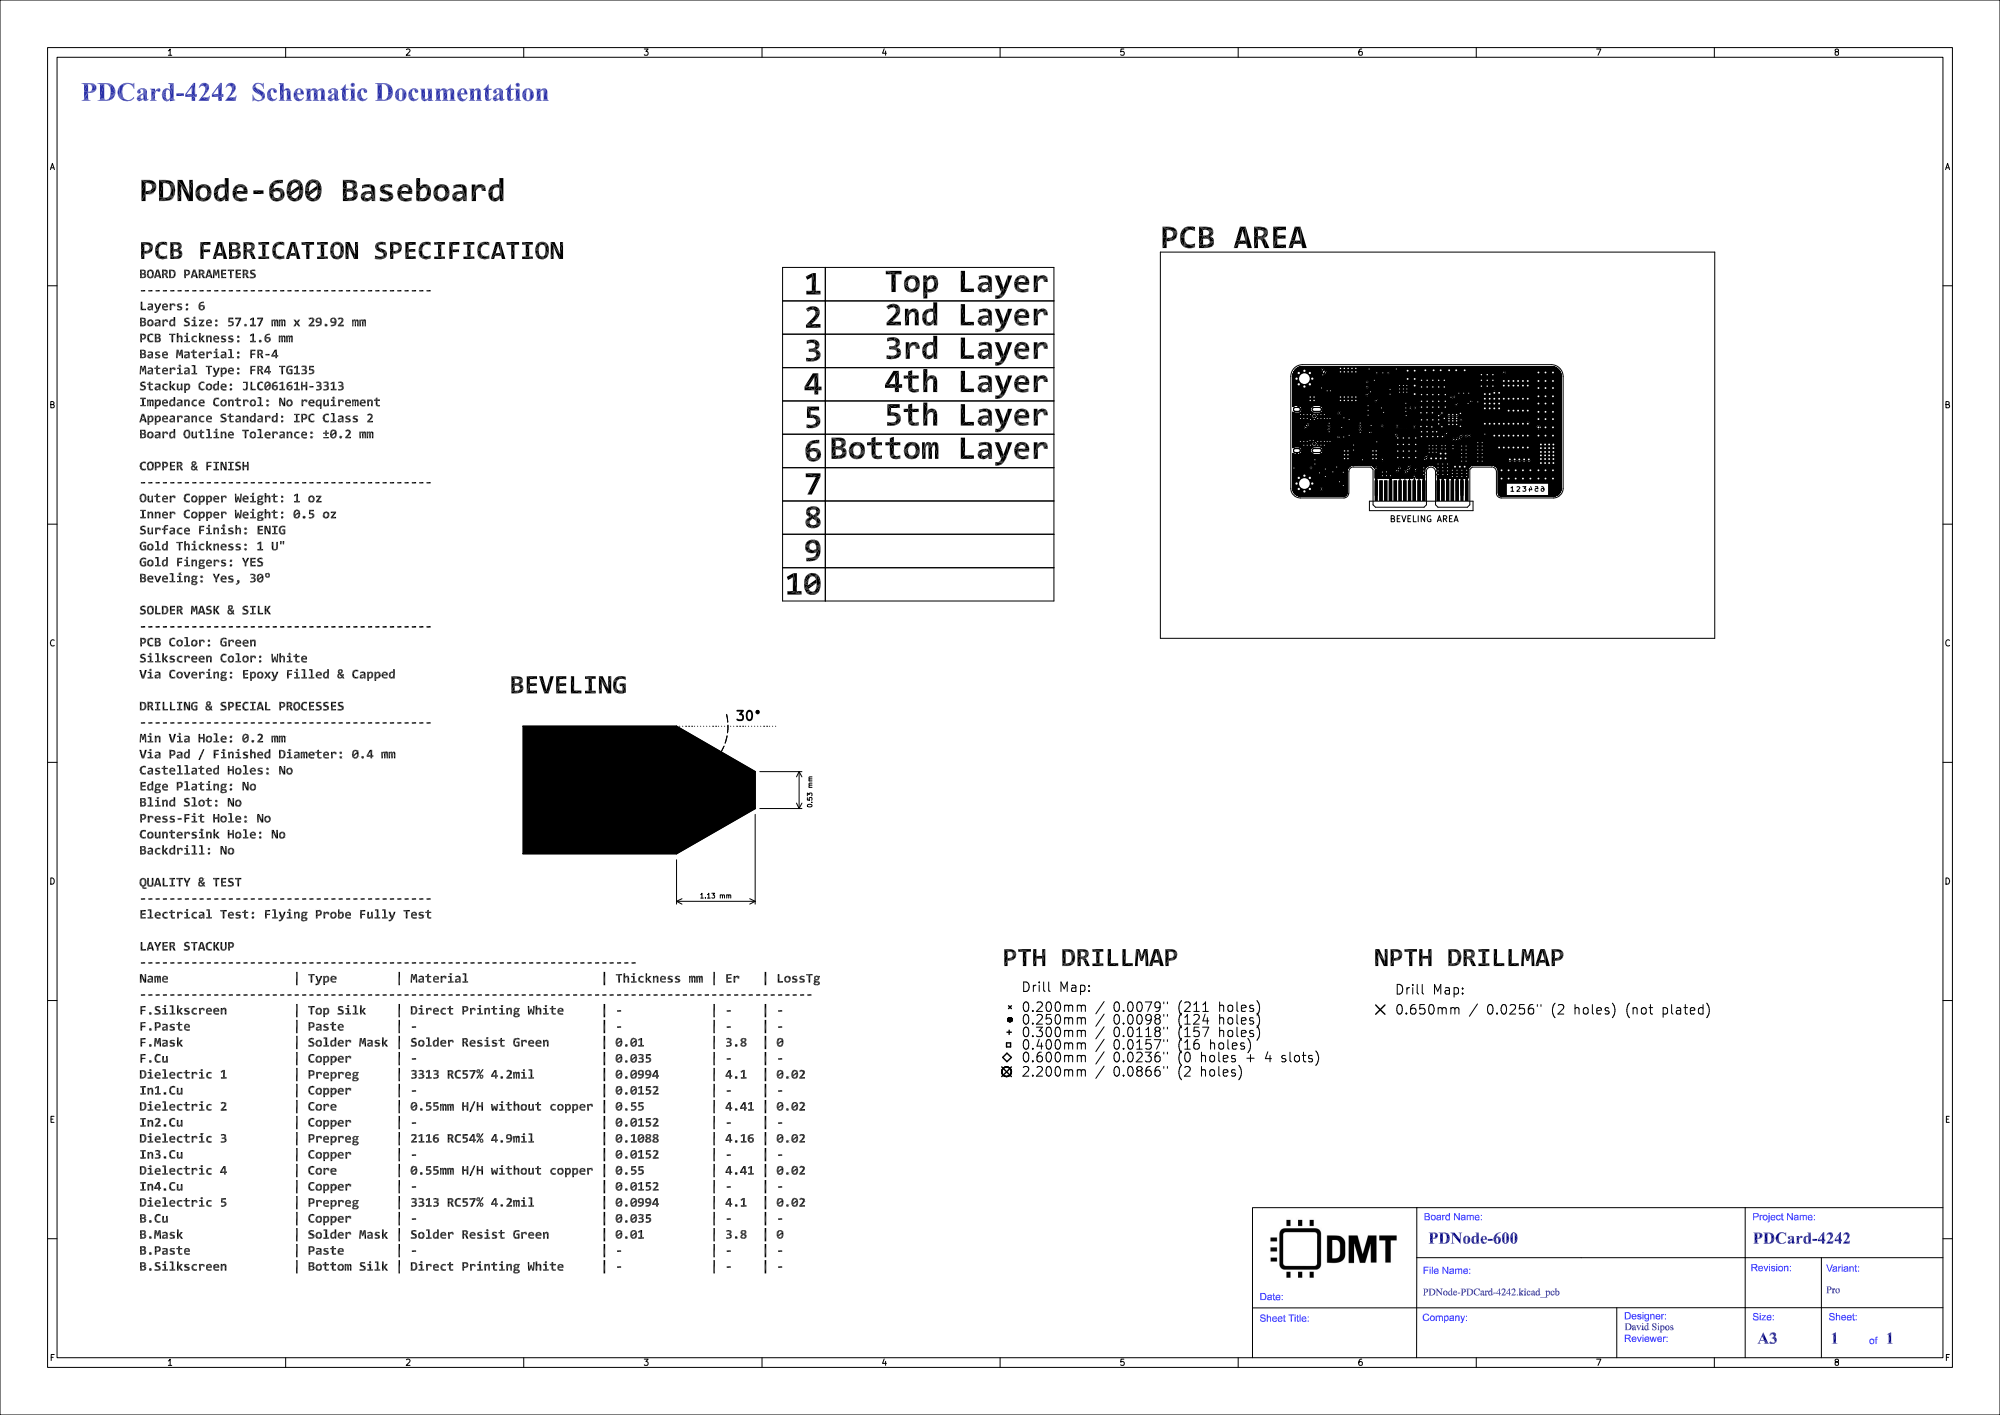
[picture p66: page 1]
