DvidMakesThings/HW_PDNode-600-Pro/src/HardwareDesign/1.0.0/PDCard-4242_100/jlcpcb/Documentation/1-Top.pdf

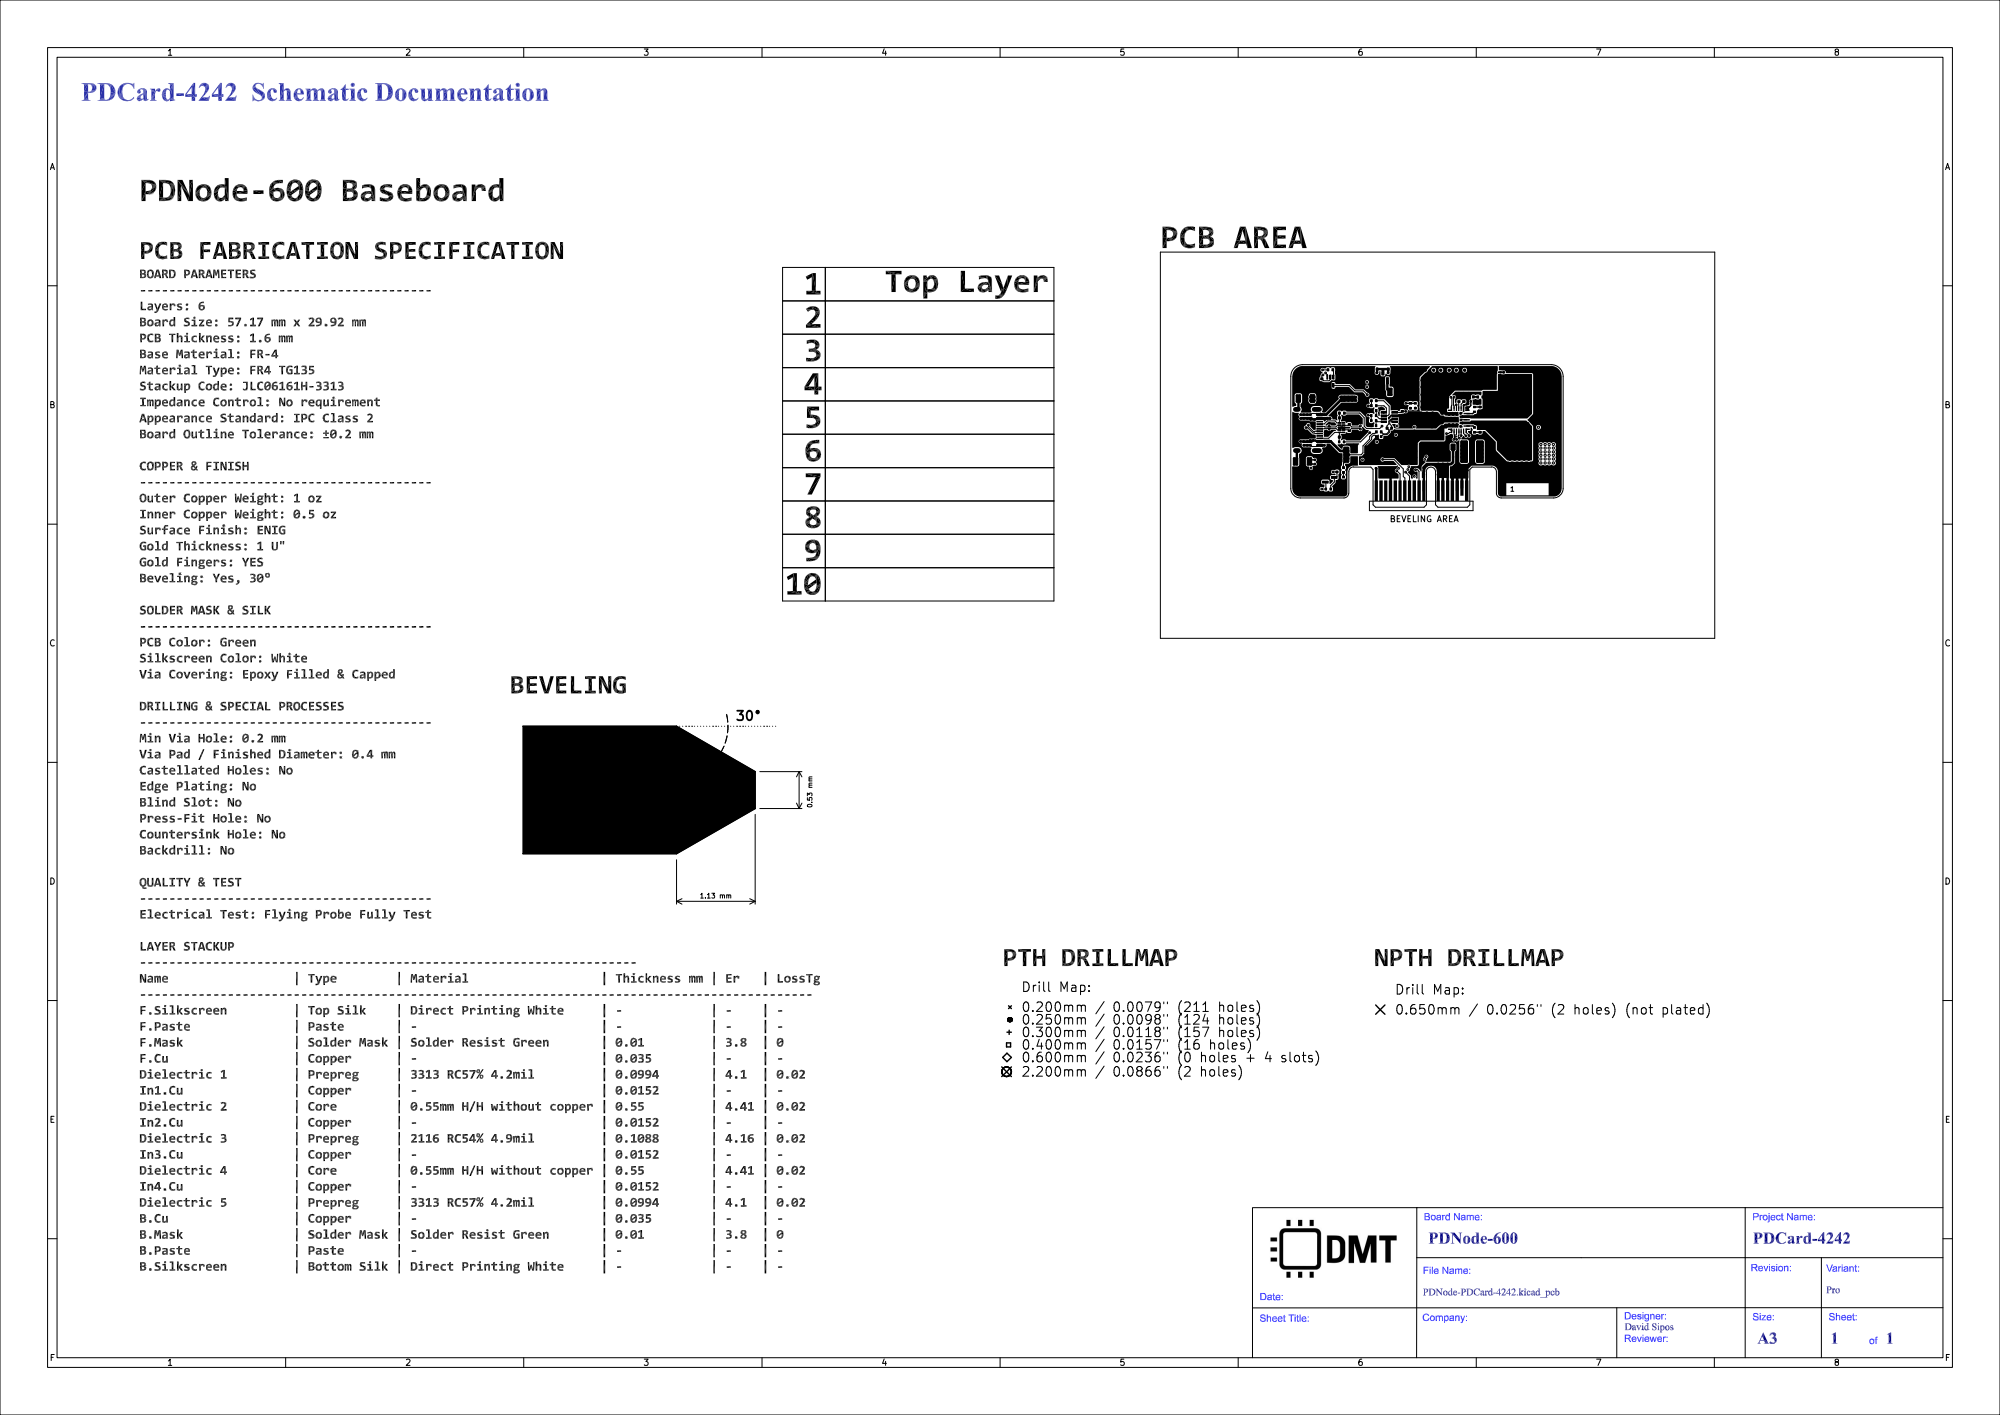
[picture p67: page 1]
