DvidMakesThings/HW_PDNode-600-Pro/src/HardwareDesign/1.0.0/PDCard-4242_100/jlcpcb/Documentation/10-Silk-Bottom.pdf

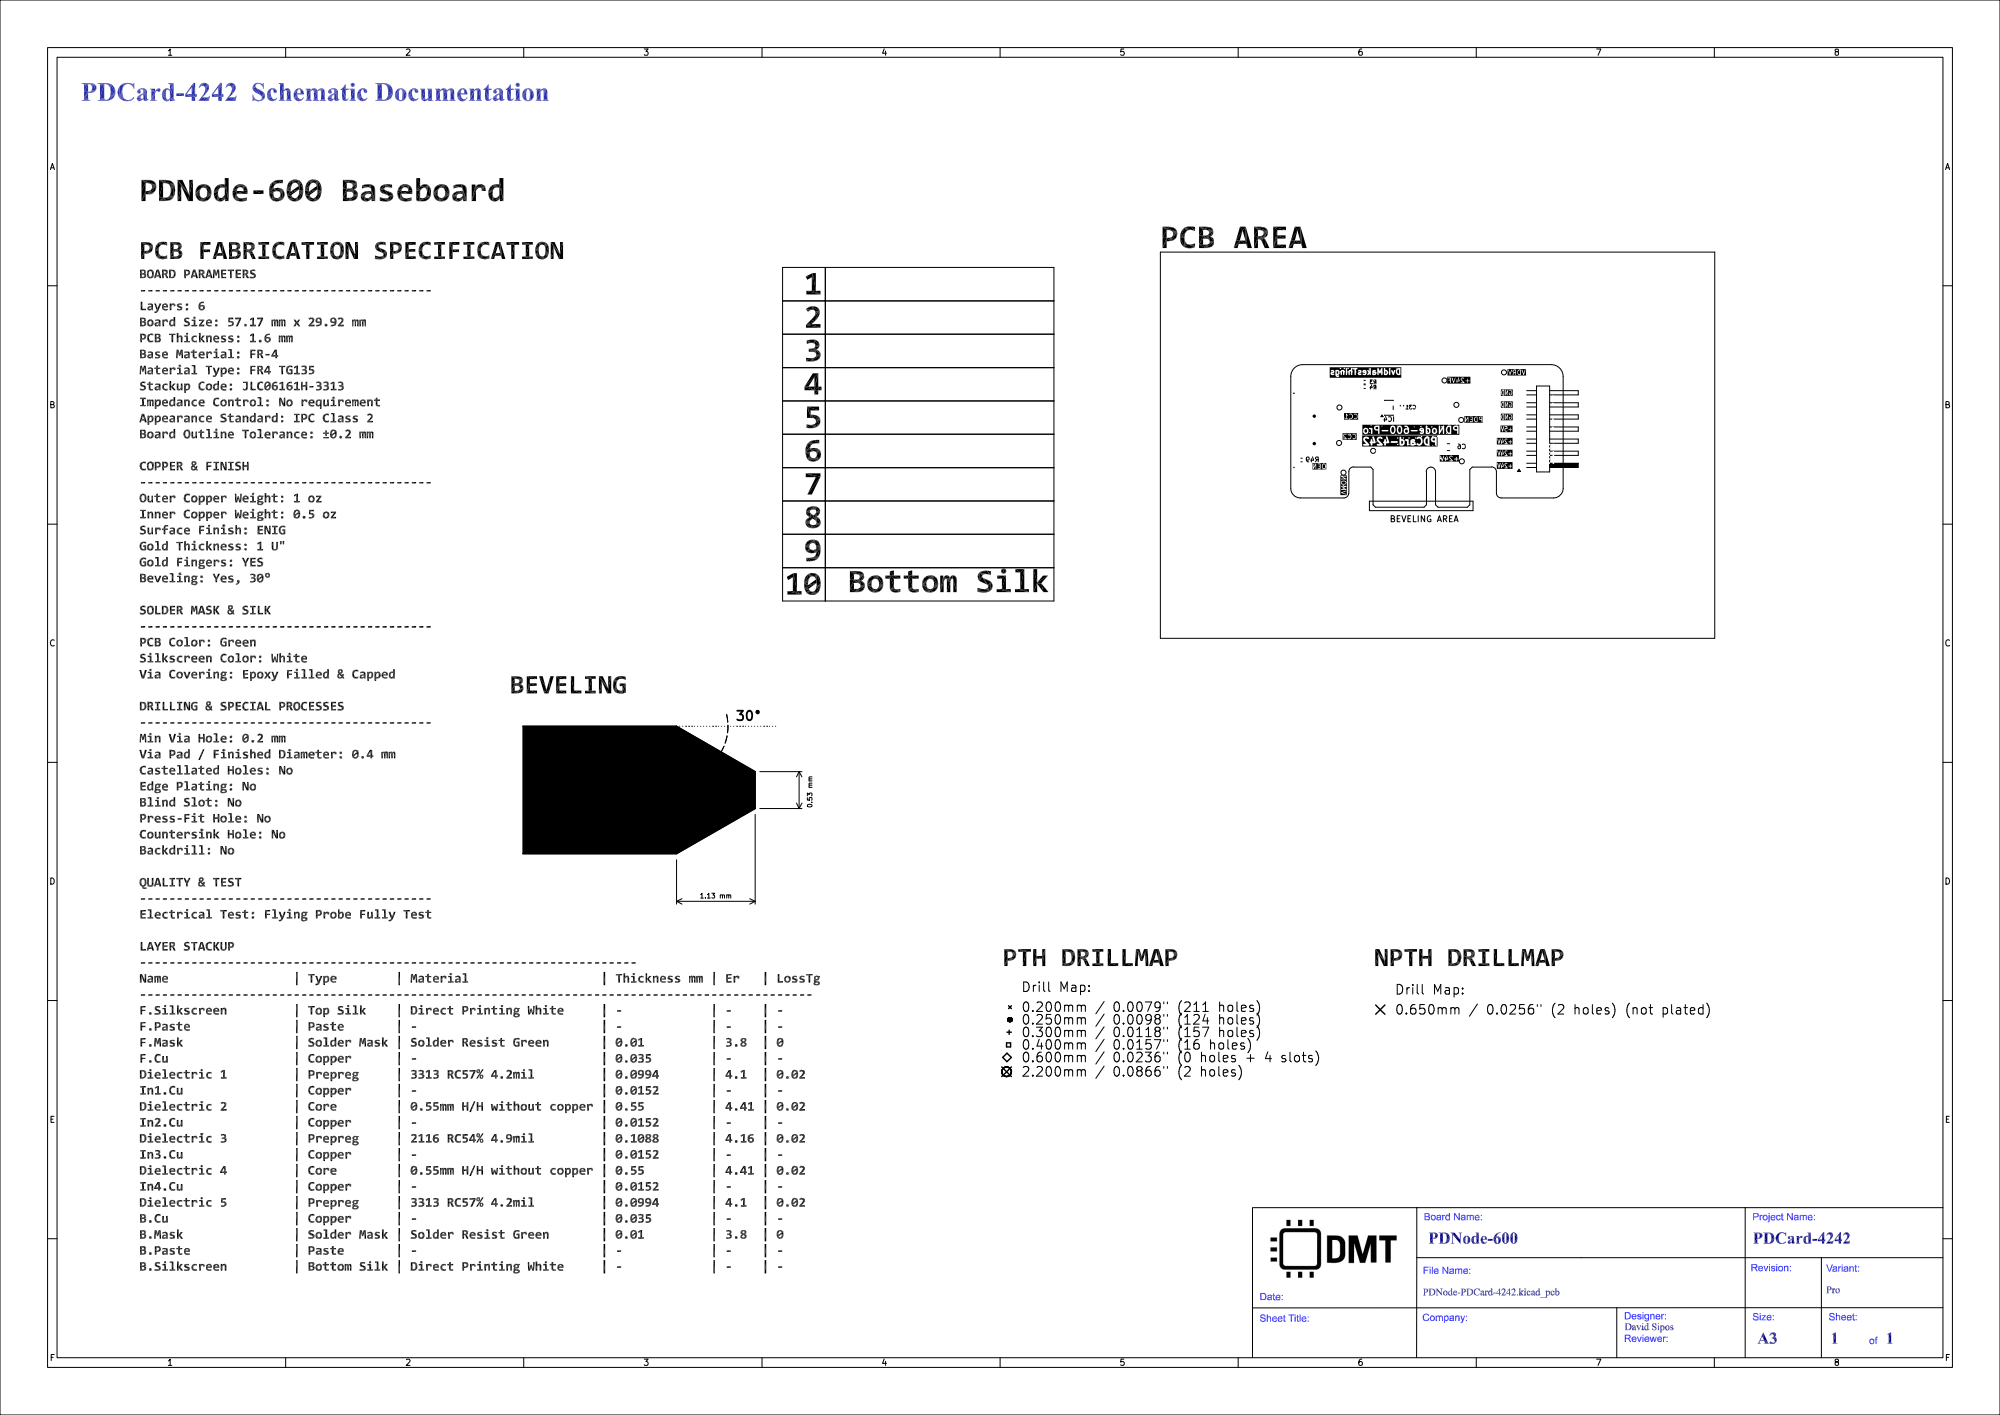
[picture p68: page 1]
