DvidMakesThings/HW_PDNode-600-Pro/src/HardwareDesign/1.0.0/PDCard-4242_100/jlcpcb/Documentation/2-Inner-1.pdf

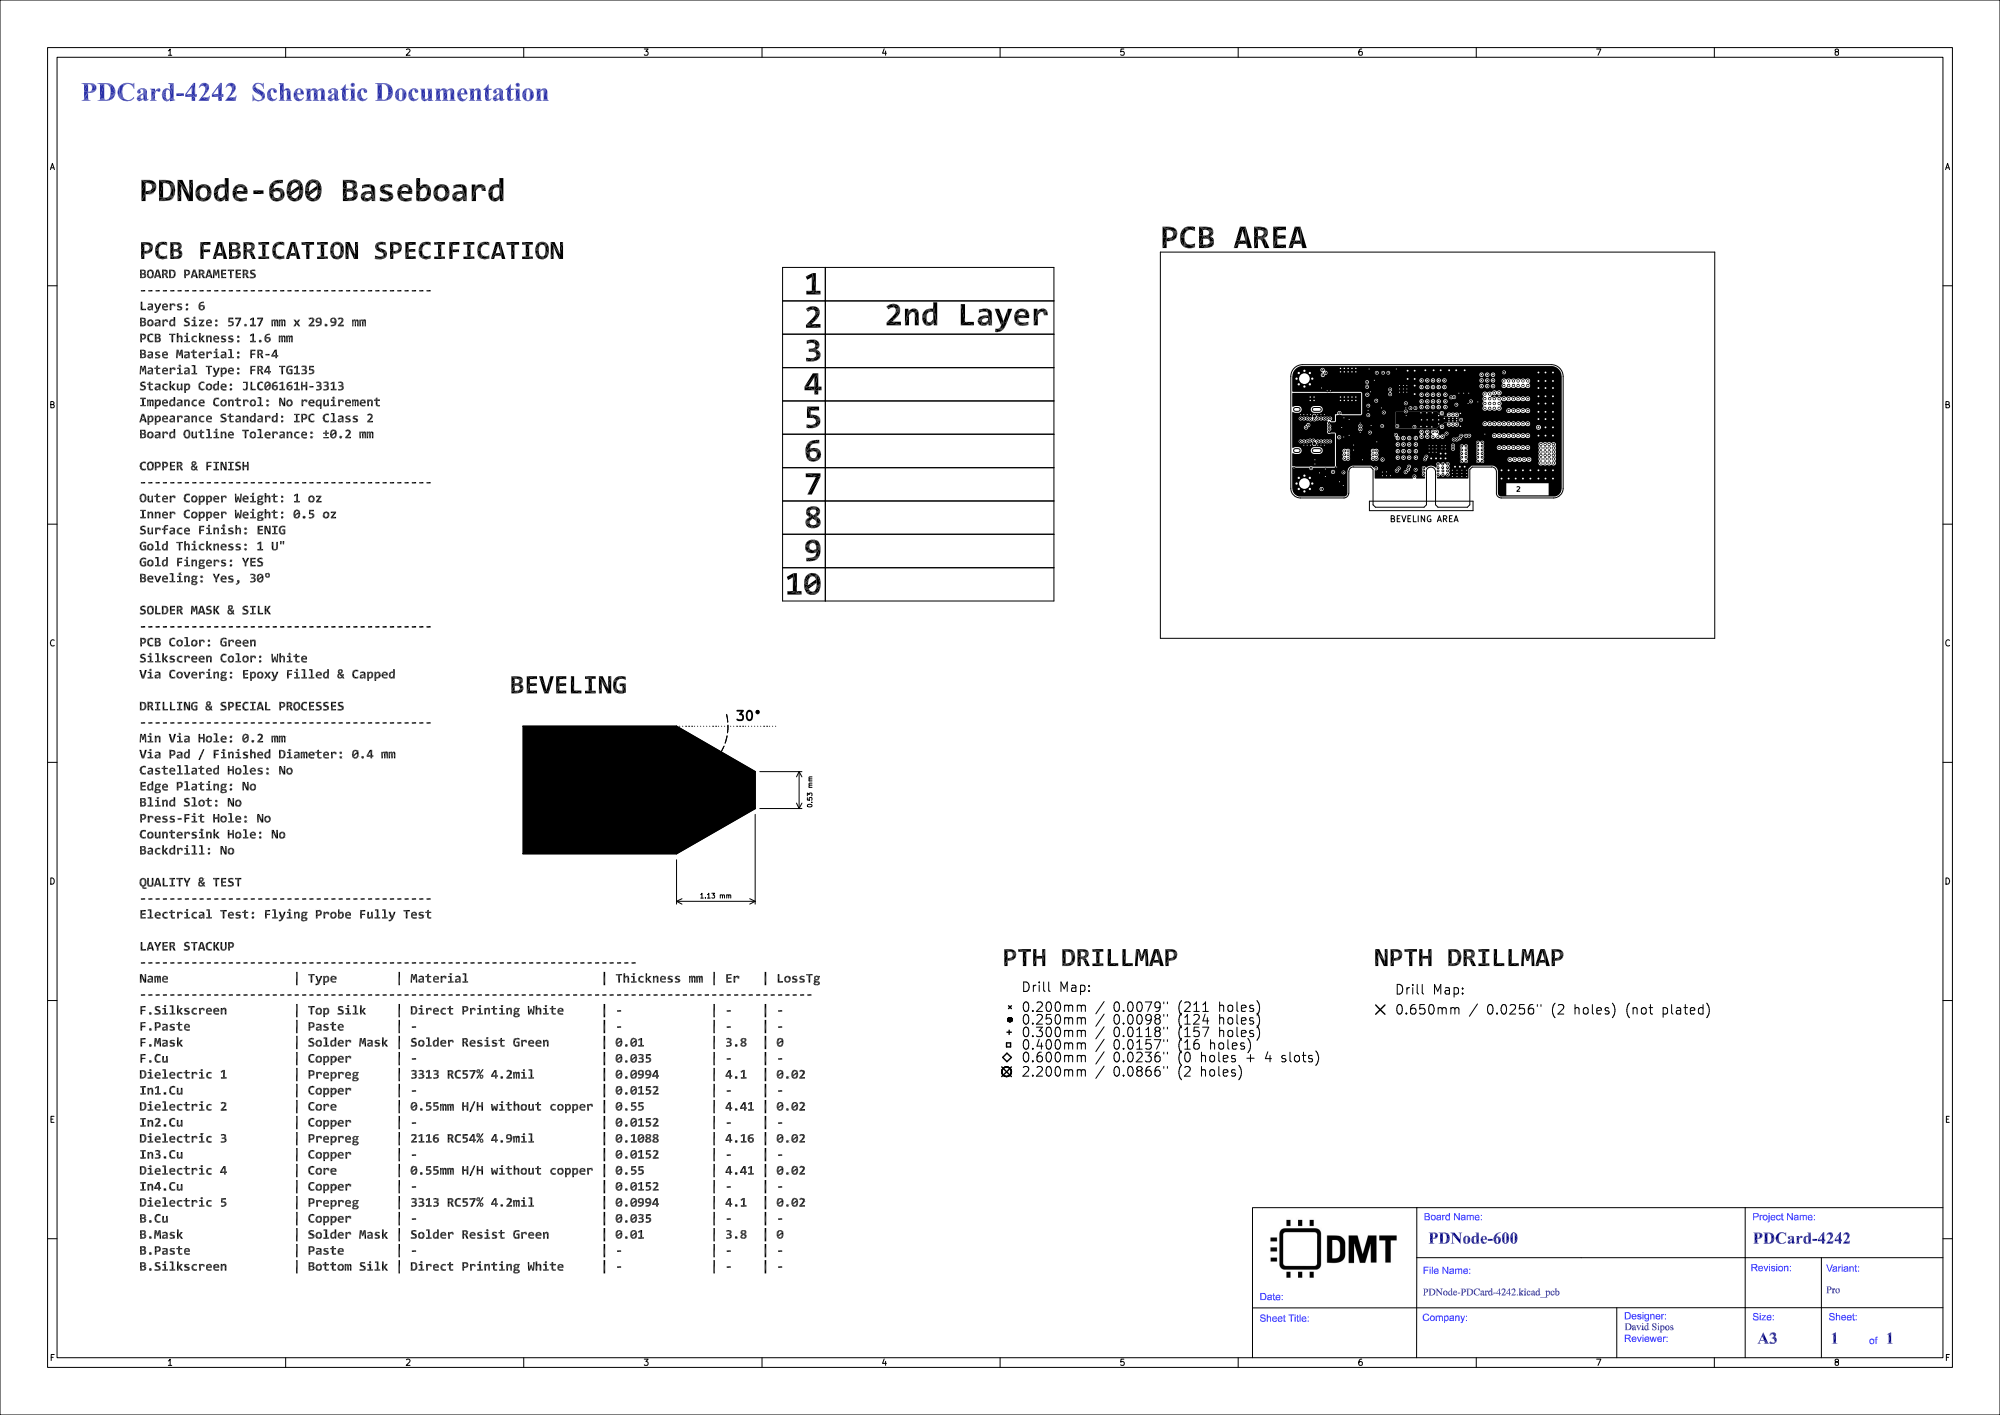
[picture p69: page 1]
