DvidMakesThings/HW_PDNode-600-Pro/src/HardwareDesign/1.0.0/PDCard-4242_100/jlcpcb/Documentation/3-Inner-2.pdf

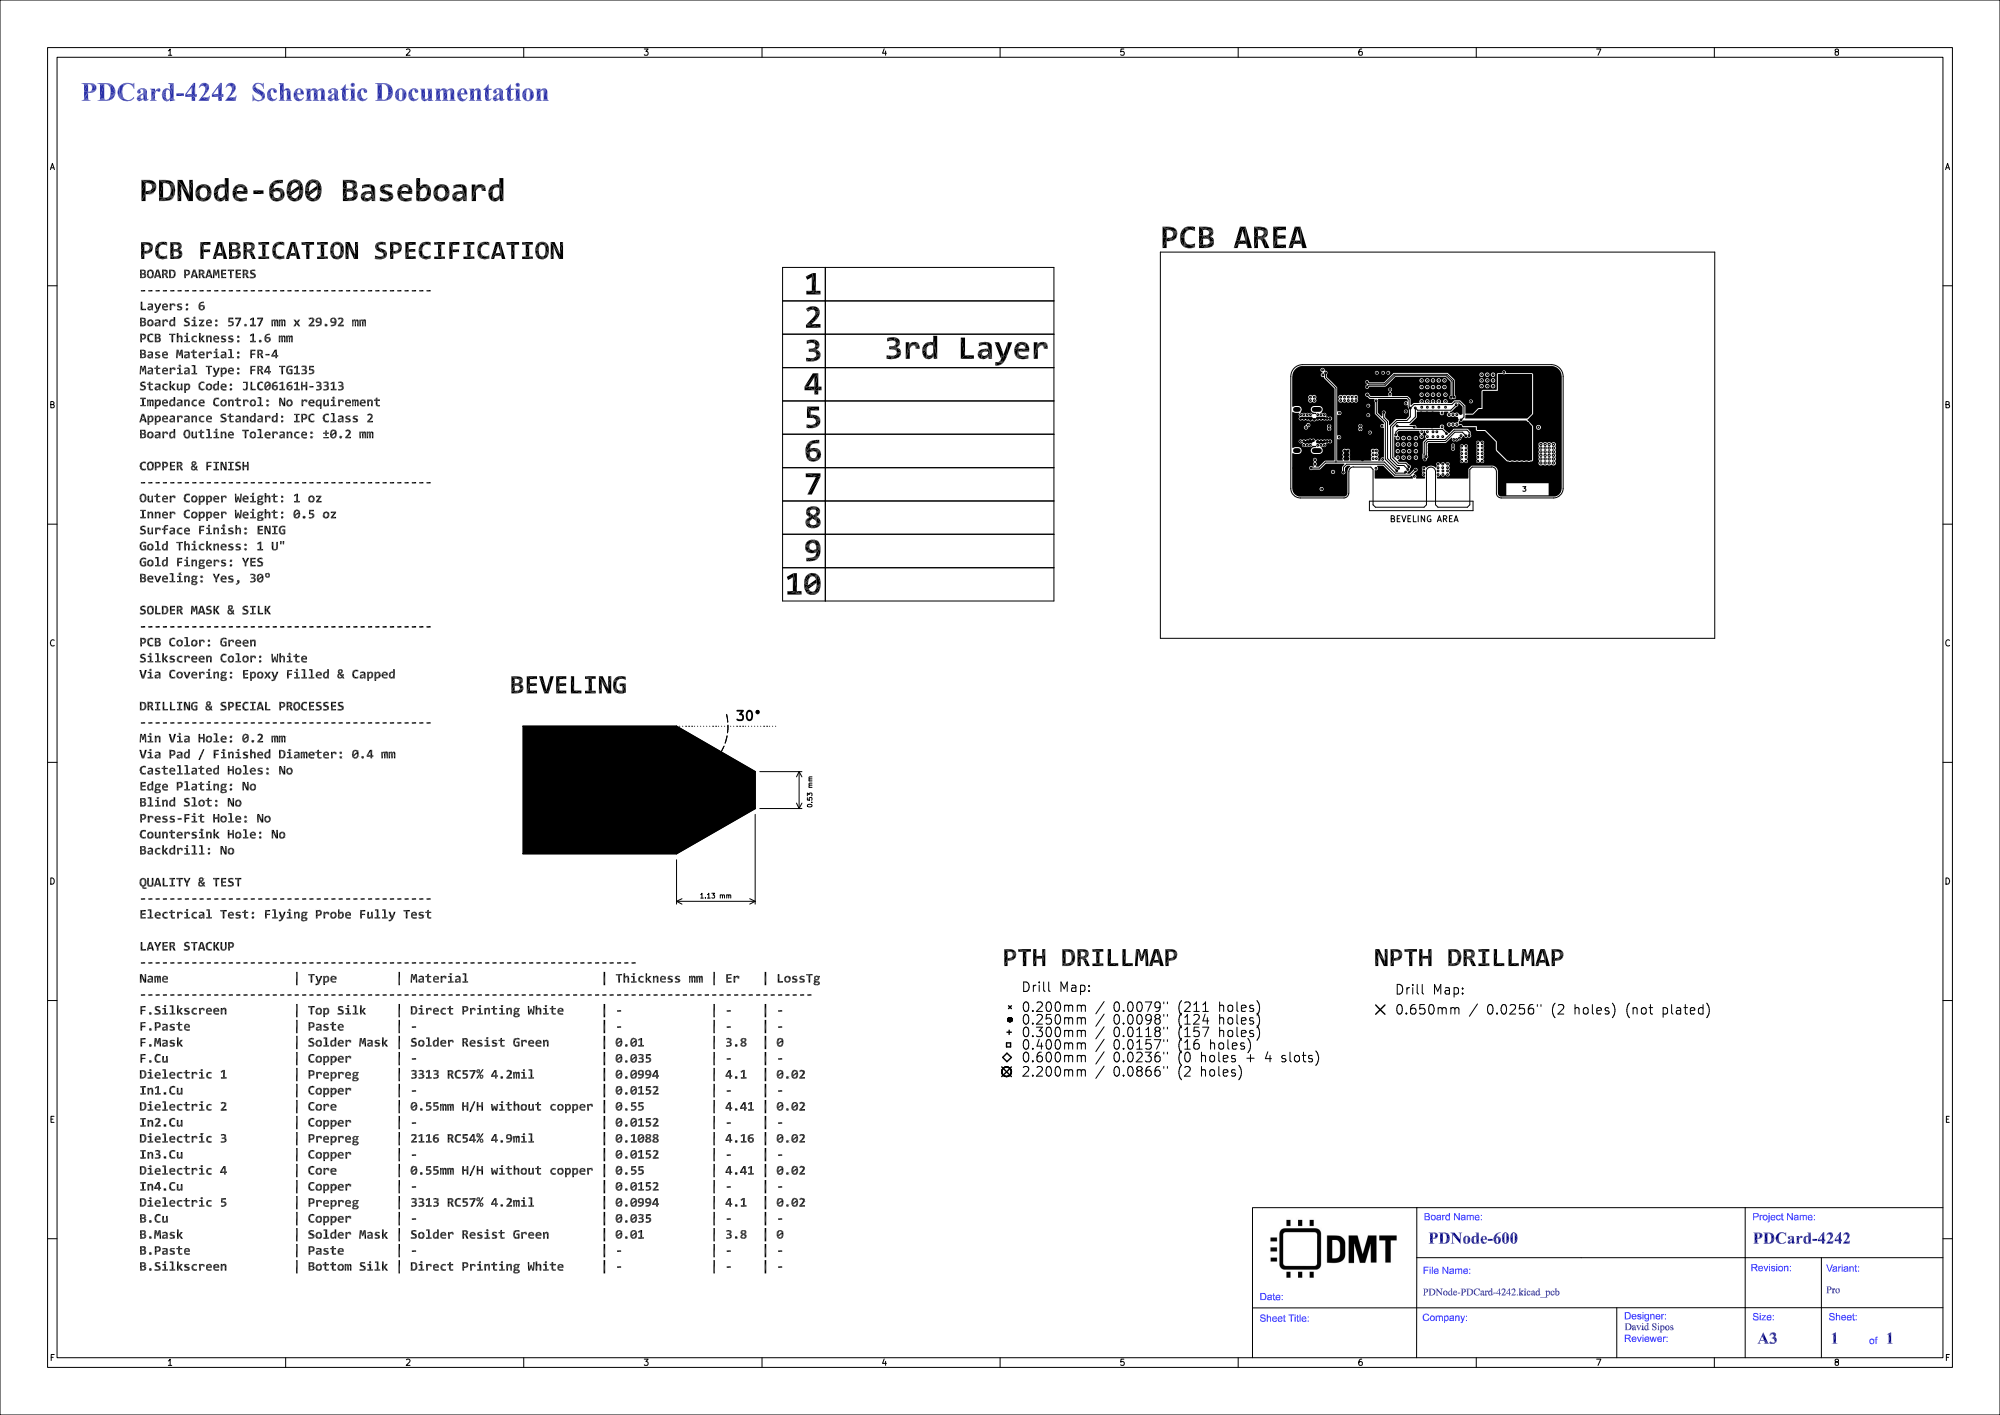
[picture p70: page 1]
