DvidMakesThings/HW_PDNode-600-Pro/src/HardwareDesign/1.0.0/PDNode-600_Pro_Baseboard_100/jlcpcb/Documentation/0-PCB.pdf

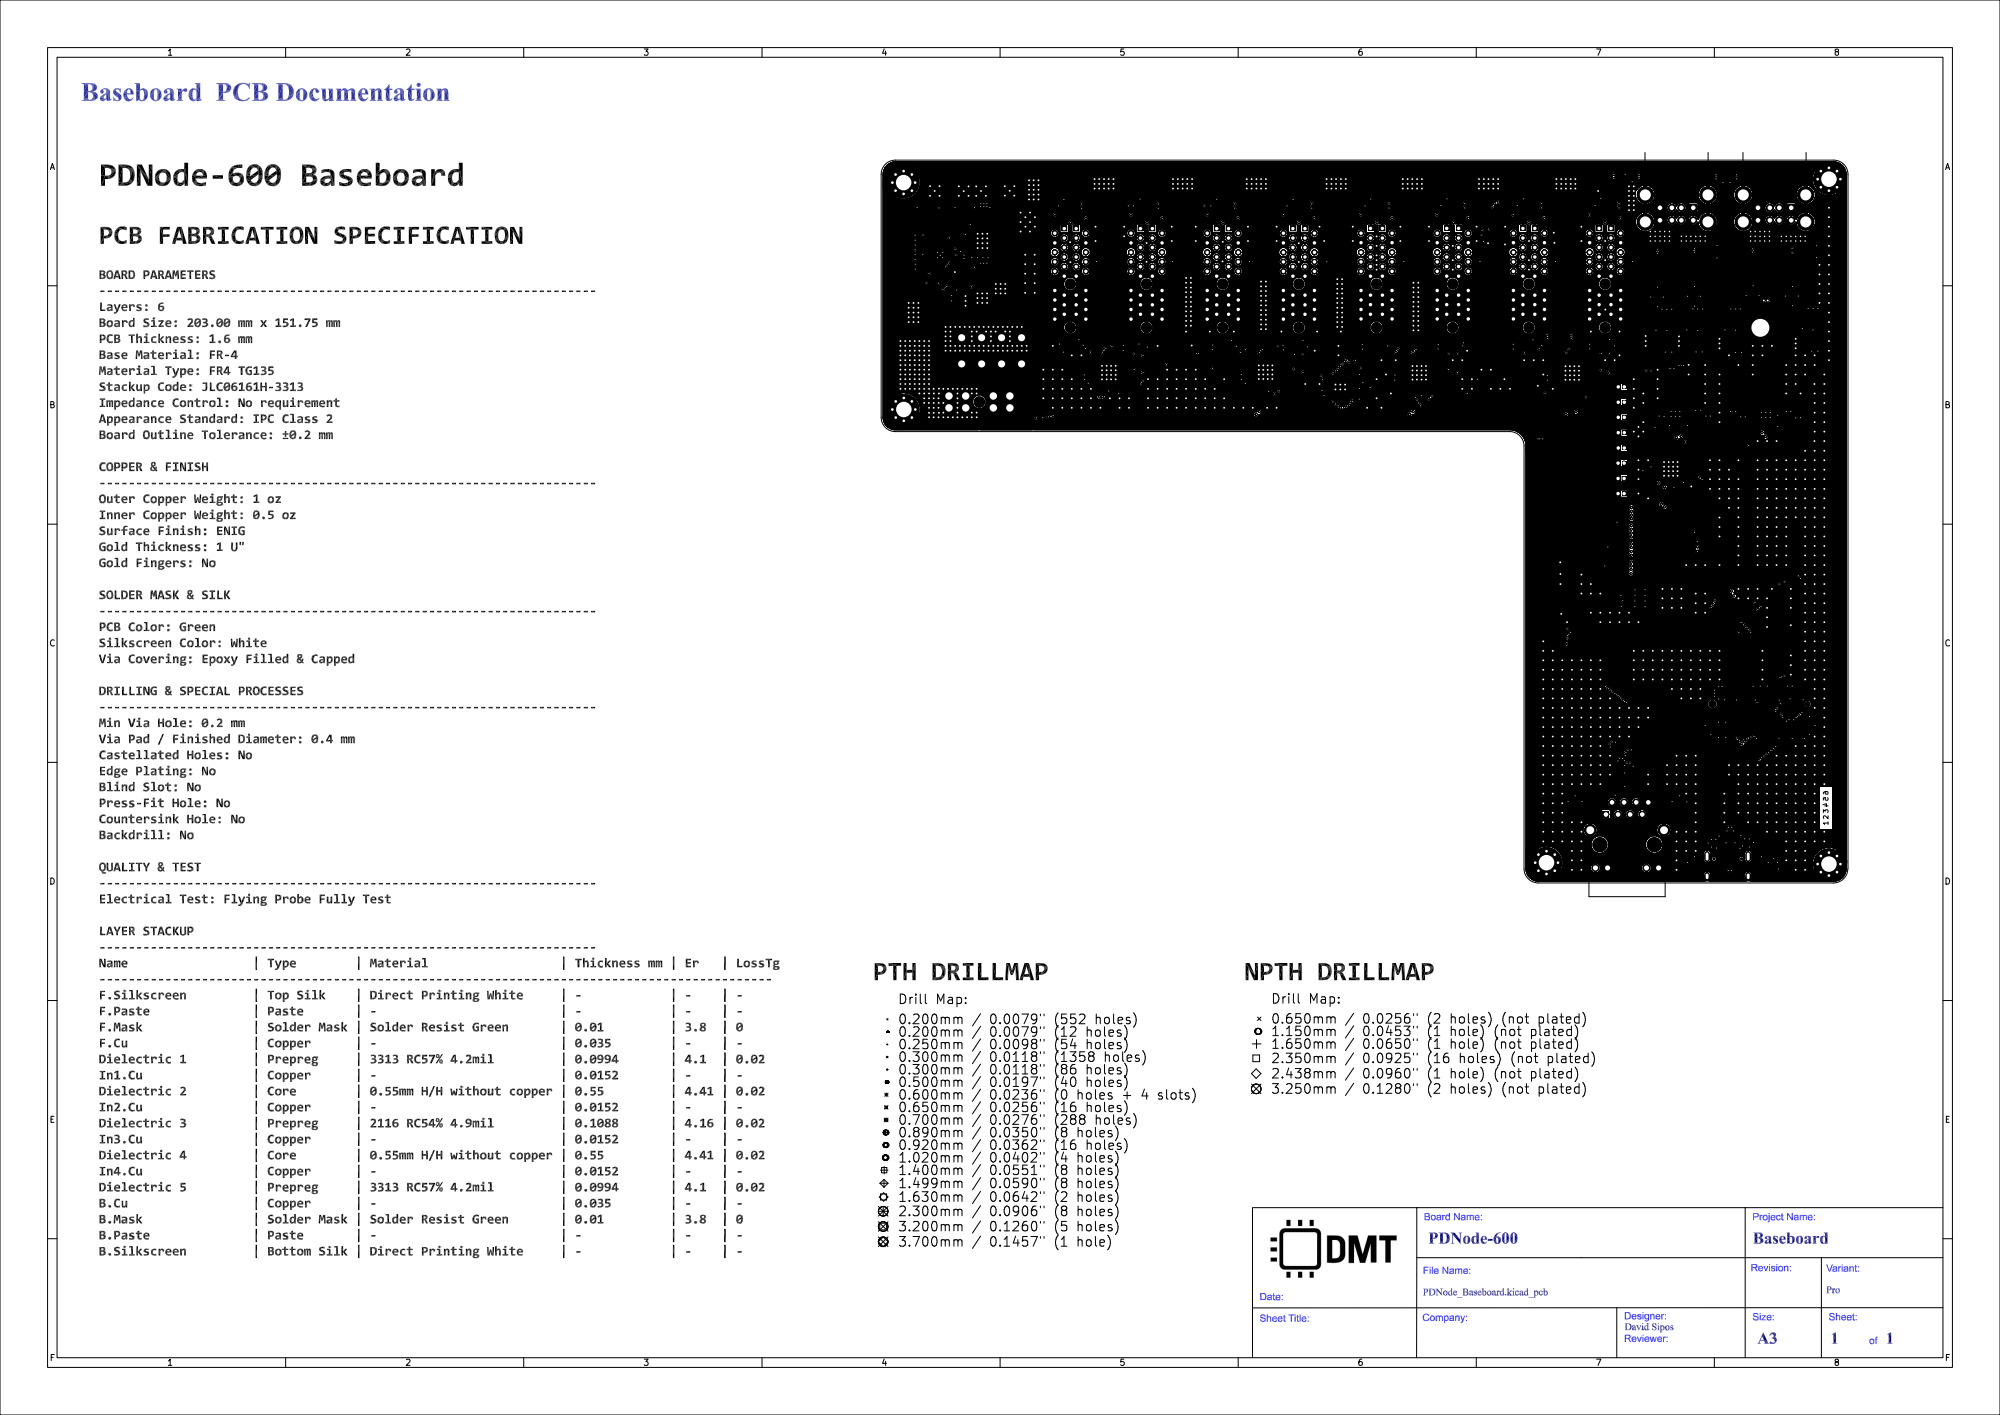
[picture p77: page 1]
