DvidMakesThings/HW_PDNode-600-Pro/src/HardwareDesign/1.0.0/PDNode-600_Pro_Baseboard_100/jlcpcb/Documentation/1-Top.pdf

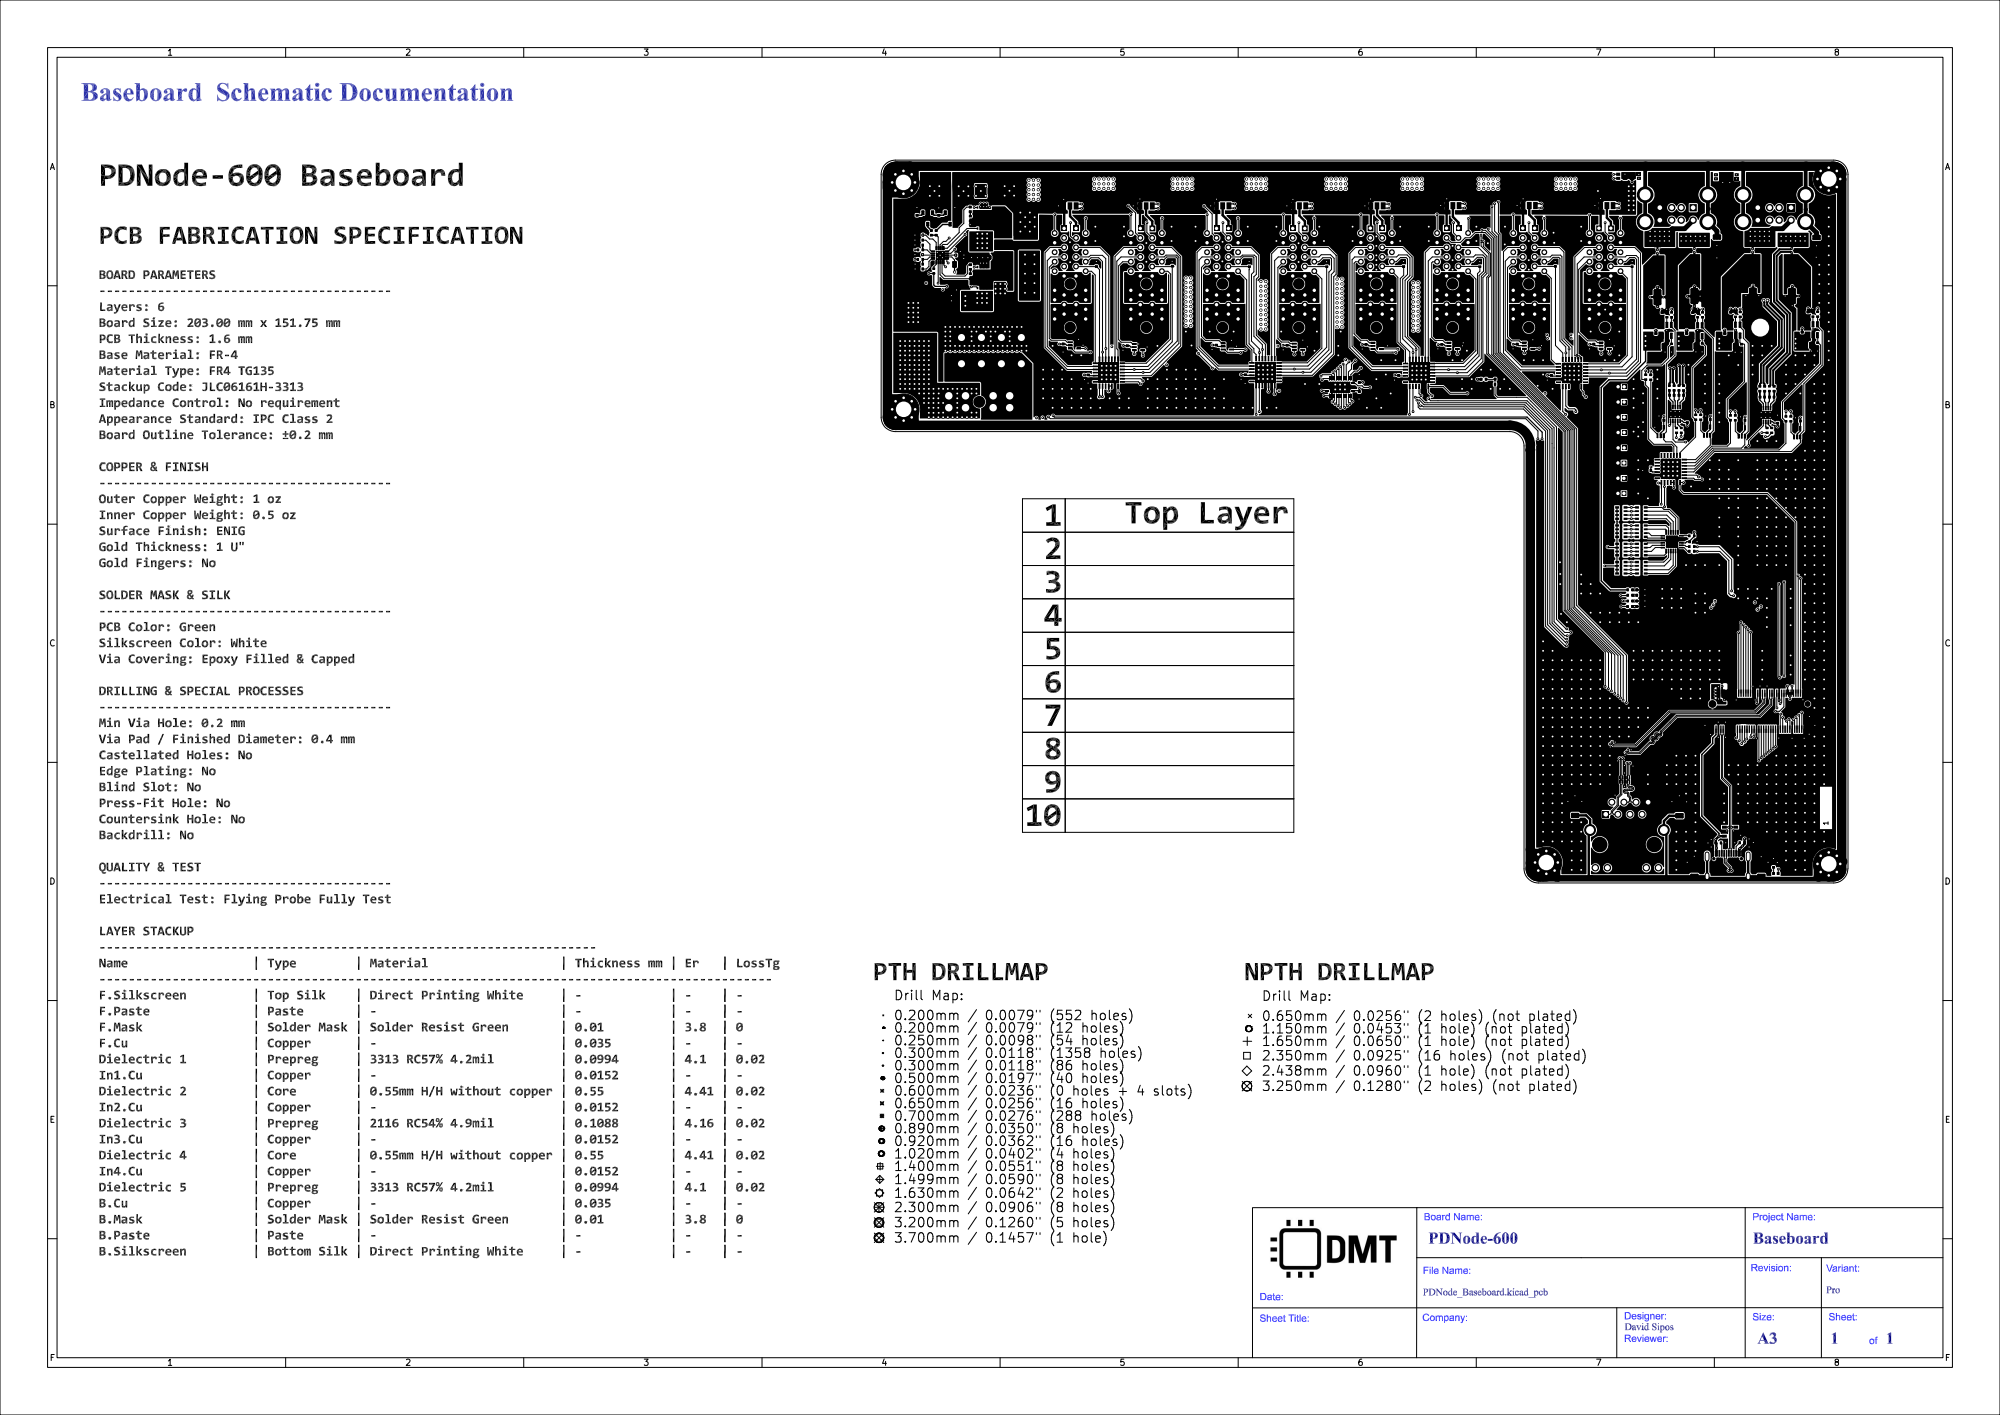
[picture p78: page 1]
