DvidMakesThings/HW_PDNode-600-Pro/src/HardwareDesign/1.0.0/PDNode-600_Pro_Baseboard_100/jlcpcb/Documentation/2-Inner-1.pdf

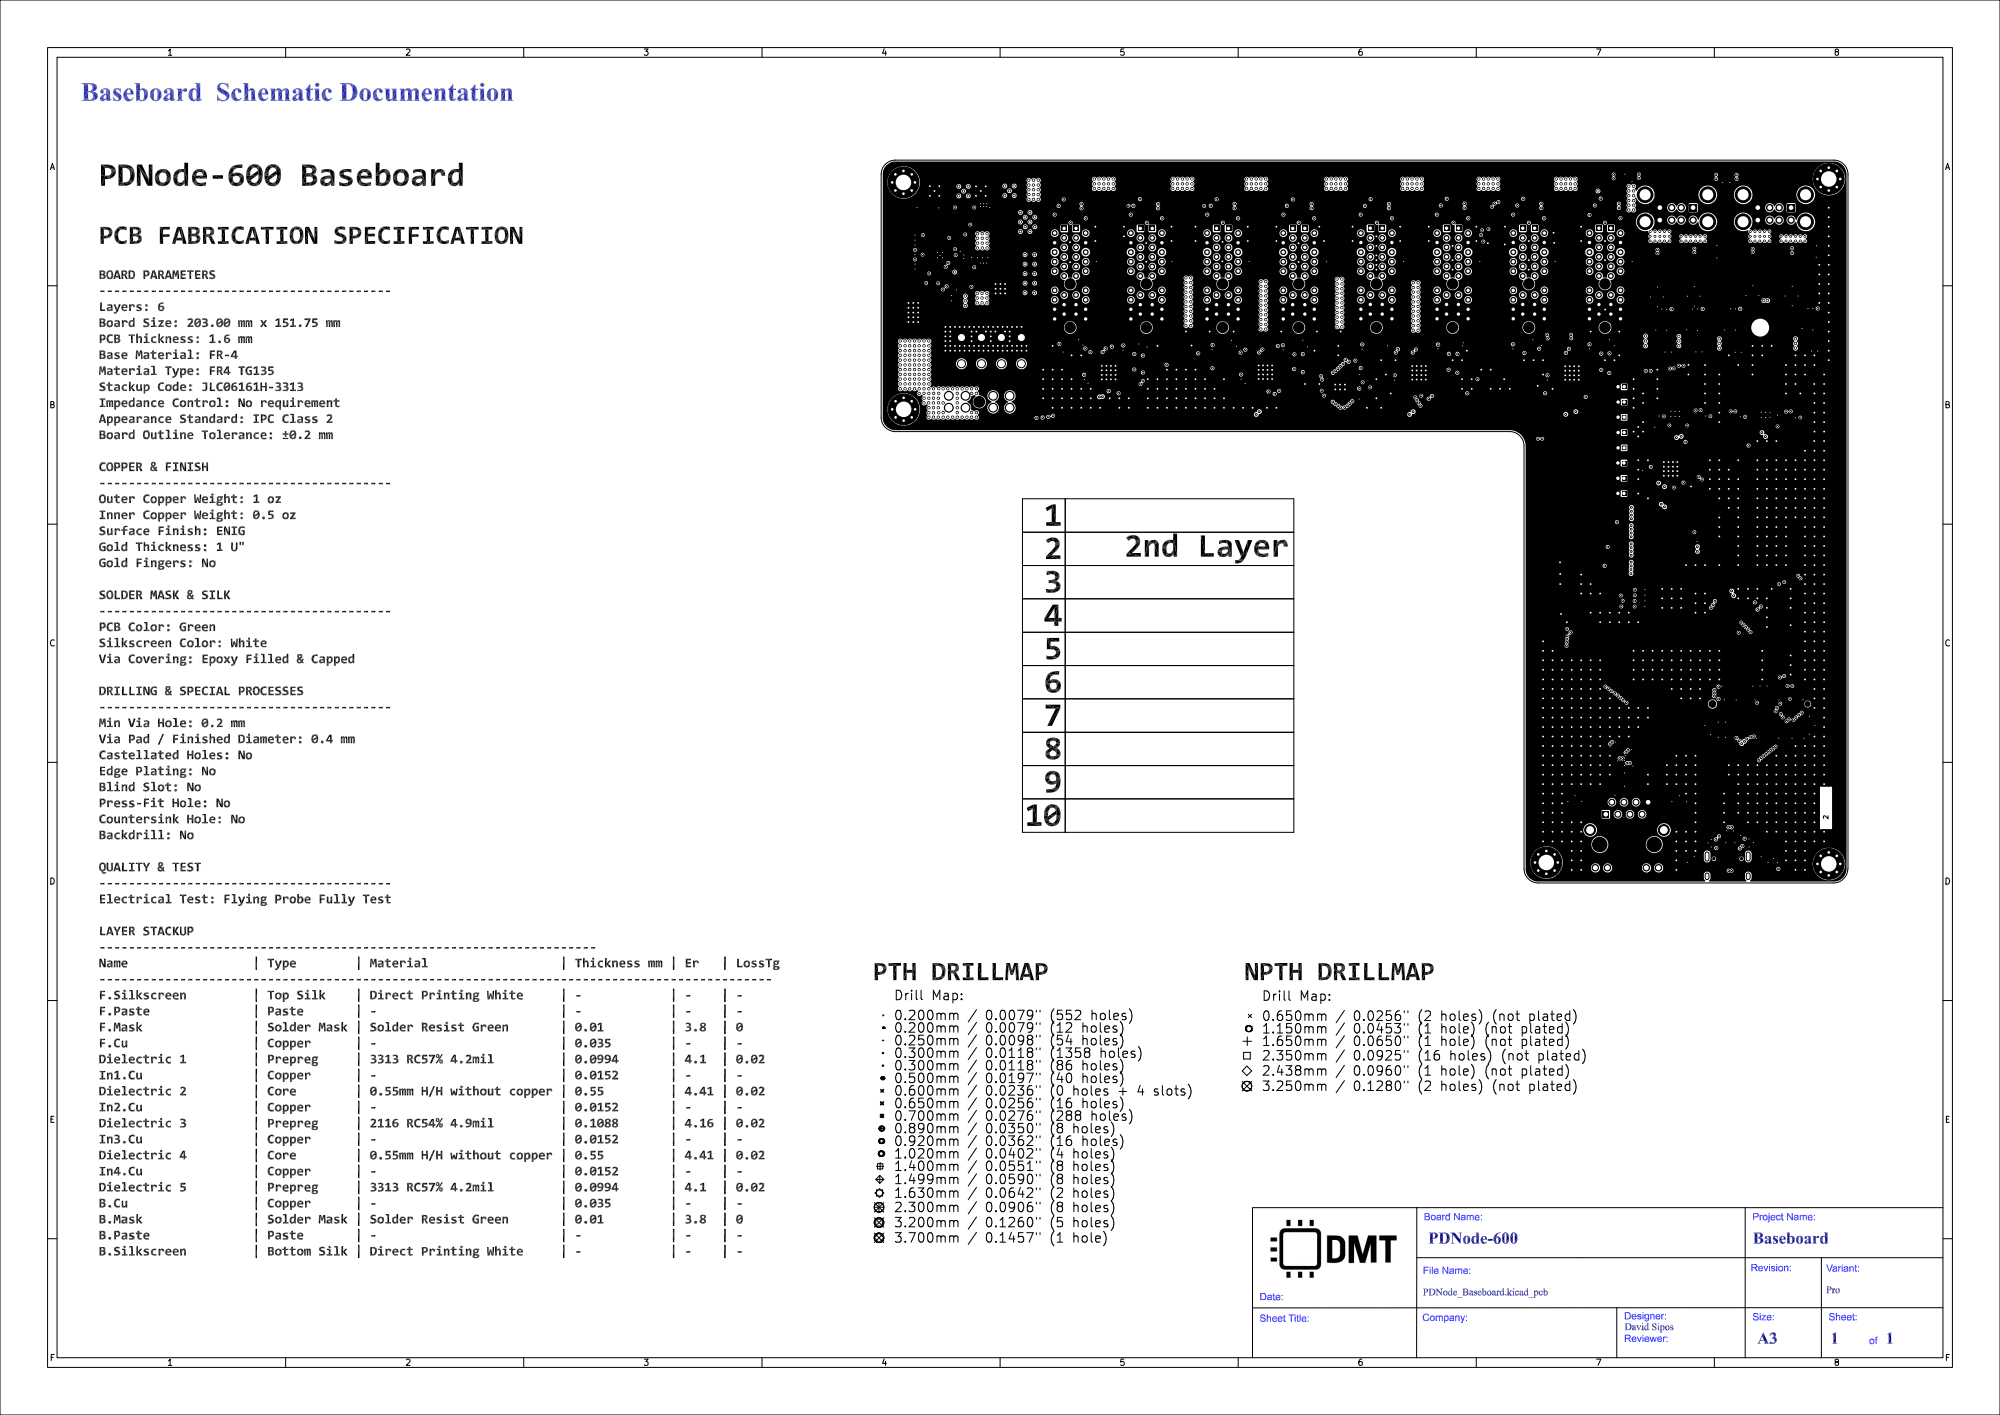
[picture p80: page 1]
