DvidMakesThings/HW_PDNode-600-Pro/src/PDF/SCH_BladeCore-M54_100.pdf

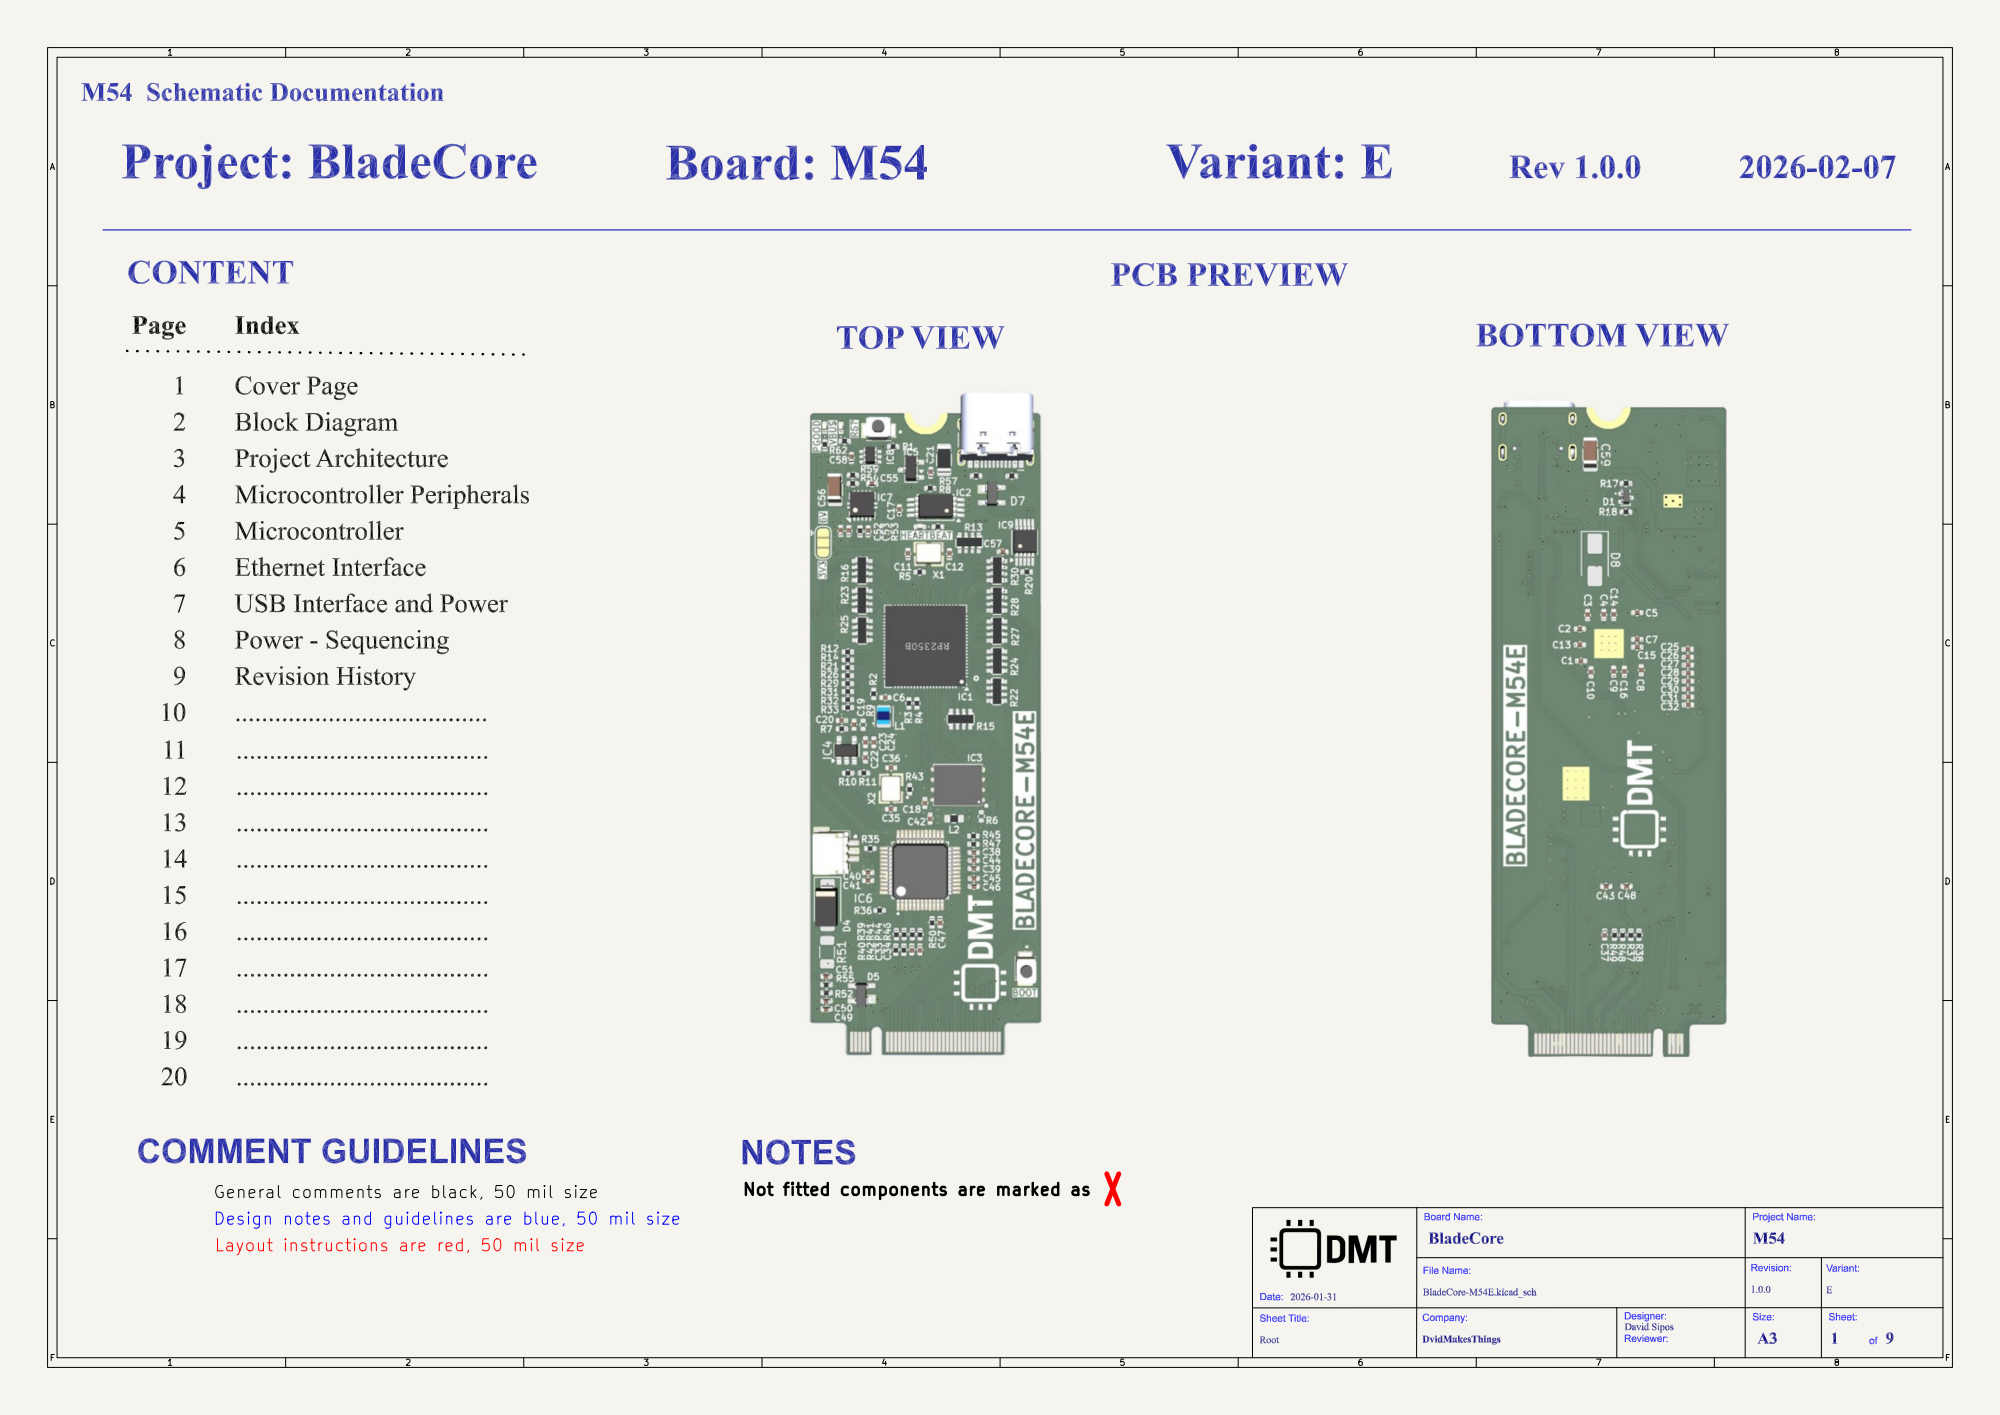
[picture p88: page 1]

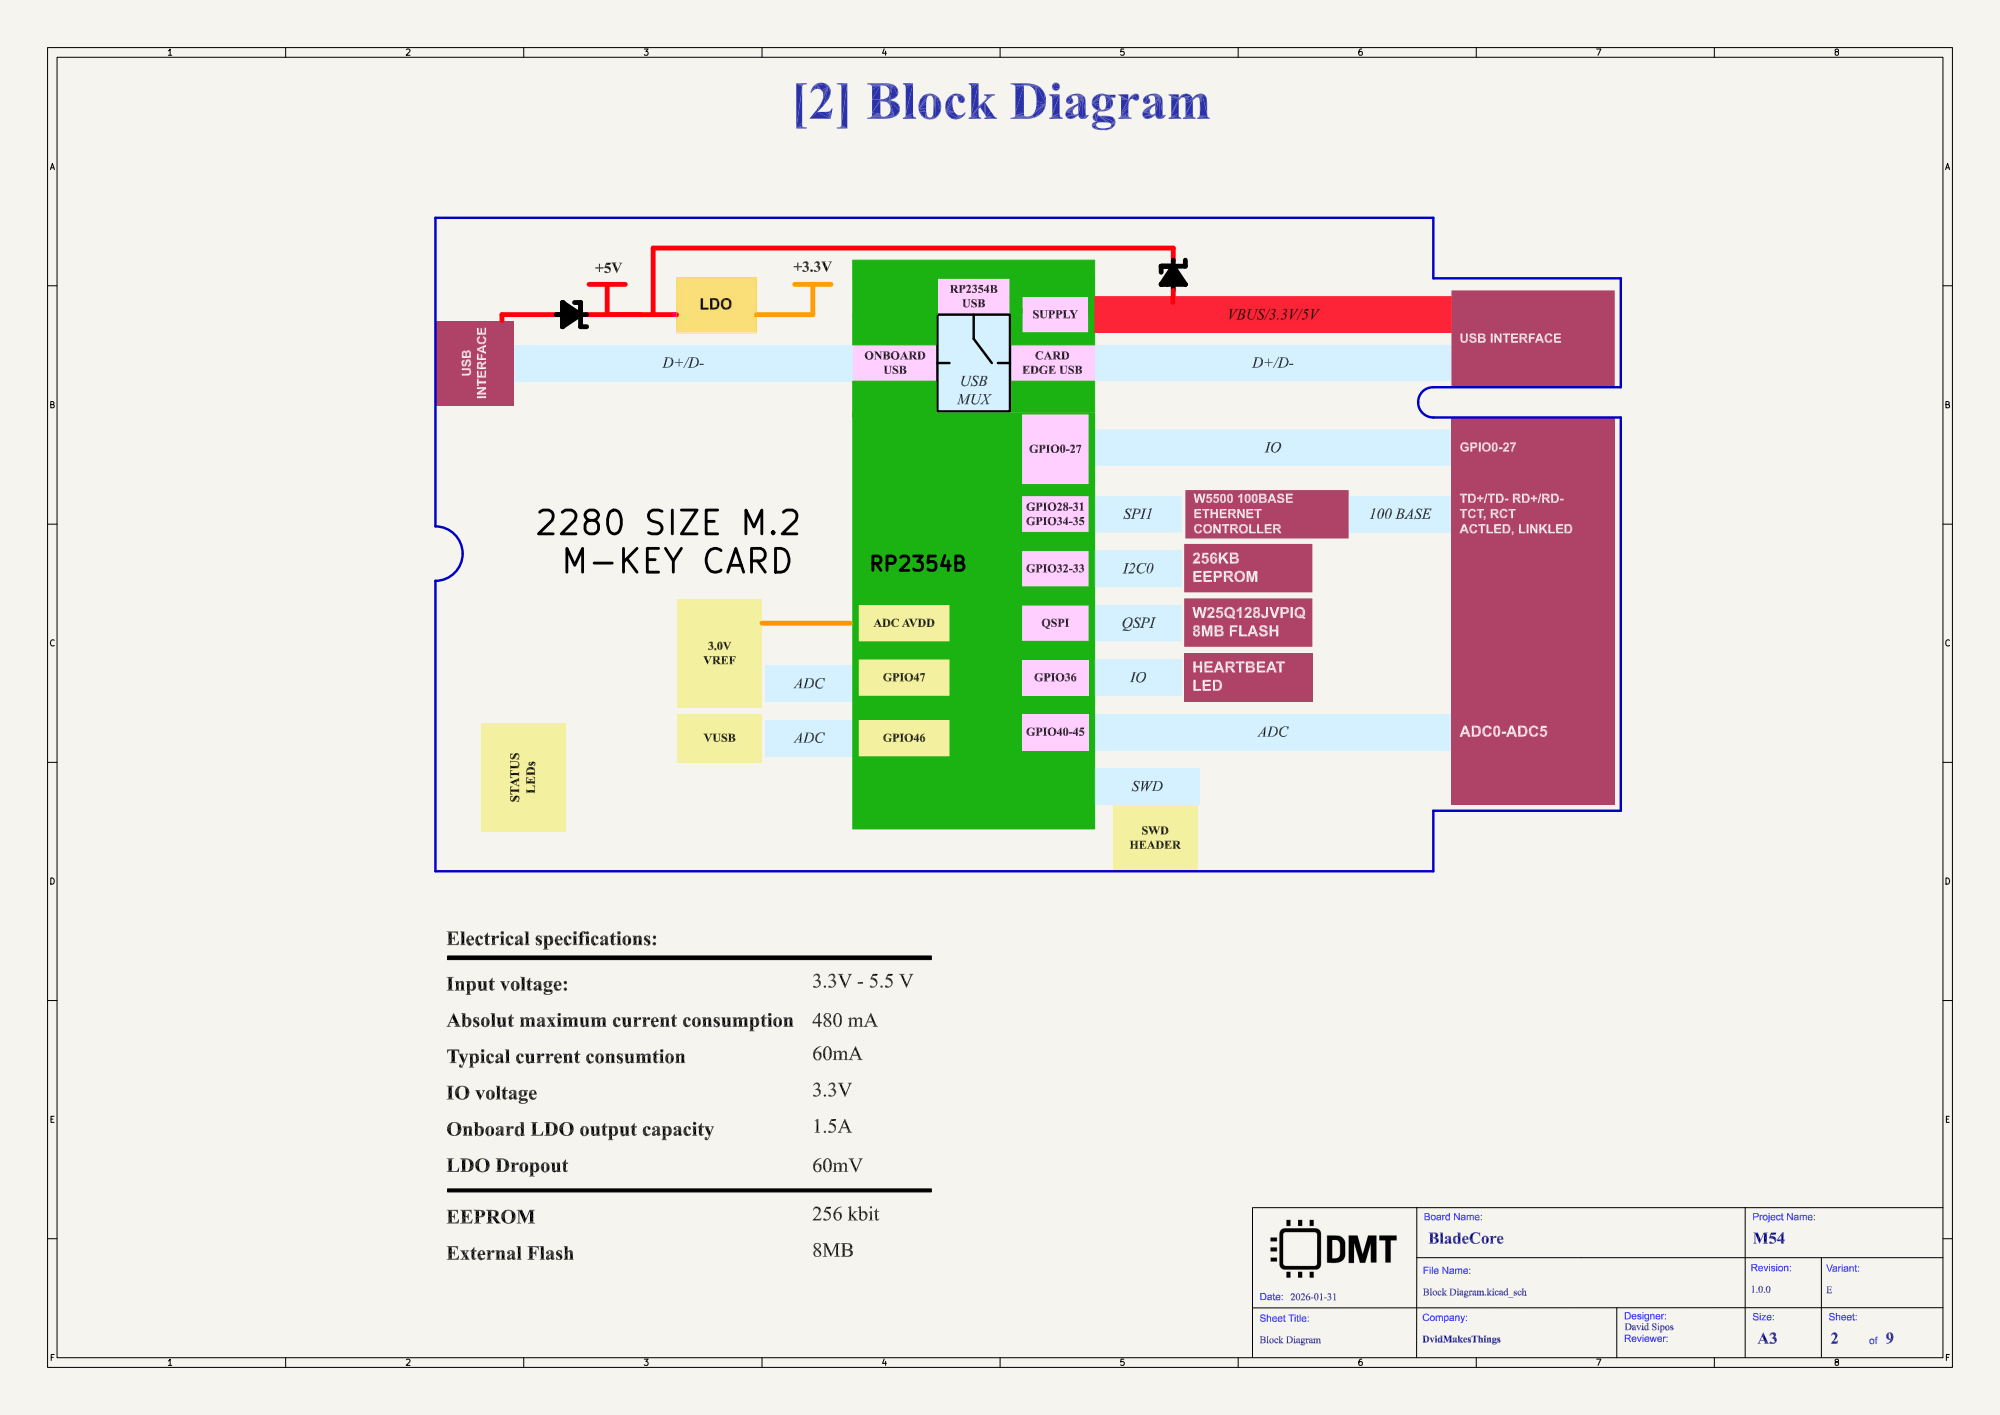
[picture p89: page 2]

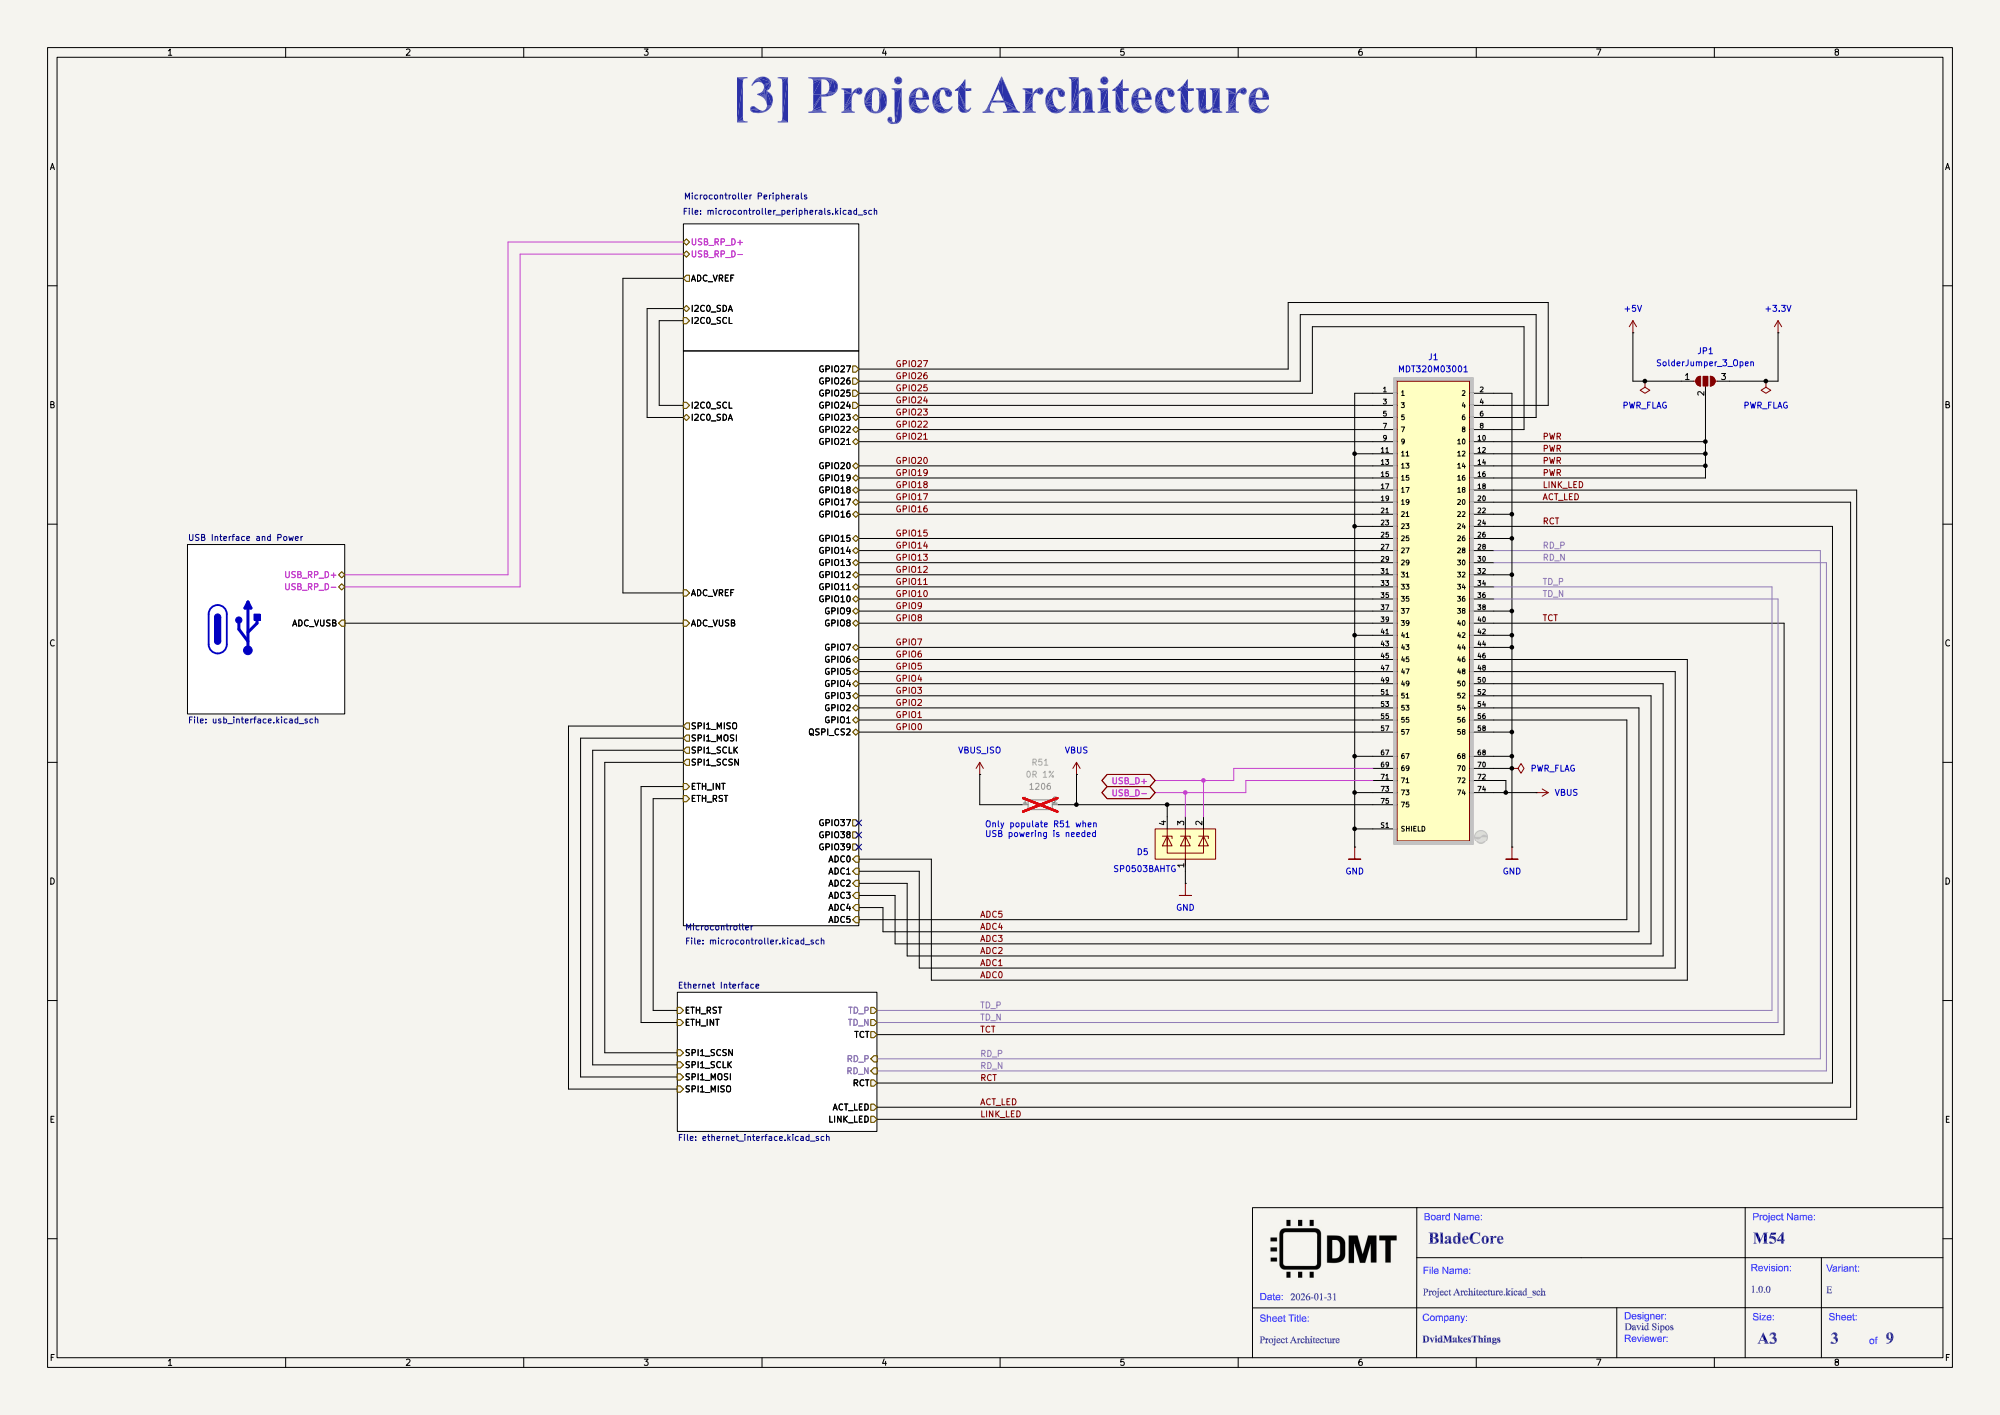
[picture p90: page 3]

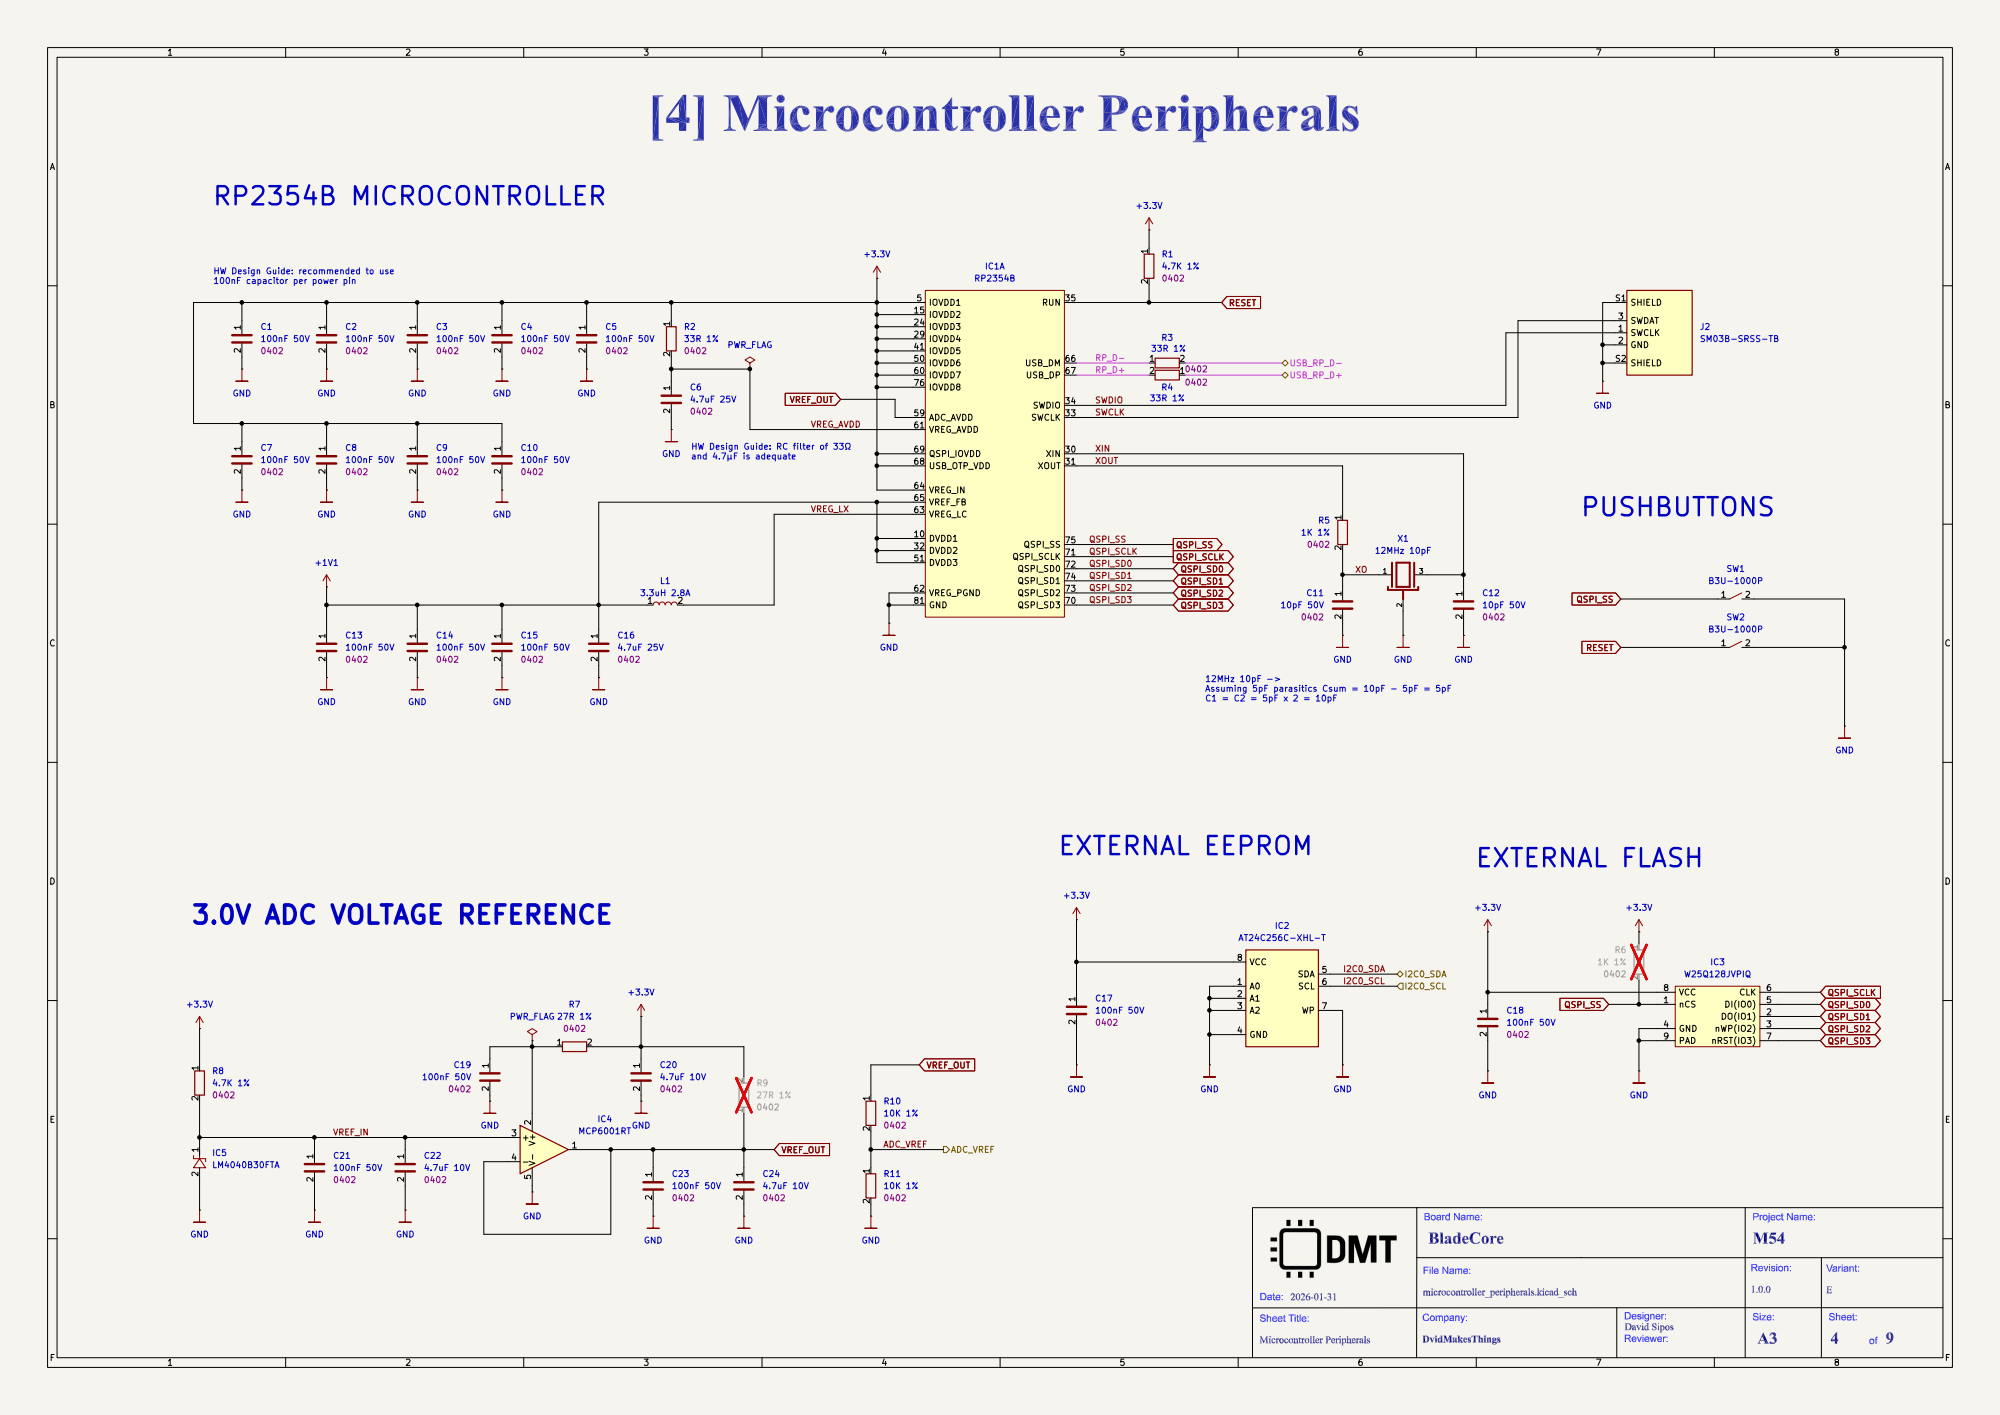
[picture p91: page 4]

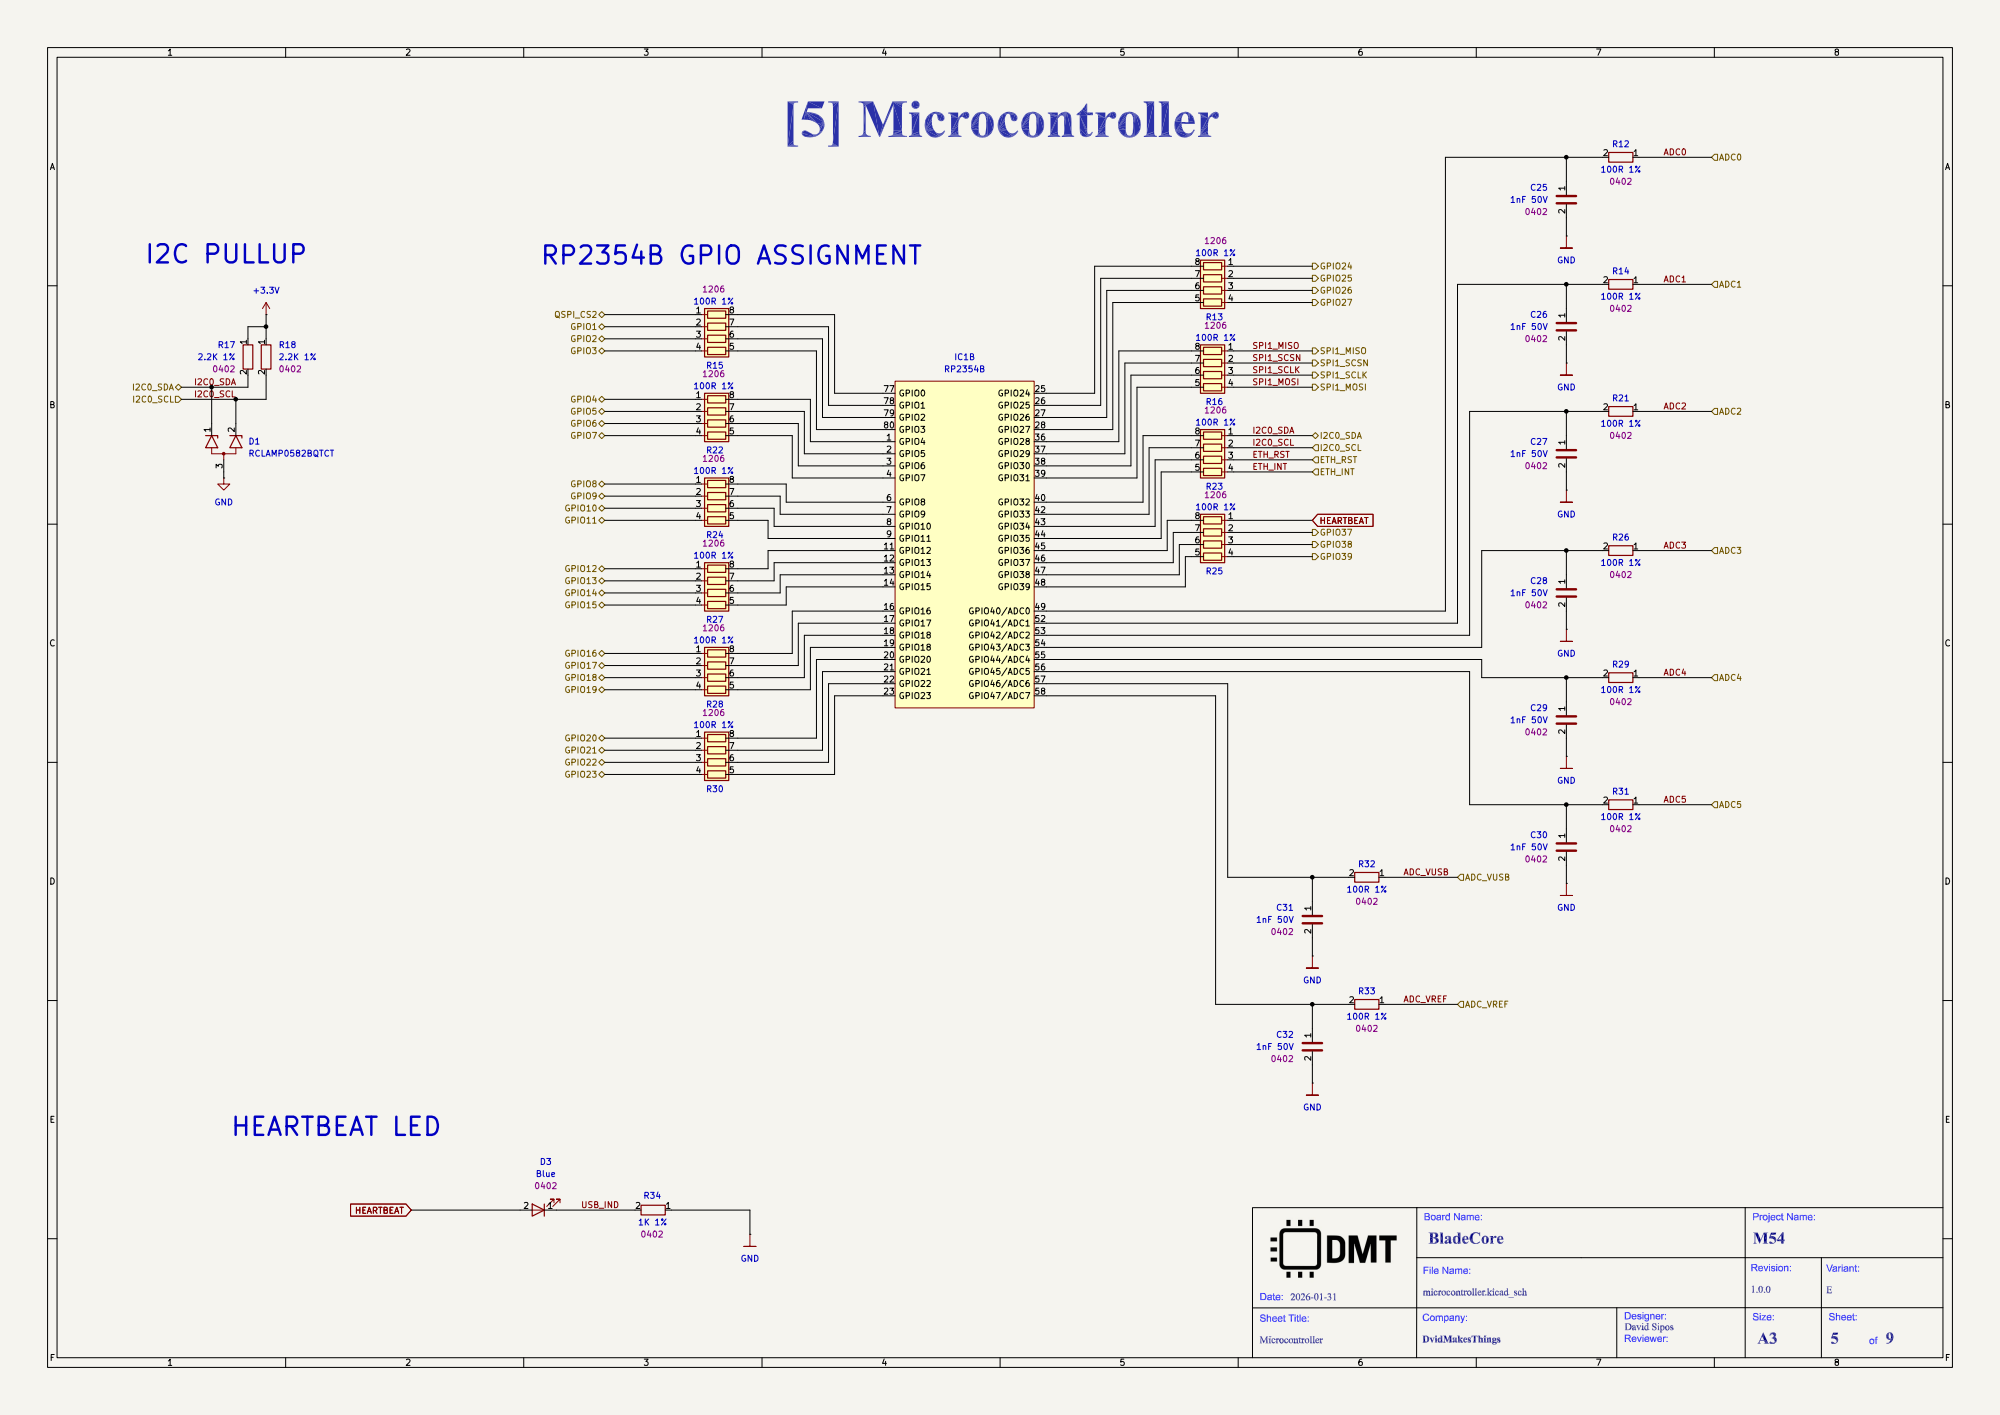
[picture p92: page 5]

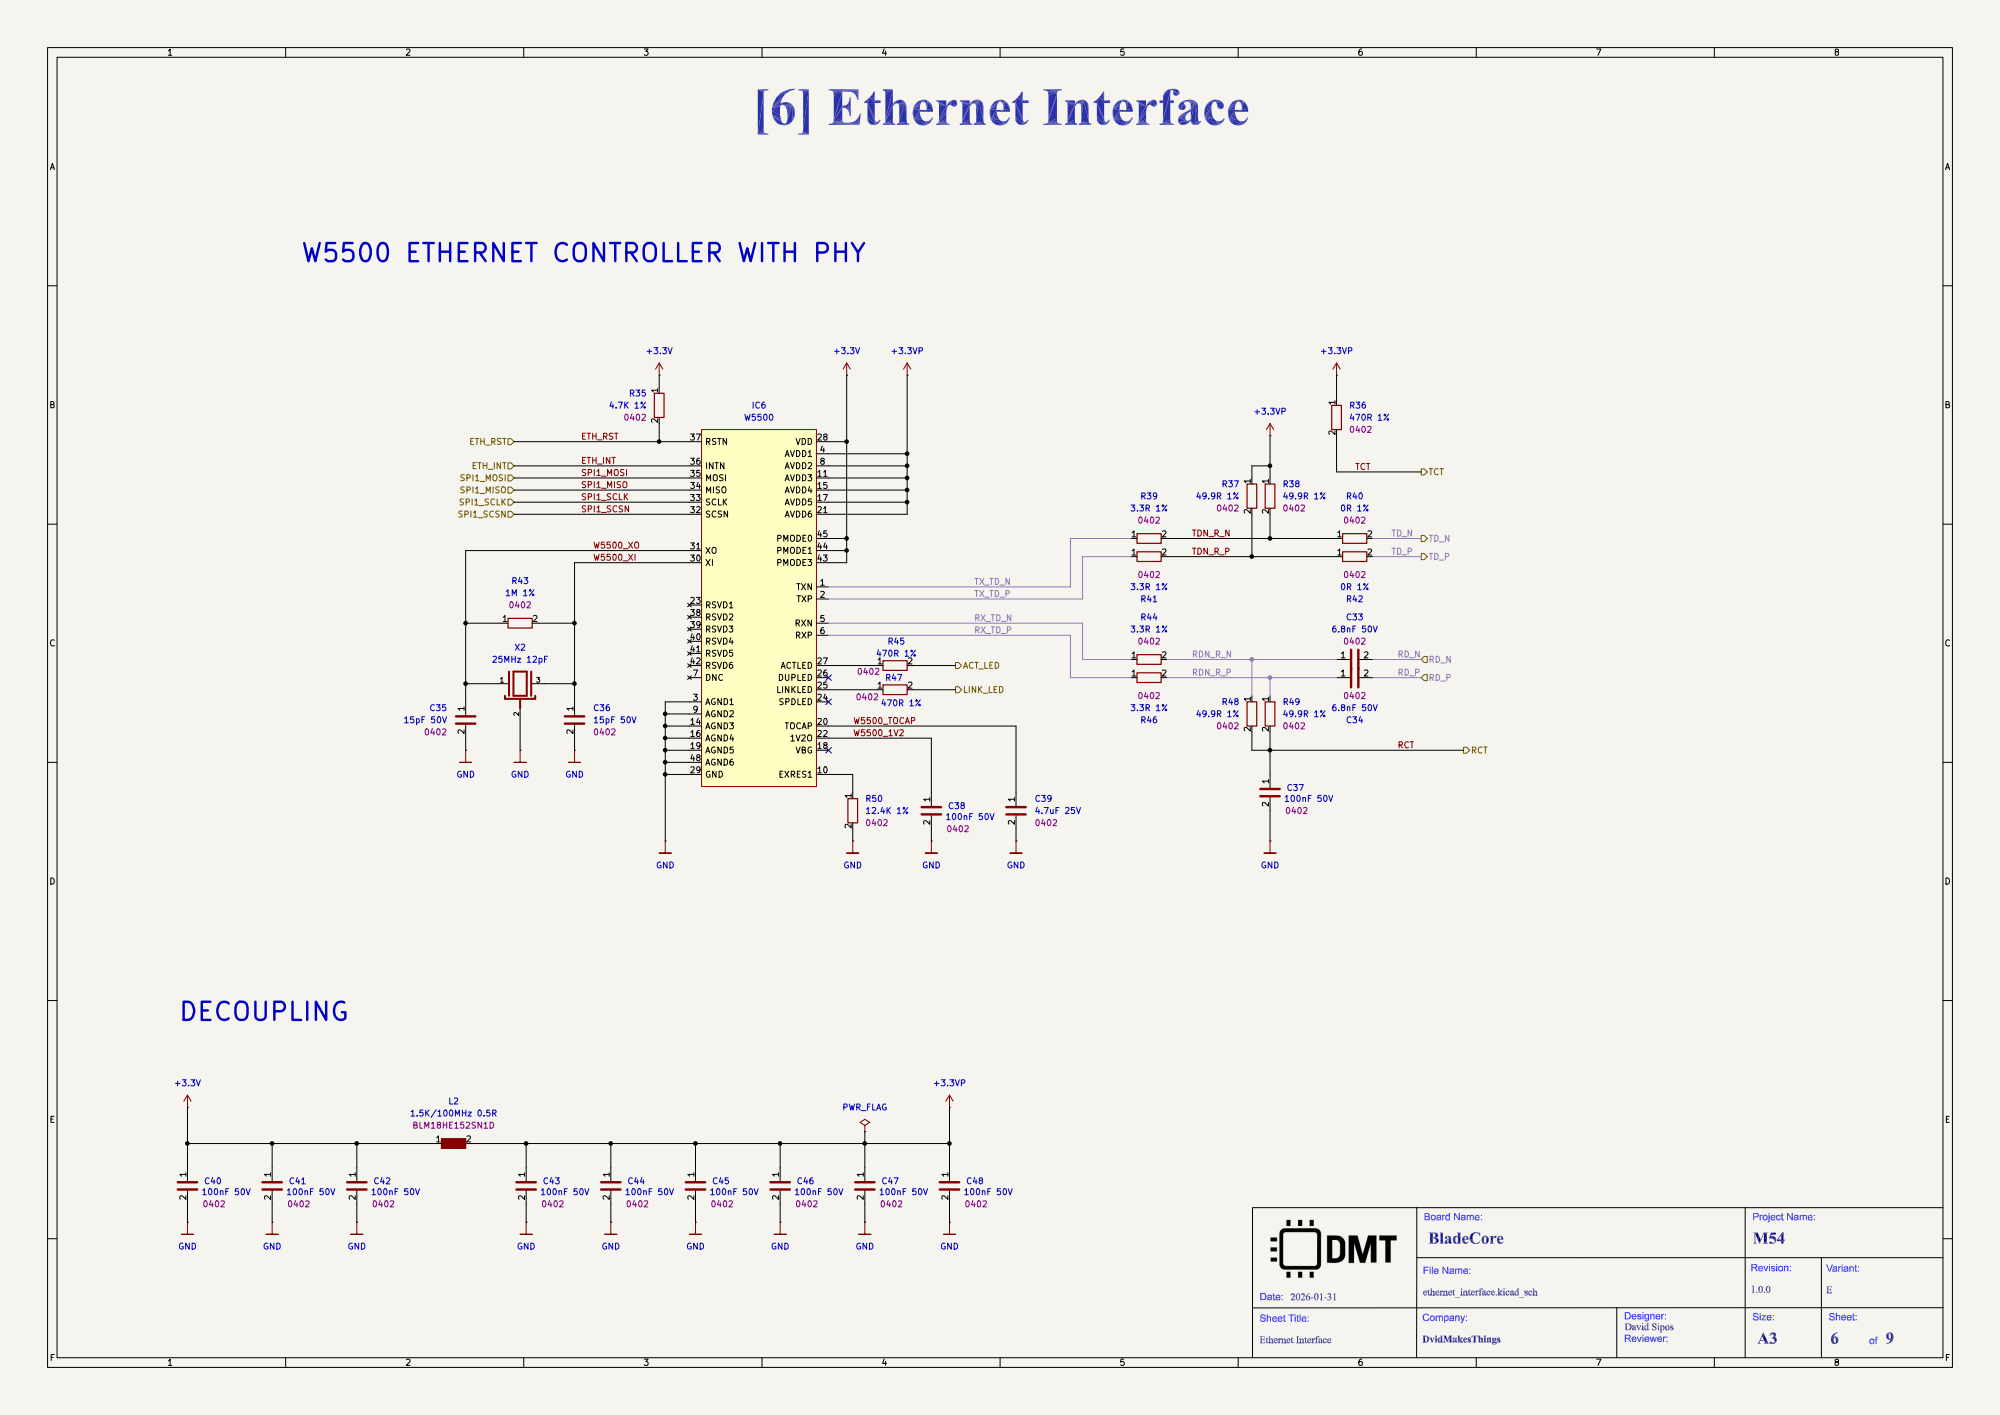
[picture p93: page 6]

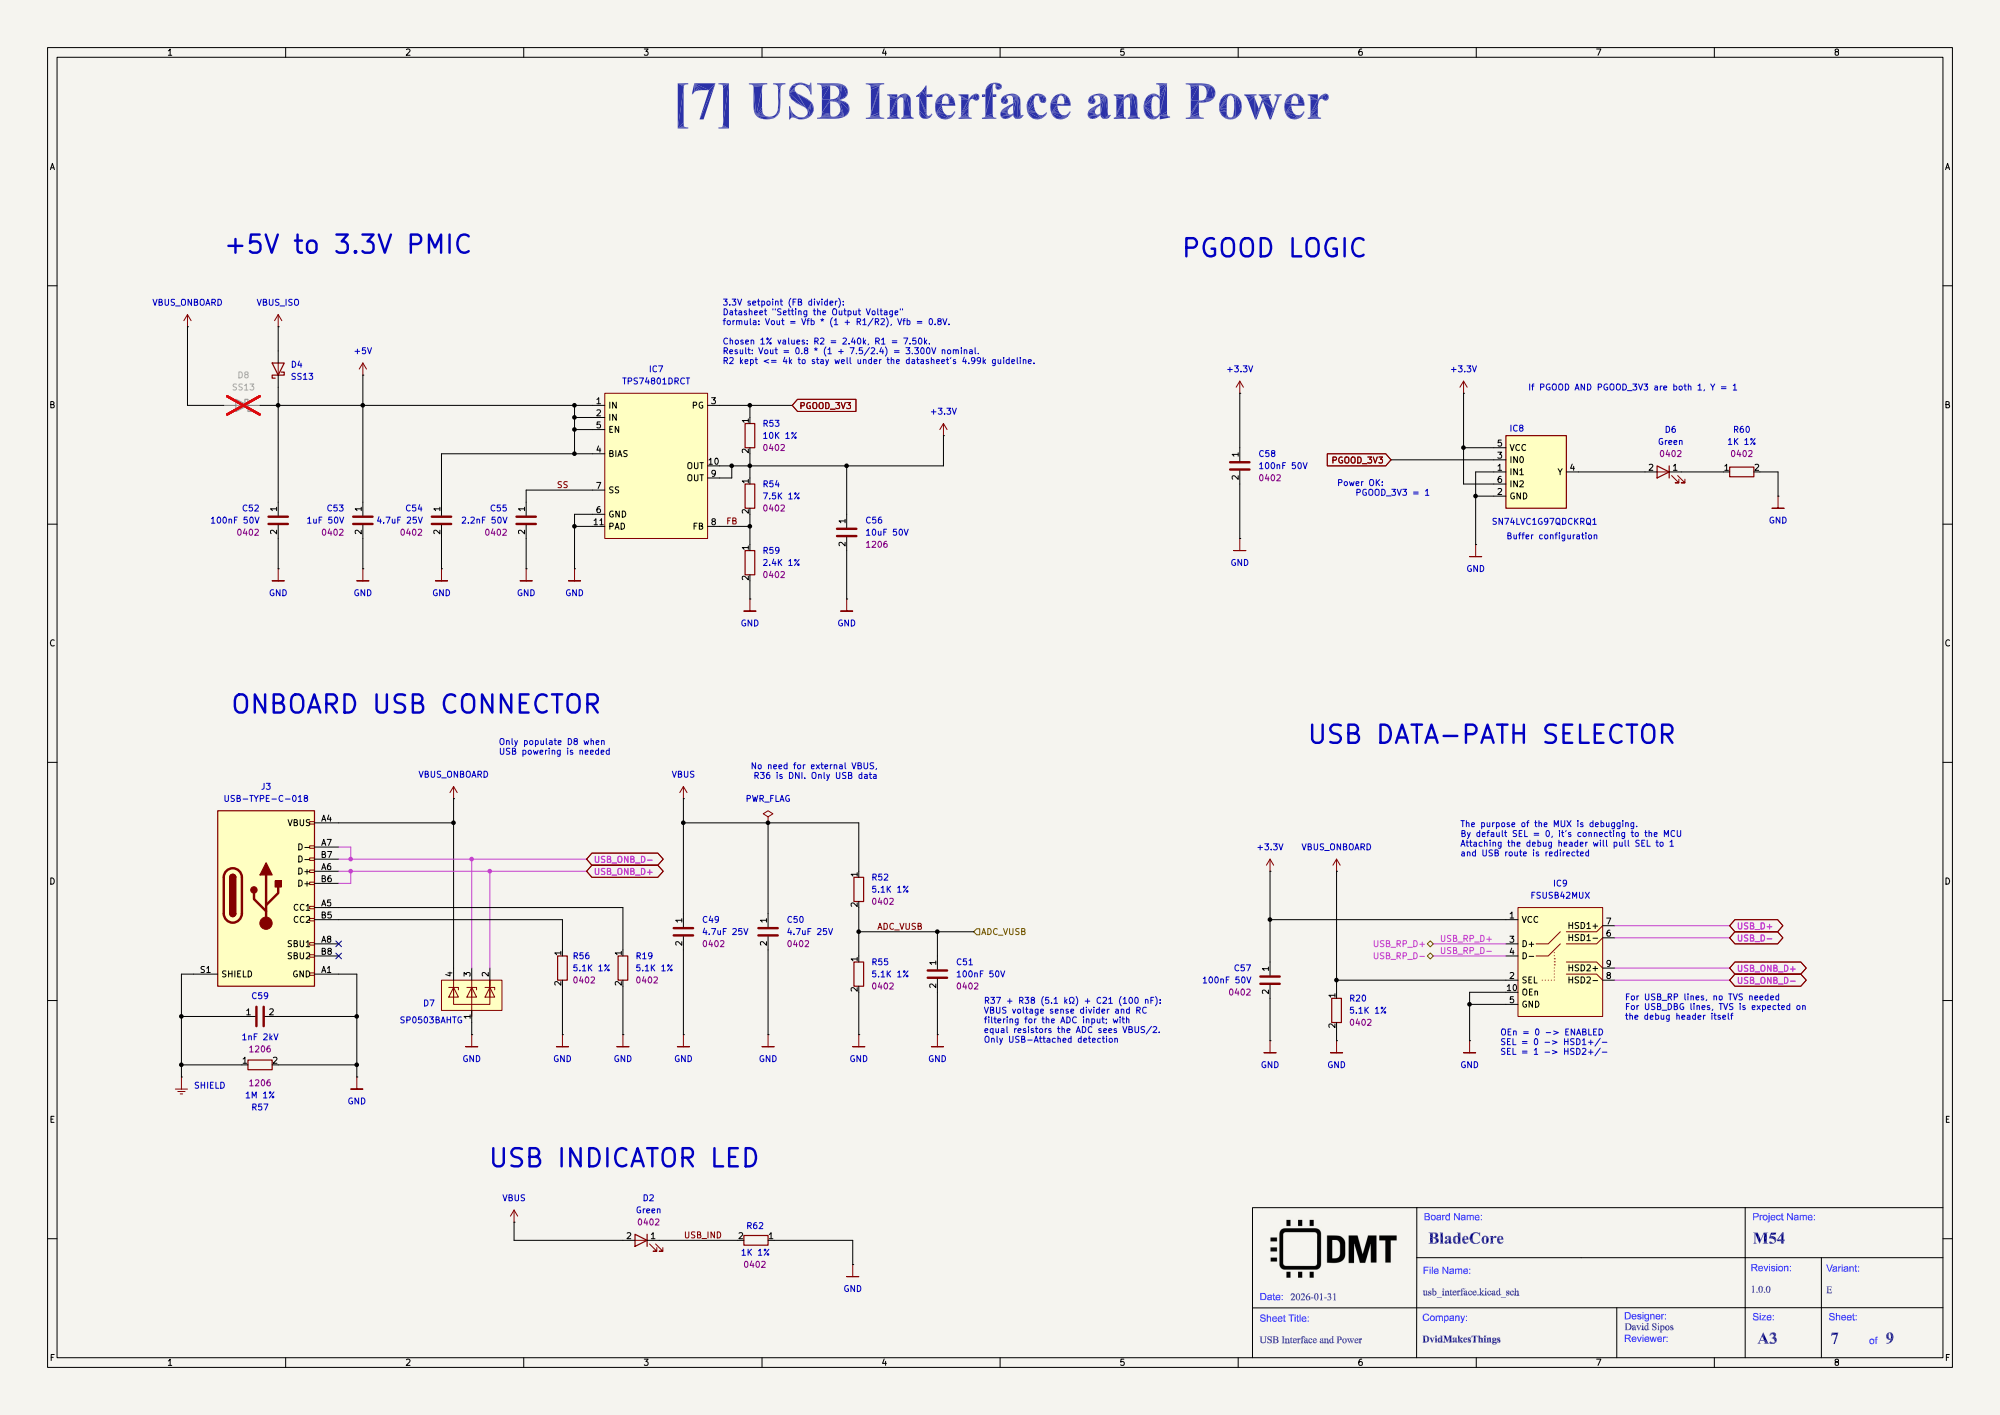
[picture p94: page 7]

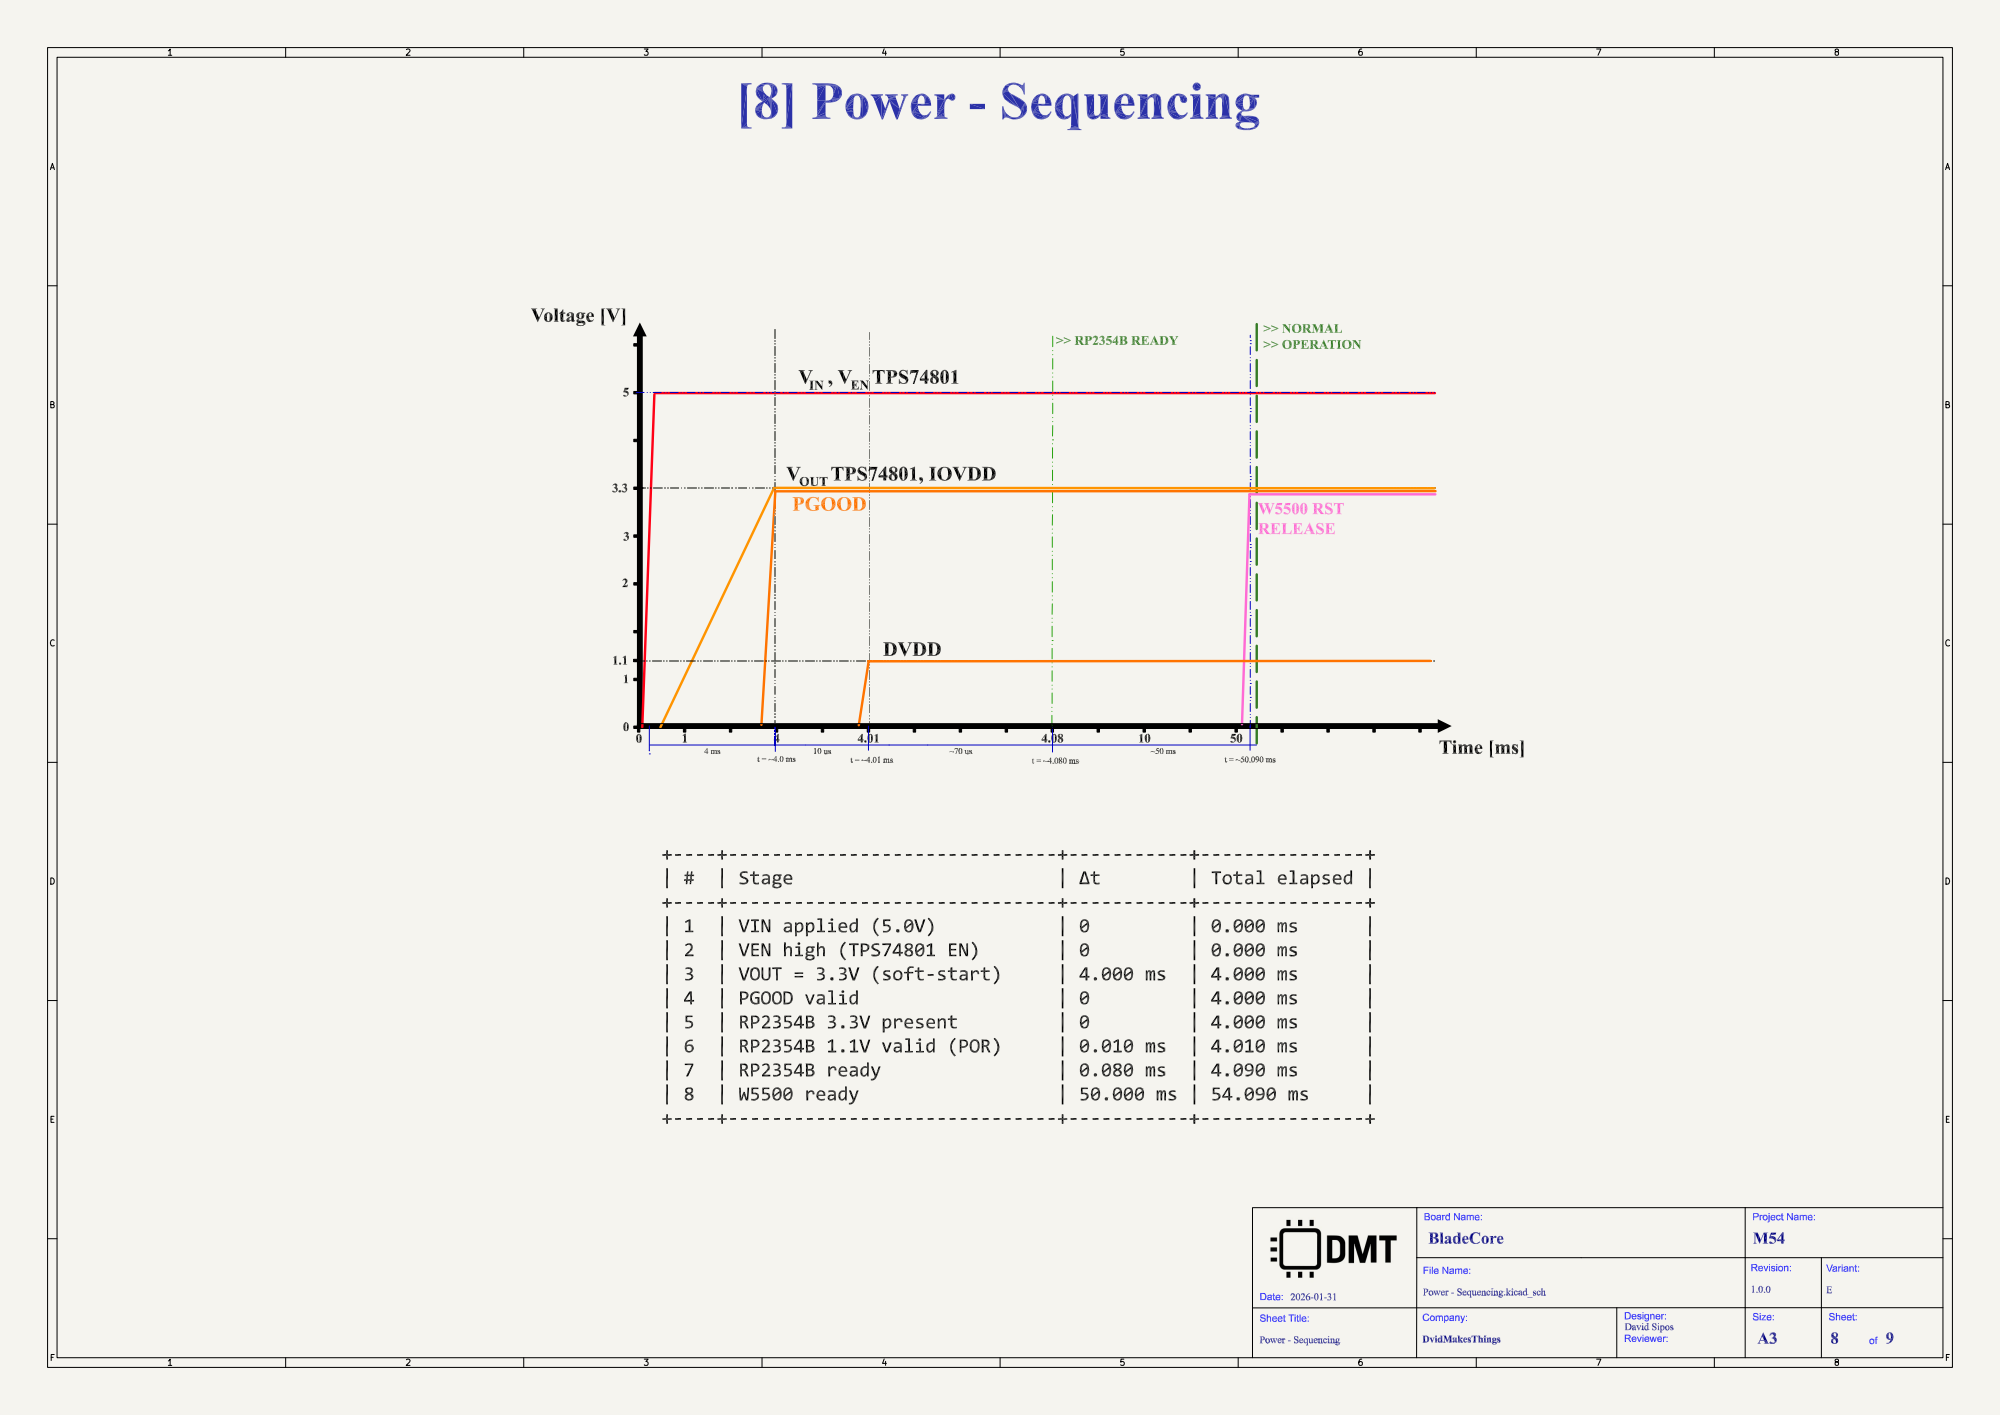
[picture p95: page 8]

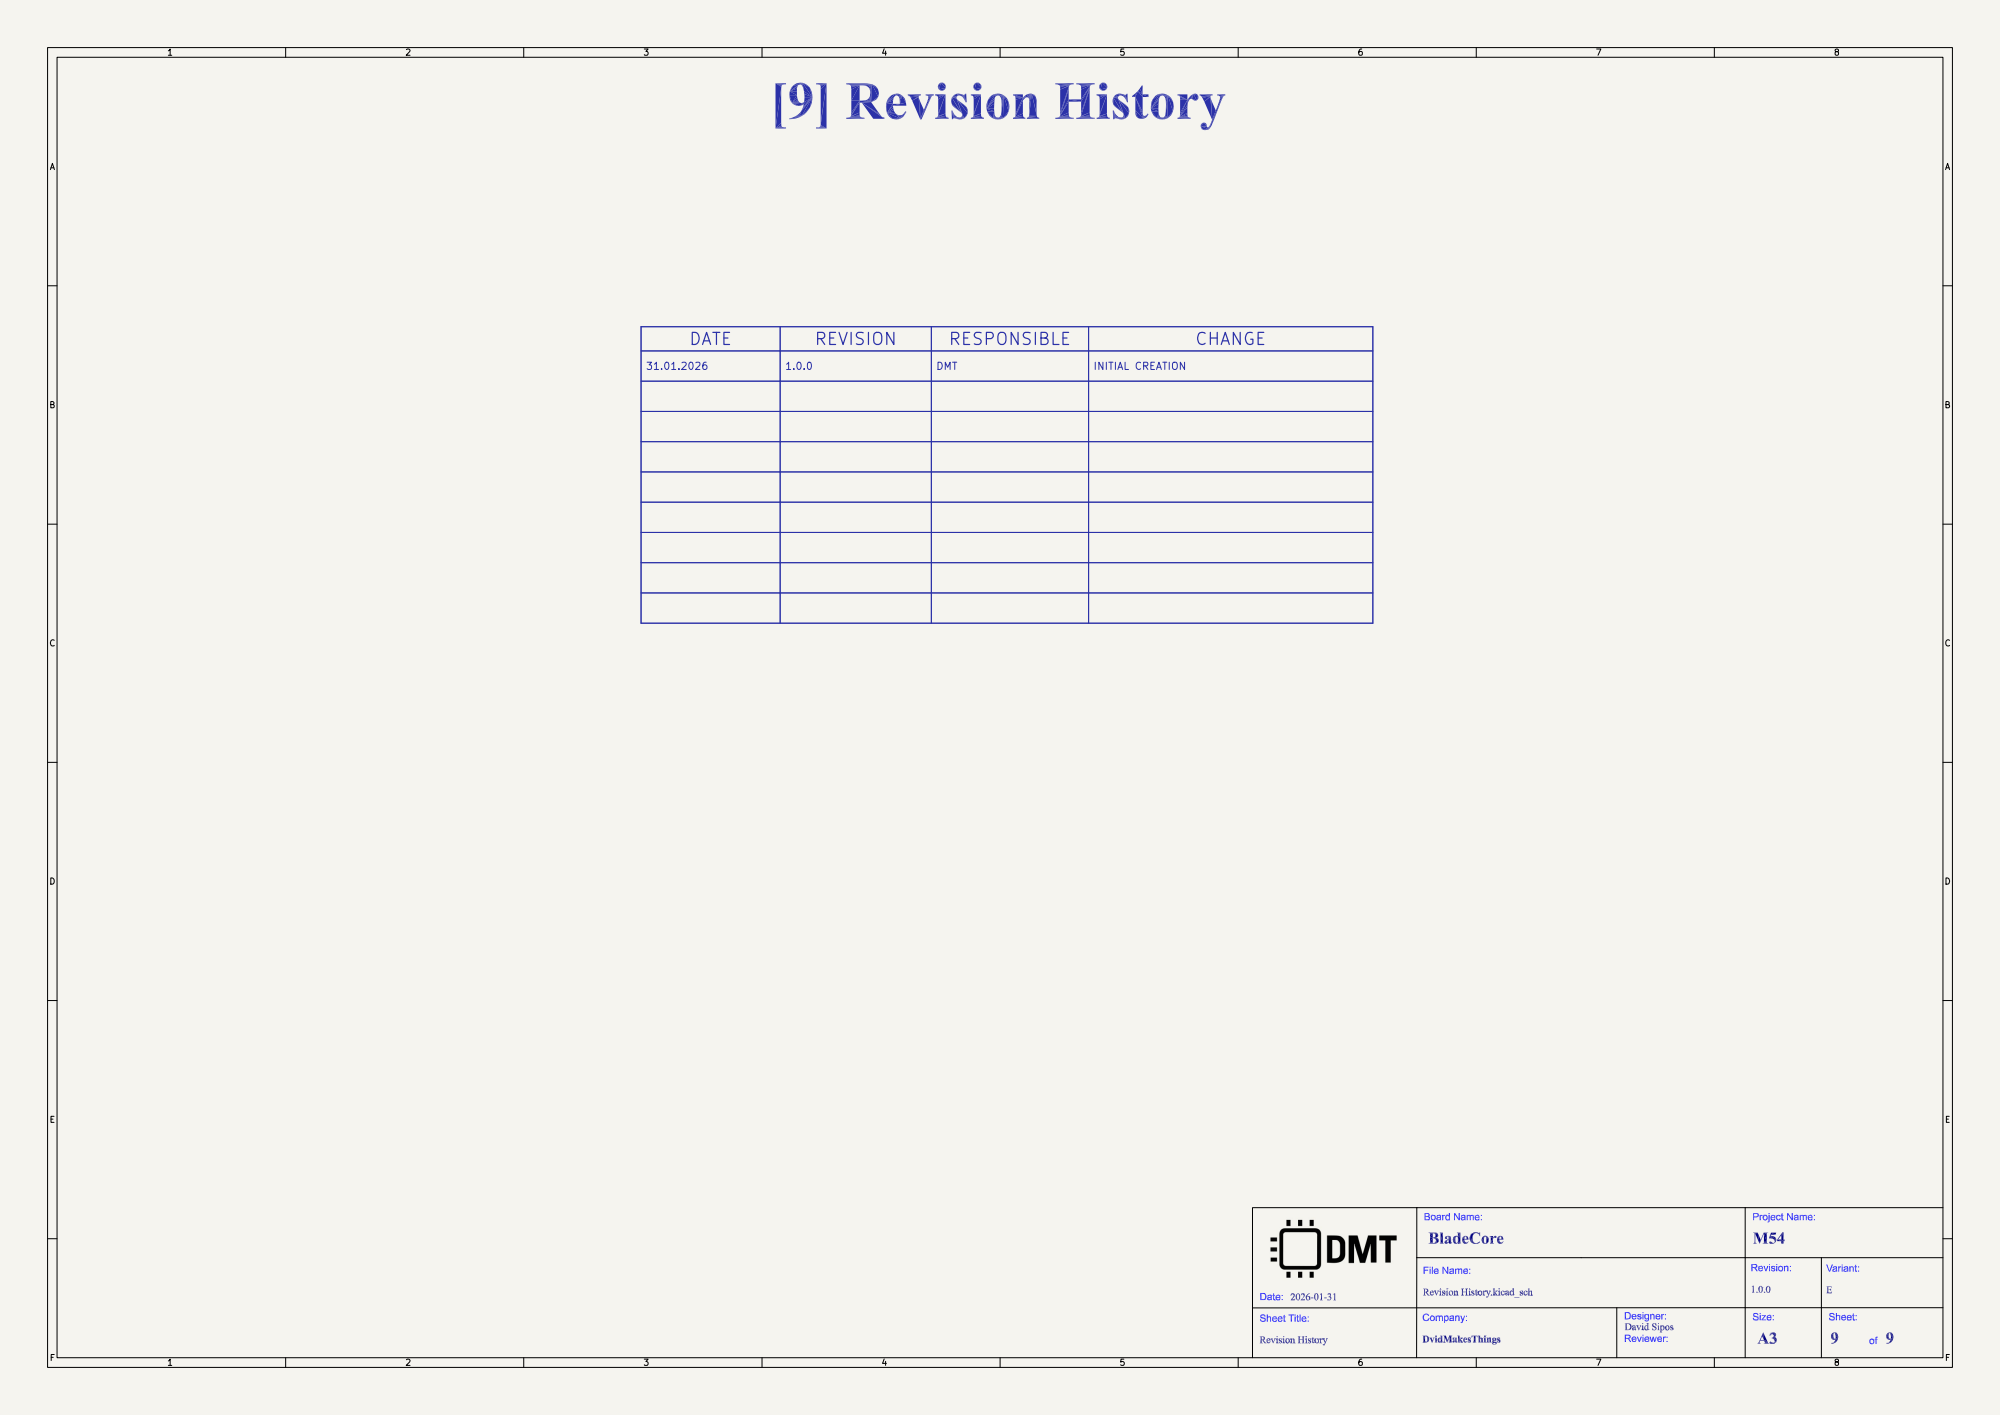
[picture p96: page 9]
