DvidMakesThings/HW_PDNode-600-Pro/src/PDF/SCH_PDCard-5031_100.pdf

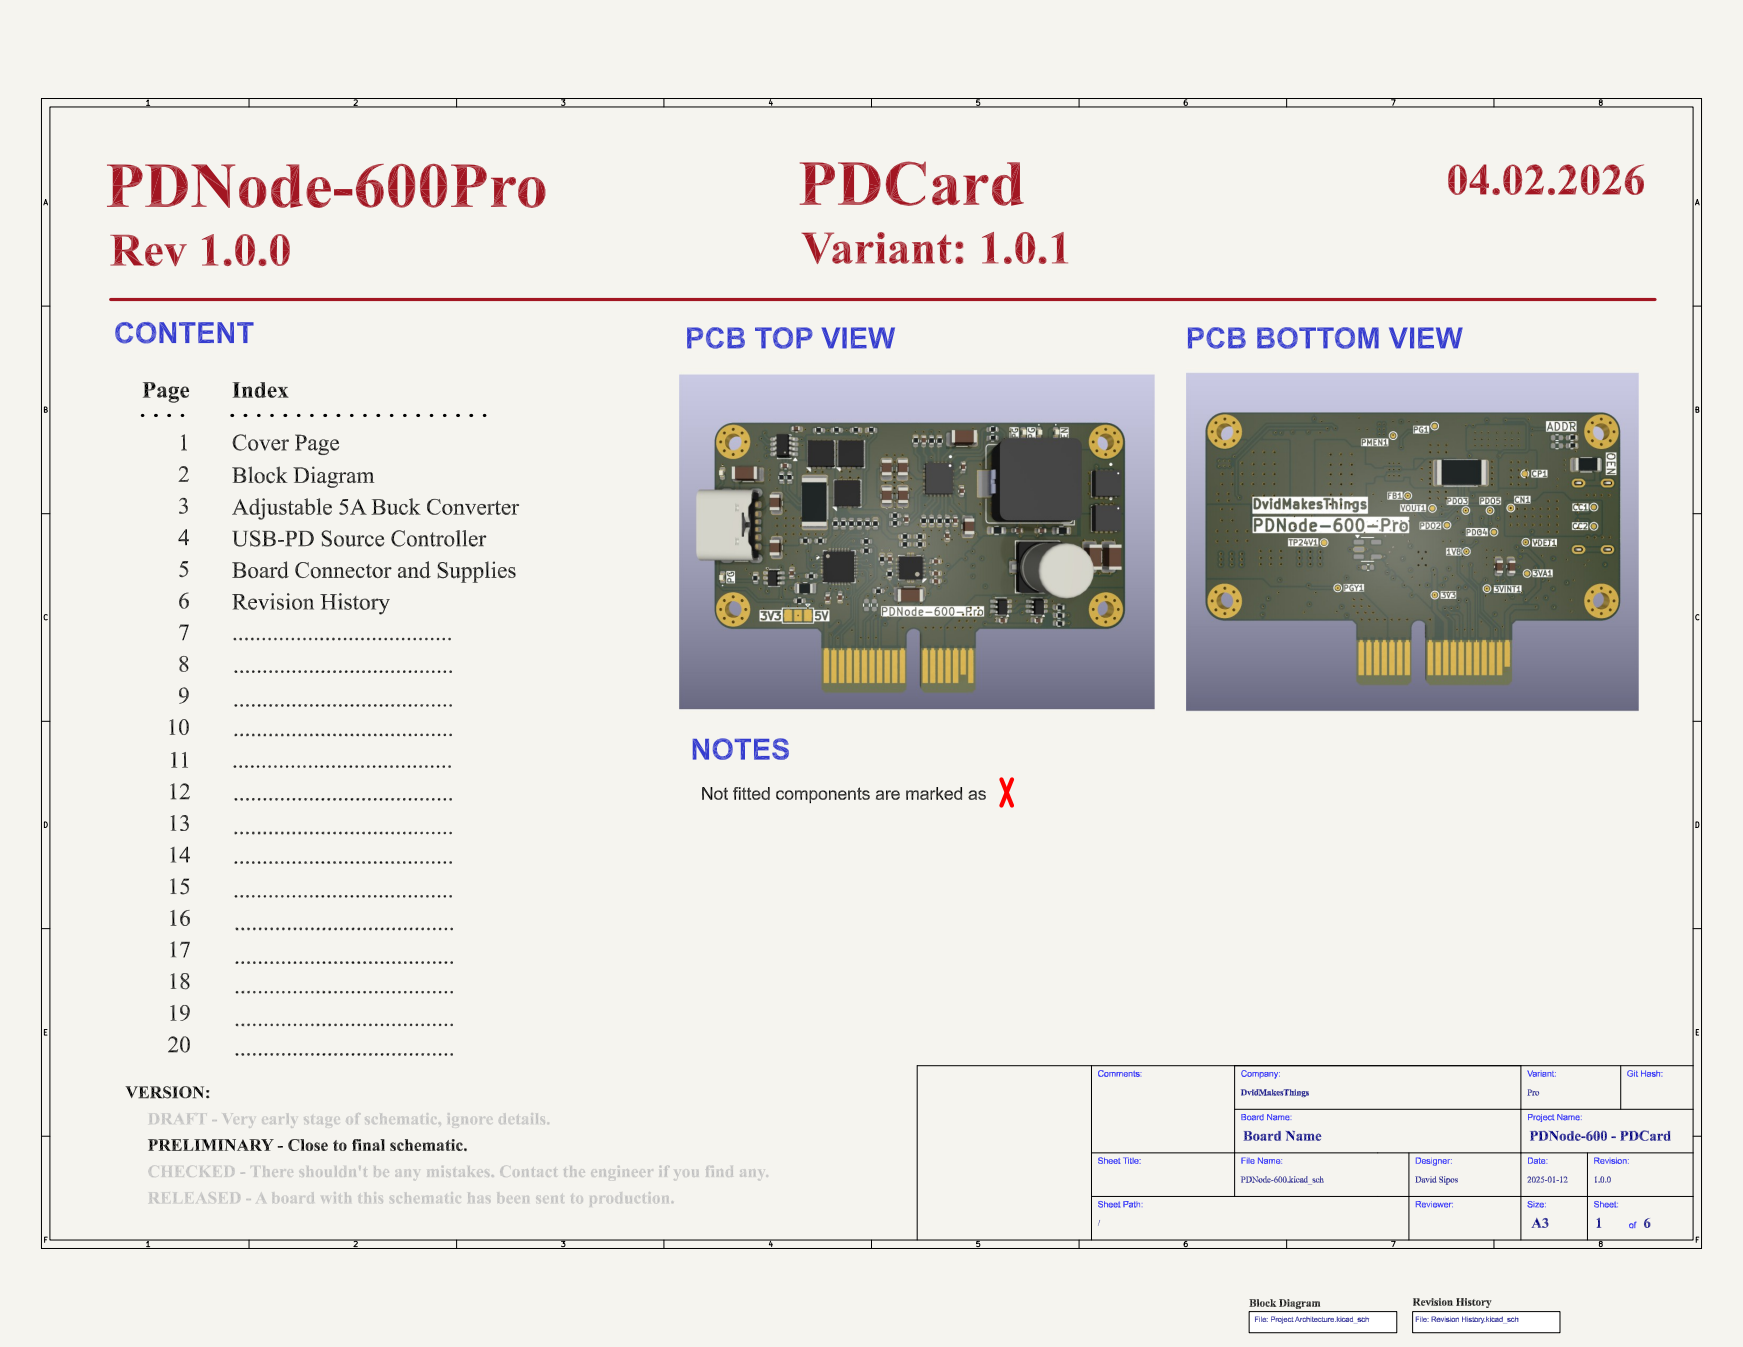
[picture p97: page 1]

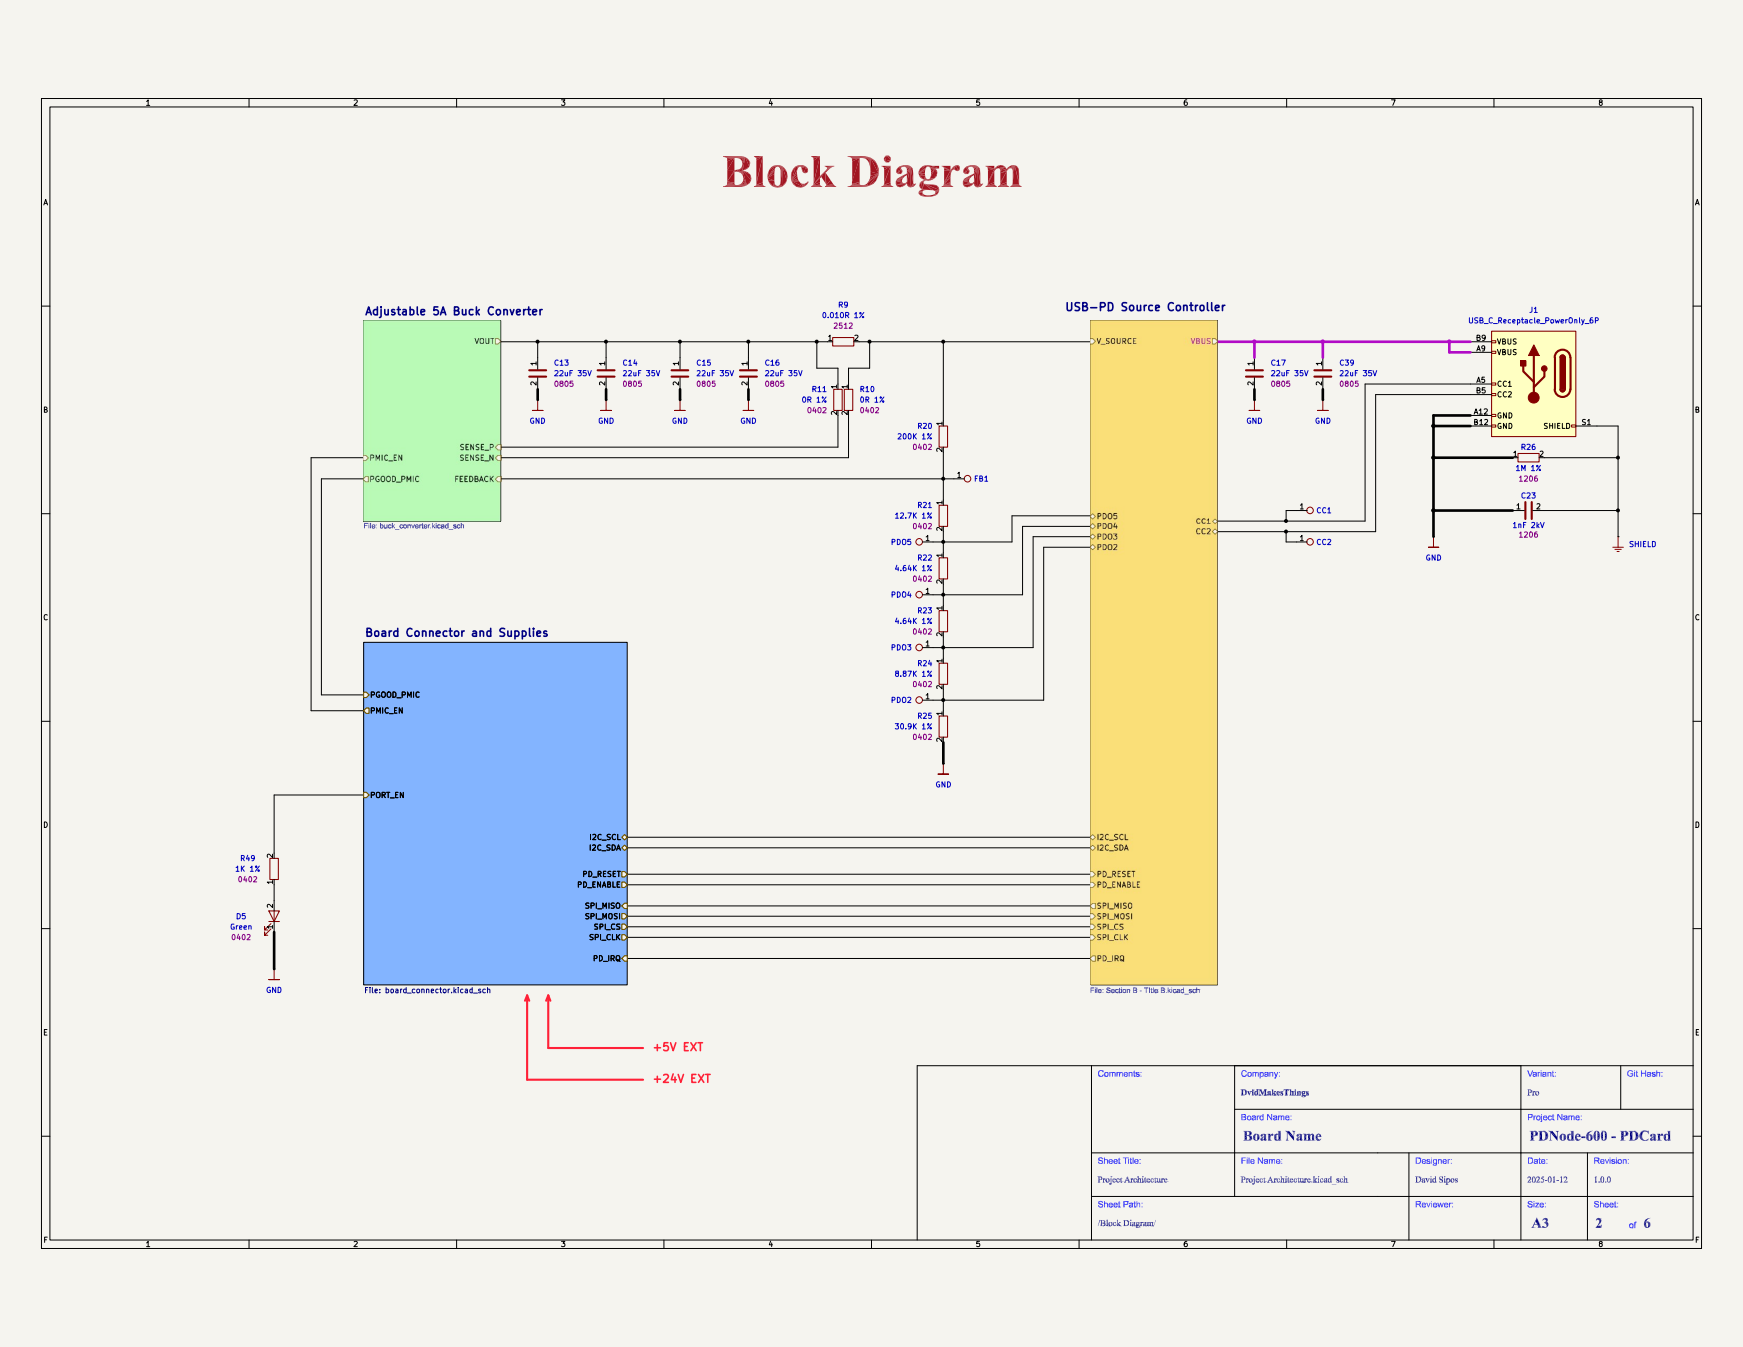
[picture p98: page 2]

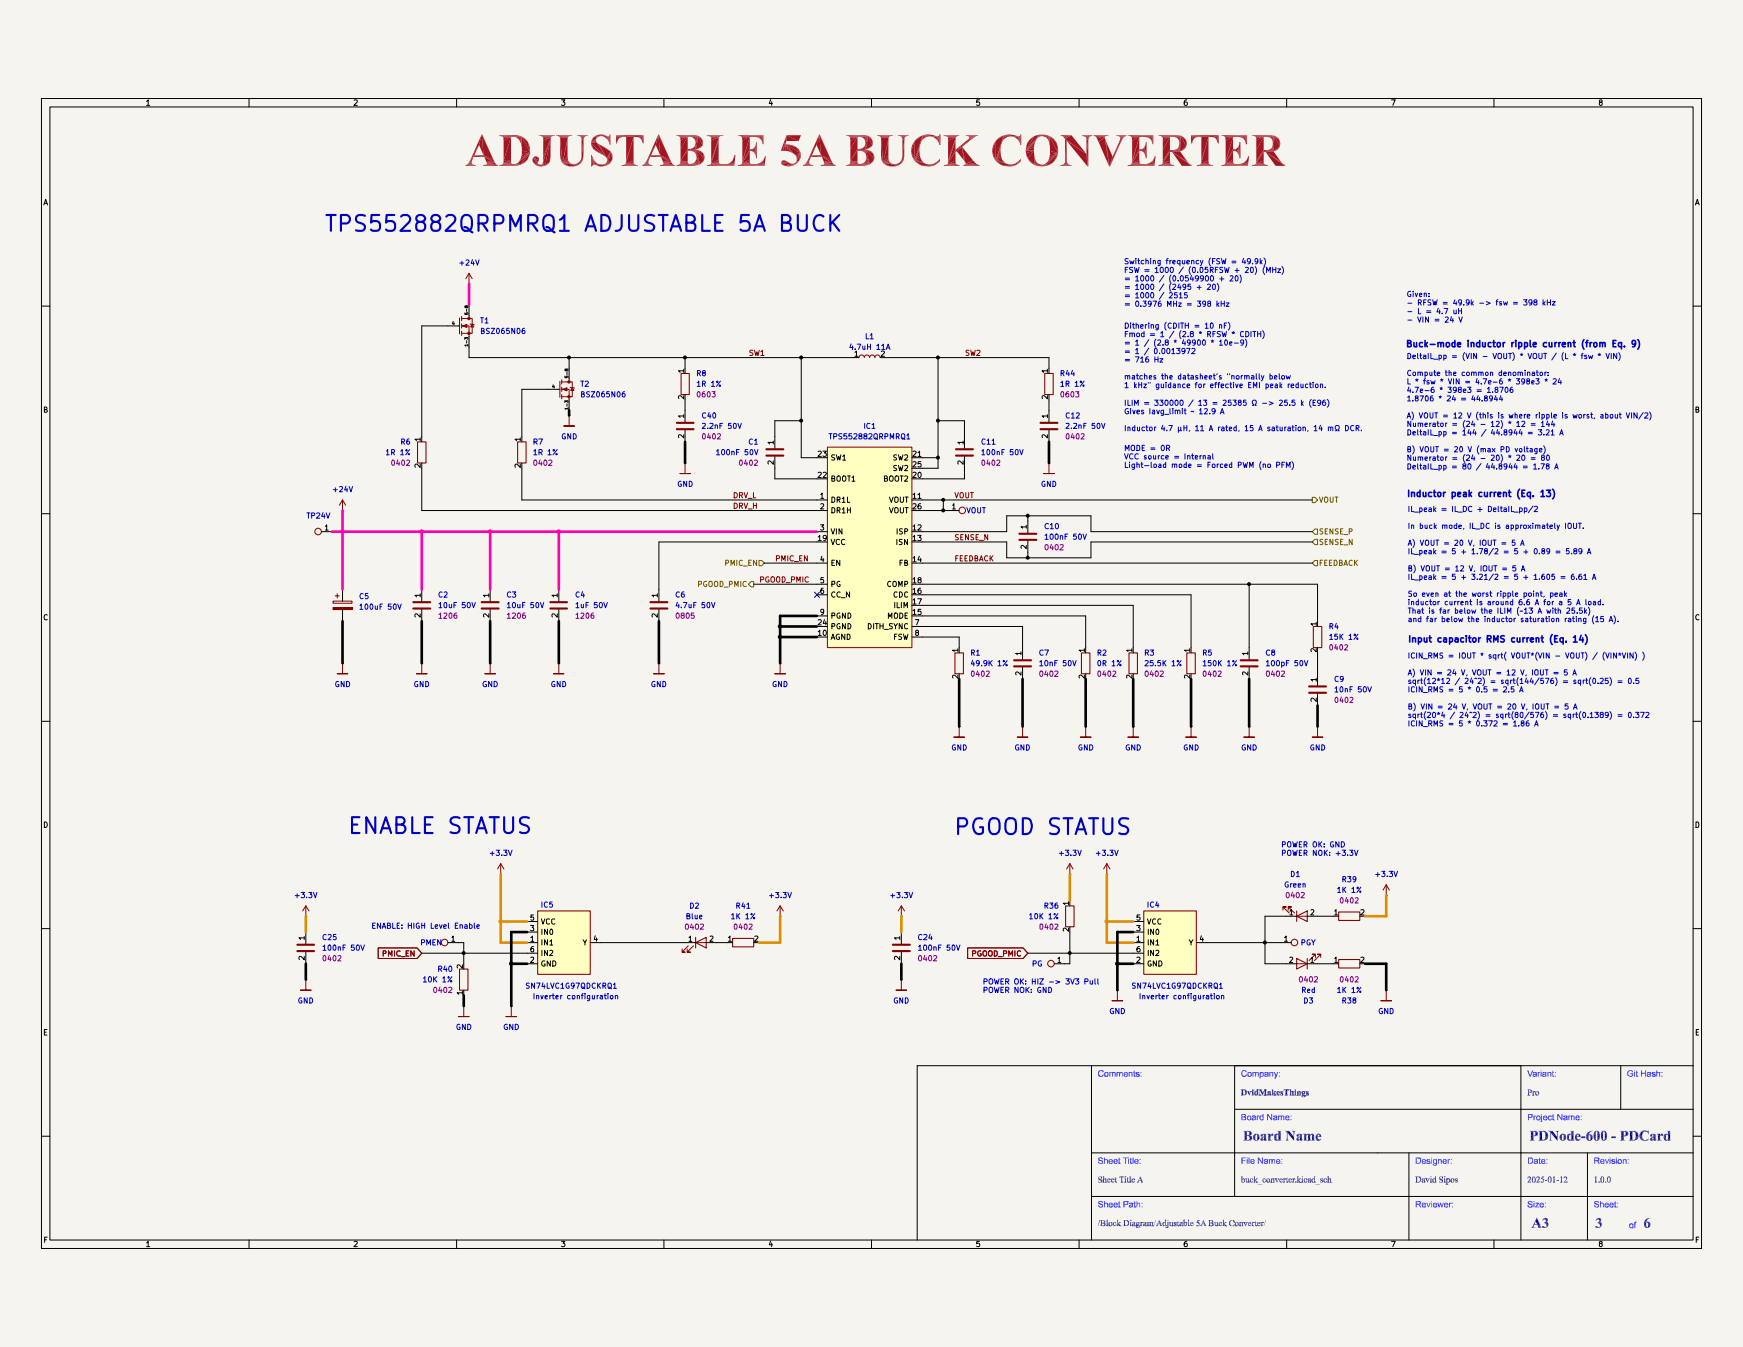
[picture p99: page 3]

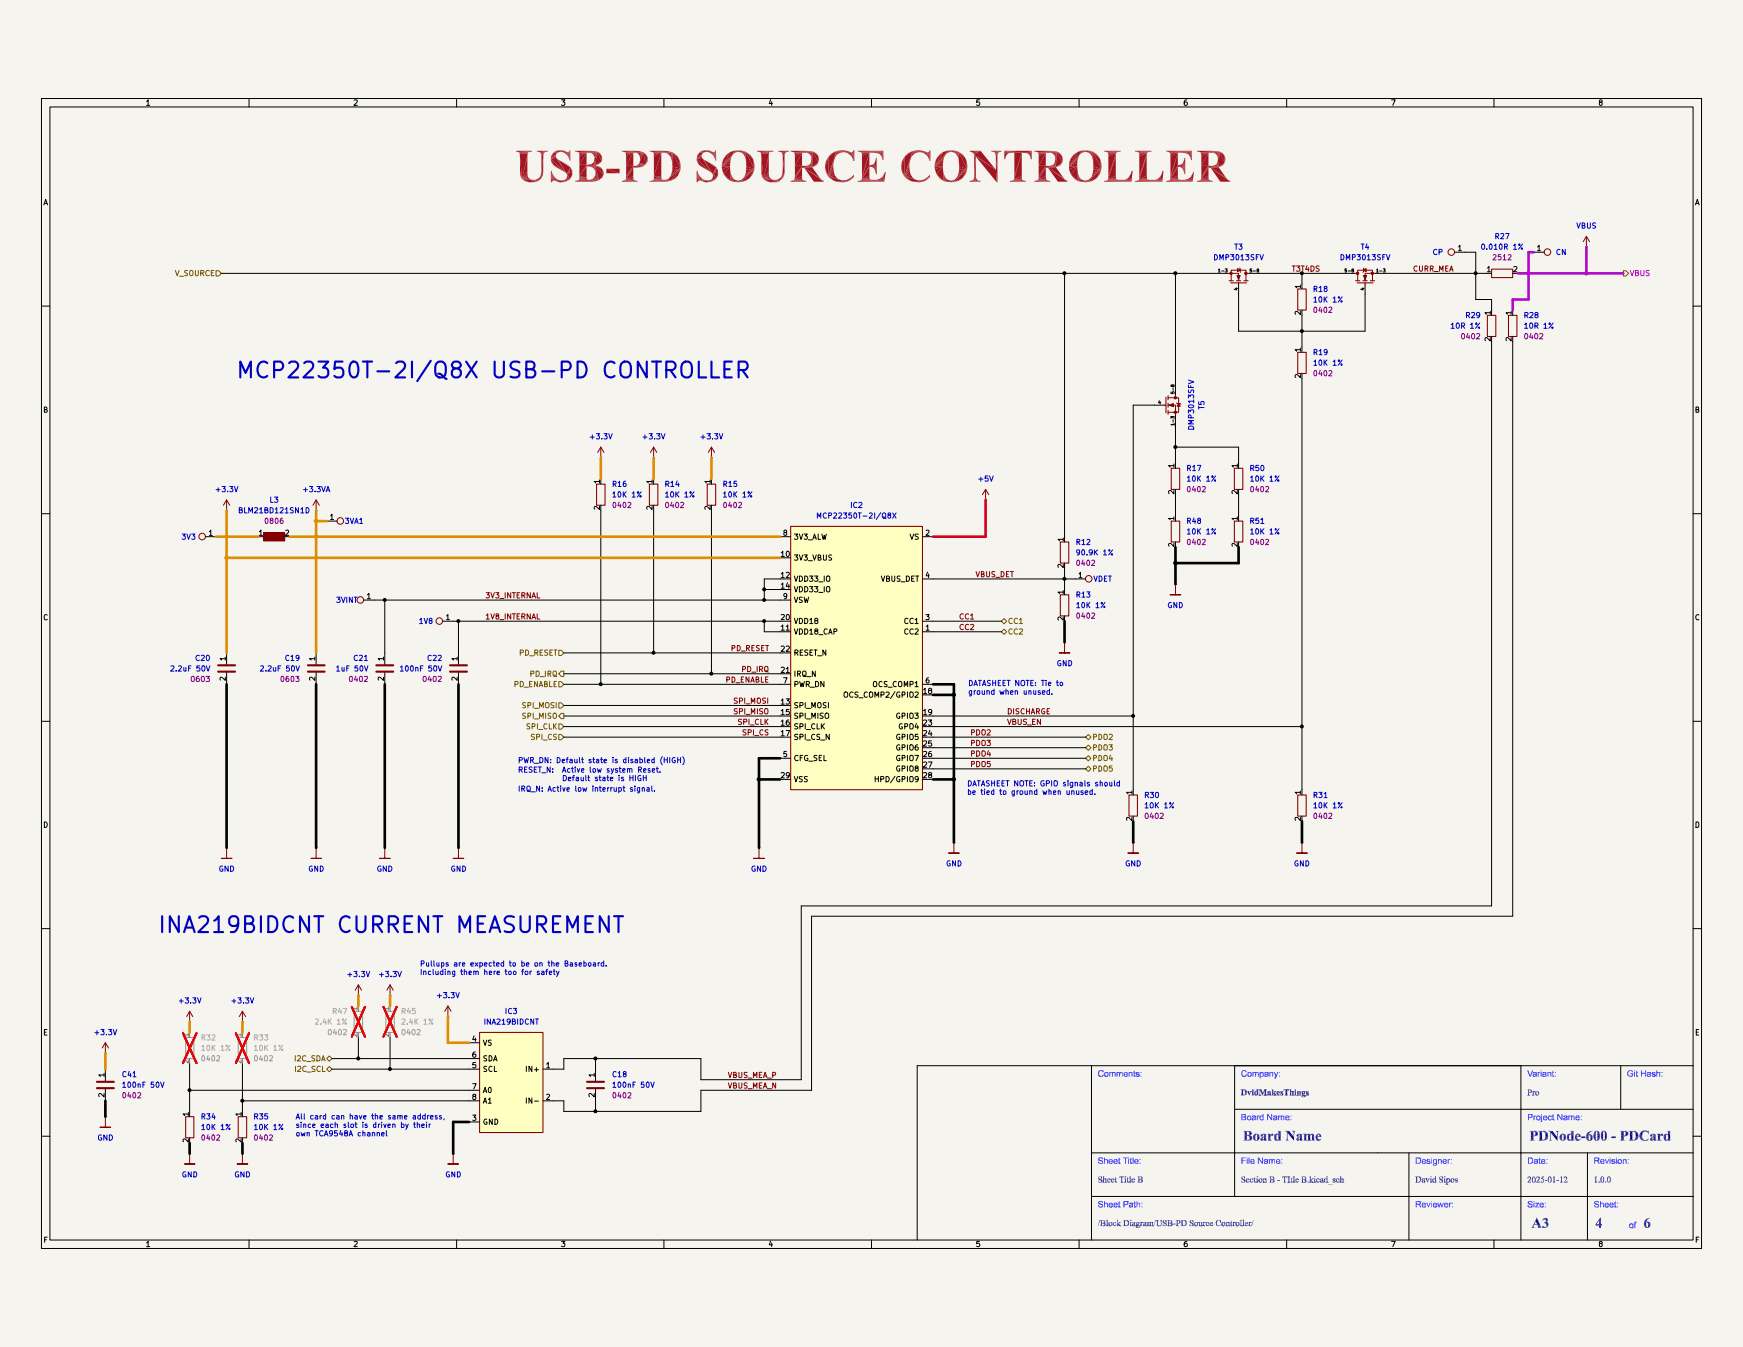
[picture p100: page 4]

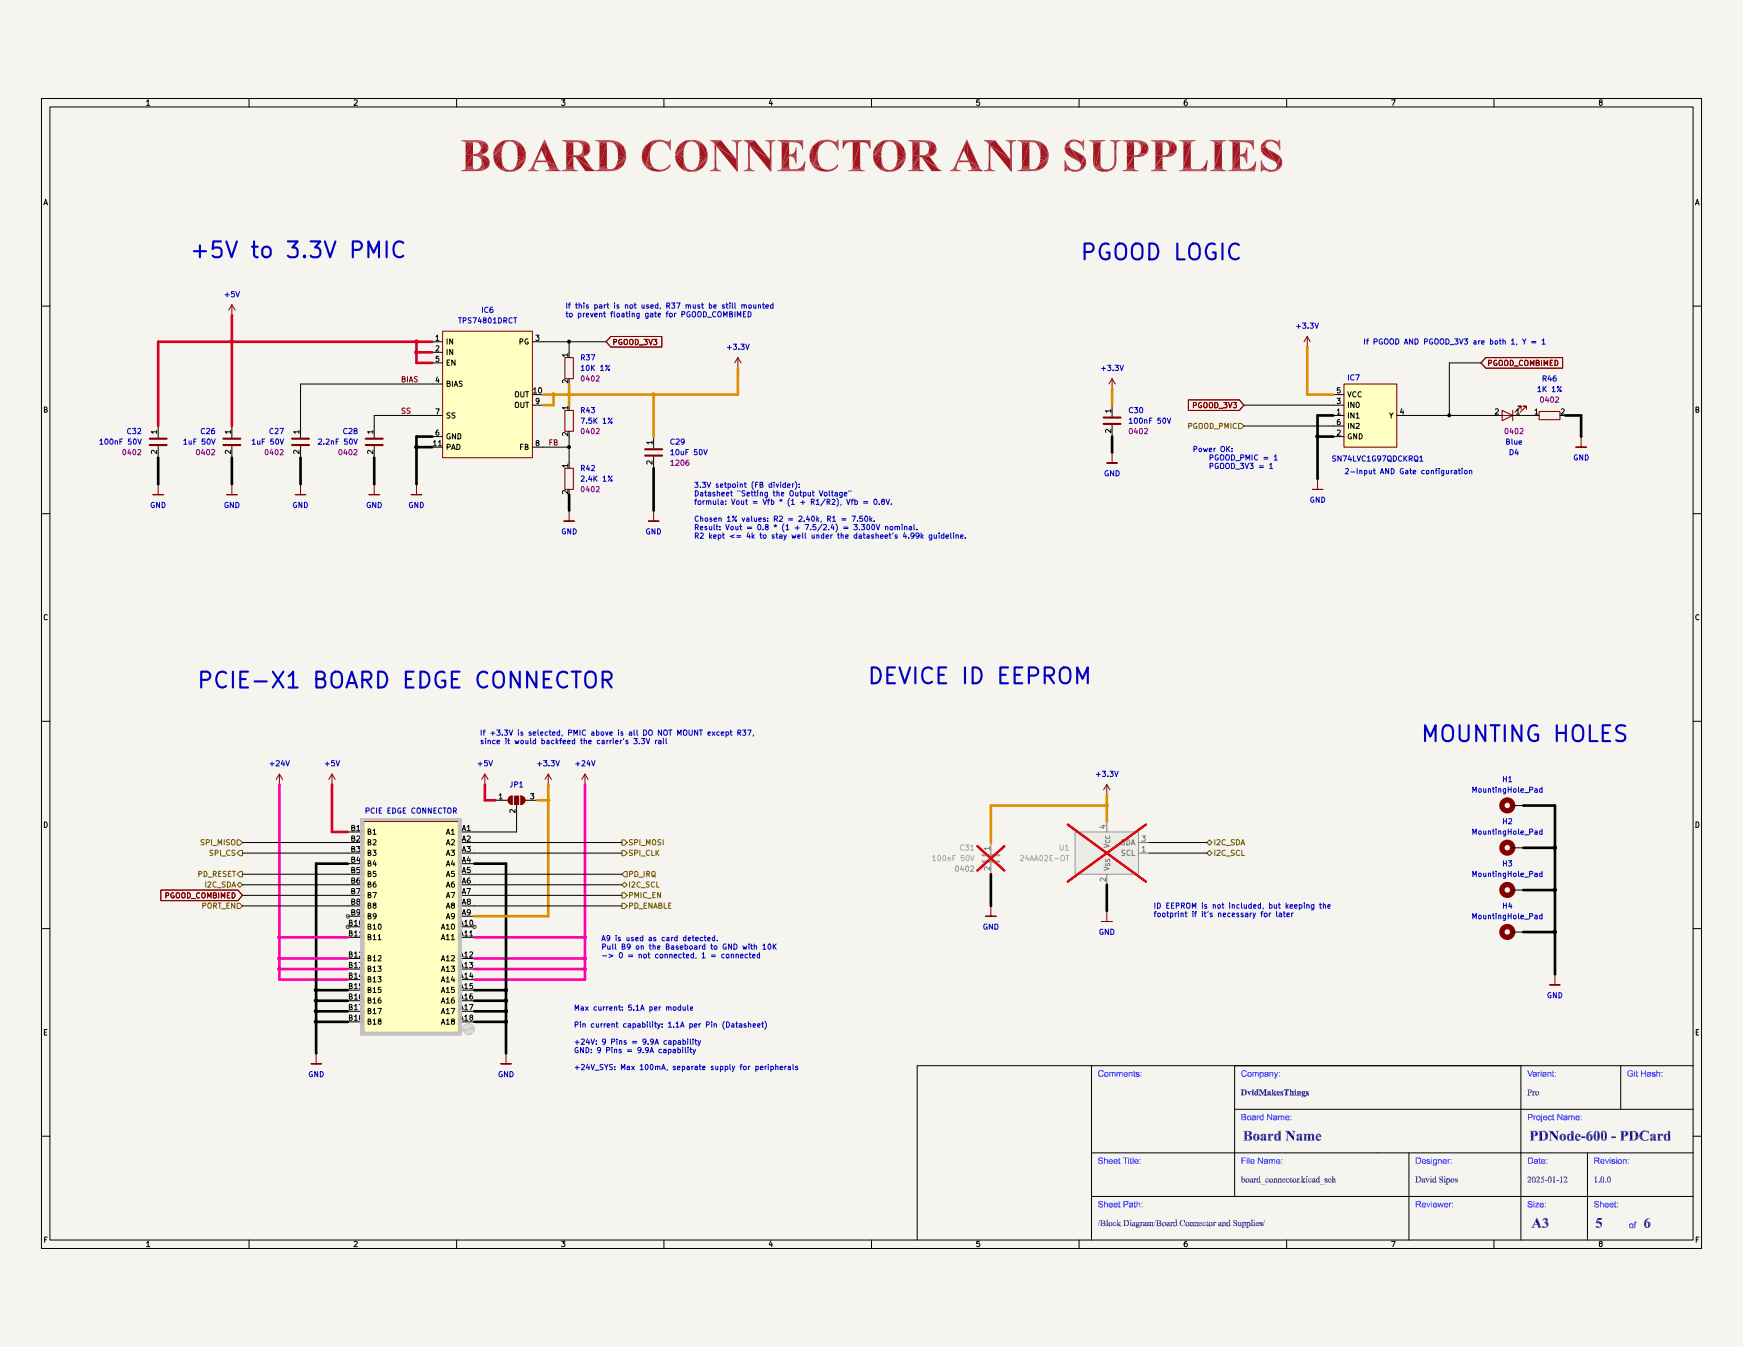
[picture p101: page 5]

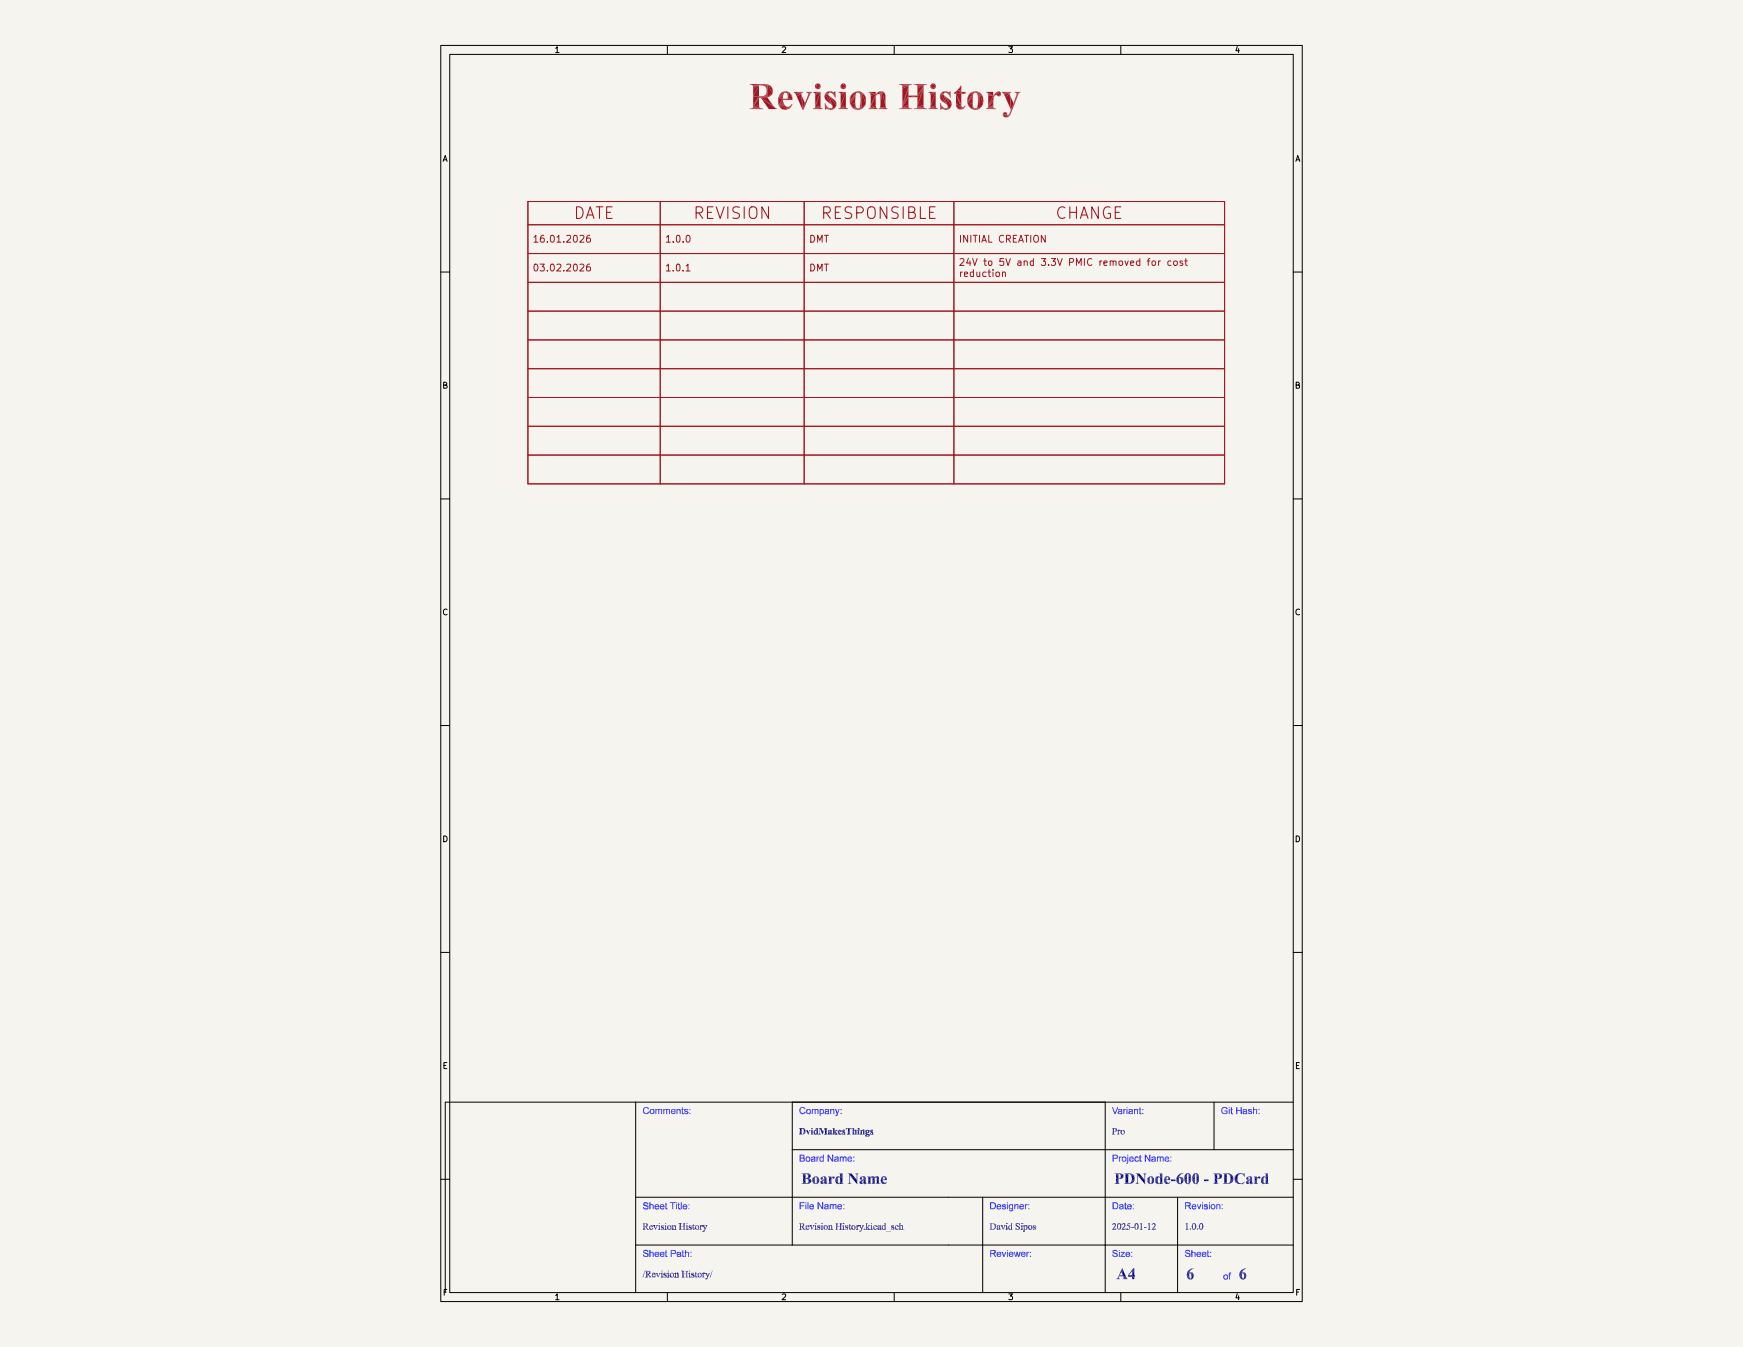
[picture p102: page 6]
