DvidMakesThings/HW_PDNode-600-Pro/src/Software/sample/drivers/button_driver.c

/**
 * @file drivers/button_driver.c
 * @author DvidMakesThings - David Sipos
 *
 * @version 1.1.1
 * @date 2025-12-10
 *
 * @details
 * Implements hardware abstraction for front-panel buttons and selection LEDs.
 * Delegates all I2C operations to SwitchTask to prevent bus contention and
 * ensure thread-safe access to MCP23017 GPIO expanders.
 *
 * Key Design Principles:
 * - Direct GPIO reads for buttons (no I2C, very fast)
 * - All LED operations queued to SwitchTask (non-blocking)
 * - No local state except channel index modifications
 * - Error logging for invalid parameters and queue failures
 *
 * @project ENERGIS - The Managed PDU Project for 10-Inch Rack
 * @github https://github.com/DvidMakesThings/HW_10-In-Rack_PDU
 */

#include "../CONFIG.h"

#define BTNDRV_TAG "[BTNDRV]"

/**
 * @brief Turn off all selection LEDs via SwitchTask.
 *
 * @details
 * Internal helper that delegates to SwitchTask. If SwitchTask is not
 * ready (early boot), LEDs are left unchanged to prevent I2C access
 * before bus initialization.
 *
 * @param None
 * @return None
 */
static inline void drv_sel_all_off(void) {
    if (Switch_IsReady()) {
        (void)Switch_SelectAllOff(0);
    }
}

void ButtonDrv_InitGPIO(void) {
    gpio_init(BUT_PLUS);
    gpio_pull_up(BUT_PLUS);
    gpio_set_dir(BUT_PLUS, false);

    gpio_init(BUT_MINUS);
    gpio_pull_up(BUT_MINUS);
    gpio_set_dir(BUT_MINUS, false);

    gpio_init(BUT_SET);
    gpio_pull_up(BUT_SET);
    gpio_set_dir(BUT_SET, false);

    drv_sel_all_off();
}

bool ButtonDrv_ReadPlus(void) { return gpio_get(BUT_PLUS) ? true : false; }

bool ButtonDrv_ReadMinus(void) { return gpio_get(BUT_MINUS) ? true : false; }

bool ButtonDrv_ReadSet(void) { return gpio_get(BUT_SET) ? true : false; }

void ButtonDrv_SelectAllOff(void) { drv_sel_all_off(); }

void ButtonDrv_SelectShow(uint8_t index, bool on) {
    if (index >= 8u) {
#if ERRORLOGGER
        uint16_t errorcode = ERR_MAKE_CODE(ERR_MOD_BUTTON, ERR_SEV_ERROR, ERR_FID_BUTTON_DRV, 0x0);
        ERROR_PRINT_CODE(errorcode, "%s ButtonDrv_SelectShow: bad index %u\r\n", BTNDRV_TAG,
                         (unsigned)index);
        Storage_EnqueueErrorCode(errorcode);
#endif
        return;
    }

    if (!Switch_IsReady()) {
#if ERRORLOGGER
        uint16_t errorcode = ERR_MAKE_CODE(ERR_MOD_BUTTON, ERR_SEV_ERROR, ERR_FID_BUTTON_DRV, 0x1);
        ERROR_PRINT_CODE(errorcode, "%s ButtonDrv_SelectShow: SwitchTask not ready\r\n",
                         BTNDRV_TAG);
        Storage_EnqueueErrorCode(errorcode);
#endif
        return;
    }

    if (!Switch_SelectShow(index, on, 0)) {
#if ERRORLOGGER
        uint16_t errorcode = ERR_MAKE_CODE(ERR_MOD_BUTTON, ERR_SEV_ERROR, ERR_FID_BUTTON_DRV, 0x2);
        ERROR_PRINT_CODE(errorcode, "%s ButtonDrv_SelectShow: enqueue failed\r\n", BTNDRV_TAG);
        Storage_EnqueueErrorCode(errorcode);
#endif
        return;
    }
}

void ButtonDrv_SelectLeft(uint8_t *io_index, bool led_on) {
    if (!io_index) {
#if ERRORLOGGER
        uint16_t errorcode = ERR_MAKE_CODE(ERR_MOD_BUTTON, ERR_SEV_ERROR, ERR_FID_BUTTON_DRV, 0x3);
        ERROR_PRINT_CODE(errorcode, "%s ButtonDrv_SelectLeft: NULL io_index pointer\r\n",
                         BTNDRV_TAG);
        Storage_EnqueueErrorCode(errorcode);
#endif
        return;
    }

    uint8_t idx = *io_index;
    idx = (idx == 0u) ? 7u : (uint8_t)(idx - 1u);
    *io_index = idx;
    ButtonDrv_SelectShow(idx, led_on);
}

void ButtonDrv_SelectRight(uint8_t *io_index, bool led_on) {
    if (!io_index) {
#if ERRORLOGGER
        uint16_t errorcode = ERR_MAKE_CODE(ERR_MOD_BUTTON, ERR_SEV_ERROR, ERR_FID_BUTTON_DRV, 0x4);
        ERROR_PRINT_CODE(errorcode, "%s ButtonDrv_SelectRight: NULL io_index pointer\r\n",
                         BTNDRV_TAG);
        Storage_EnqueueErrorCode(errorcode);
#endif
        return;
    }

    uint8_t idx = *io_index;
    idx = (idx == 7u) ? 0u : (uint8_t)(idx + 1u);
    *io_index = idx;
    ButtonDrv_SelectShow(idx, led_on);
}

void ButtonDrv_DoSetShort(uint8_t index) {
    if (index < 8) {
        (void)Switch_Toggle(index & 0x07u);
    }
}

void ButtonDrv_DoSetLong(void) {
#ifdef FAULT_LED
    if (Switch_IsReady()) {
        Switch_SetFaultLed(false, 0);
    } else {
        mcp23017_t *disp = mcp_display();
        if (disp) {
            mcp_write_pin(disp, FAULT_LED, 0u);
        }
    }
#endif
}

uint32_t ButtonDrv_NowMs(void) { return (uint32_t)to_ms_since_boot(get_absolute_time()); }
